jeffudall/Team14/images/20171206_204739.jpg

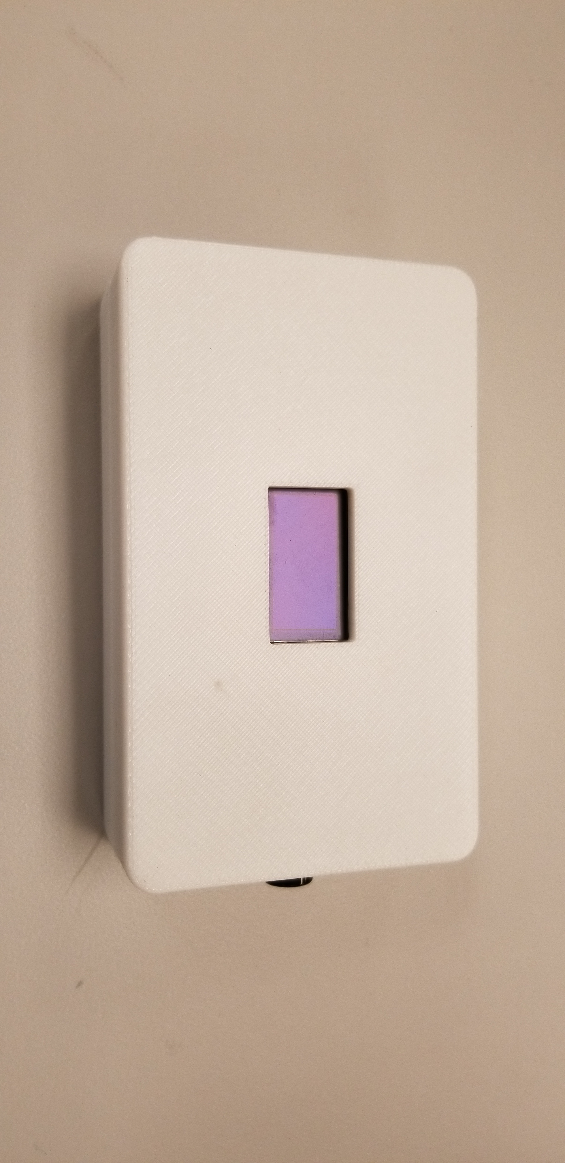
images/20171206_204739.jpg
