jeffudall/Team14/images/20171015_143413.jpg

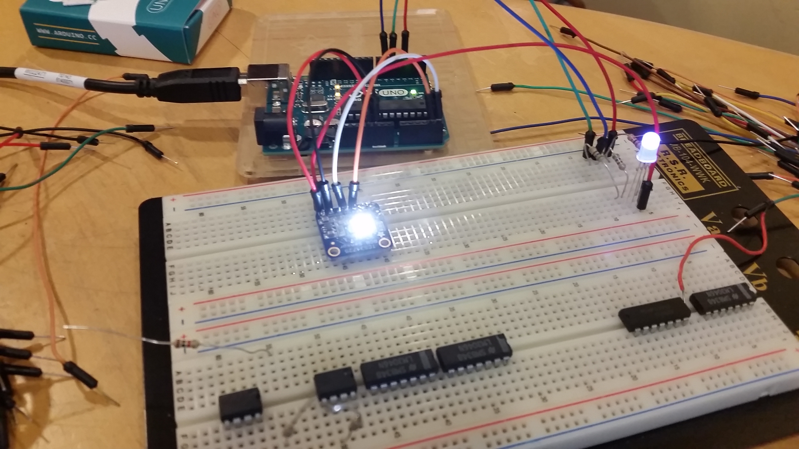
images/20171015_143413.jpg
