jeffudall/Team14/images/20171028_114426.jpg

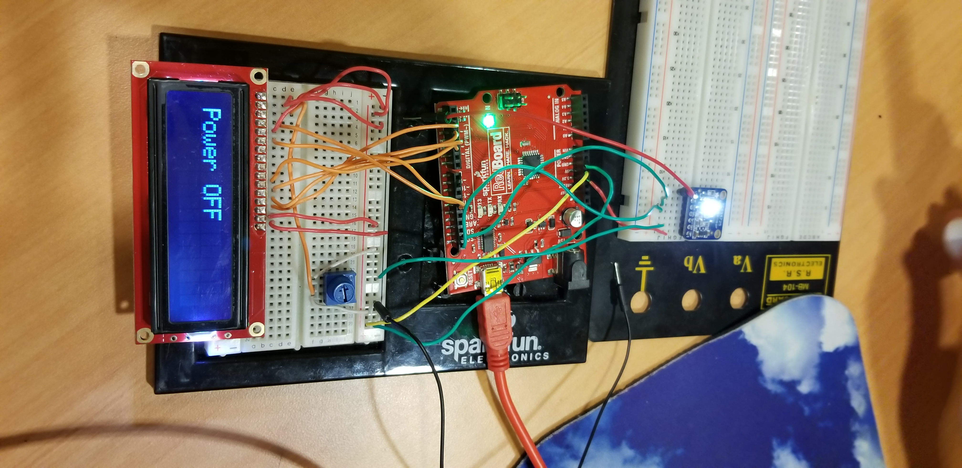
images/20171028_114426.jpg
