jeffudall/Team14/images/20171108_164534.jpg

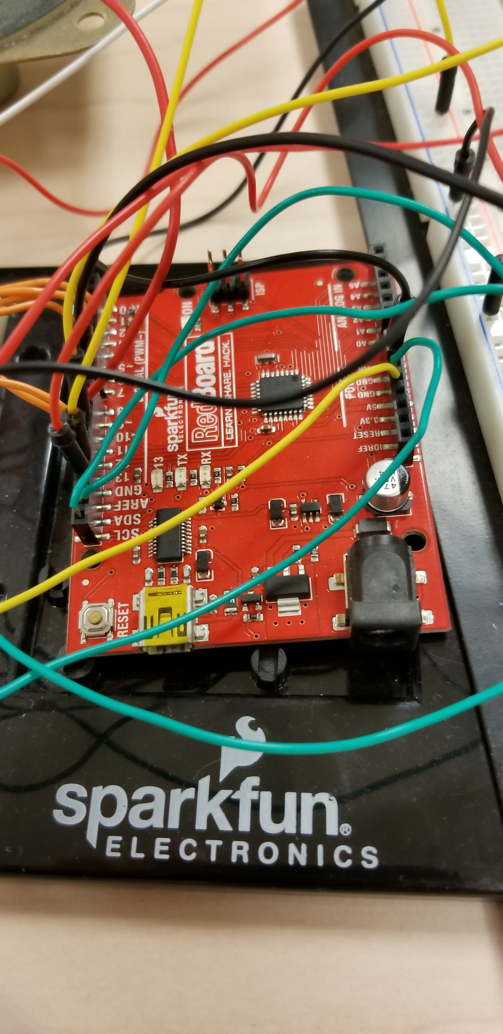
images/20171108_164534.jpg
