jeffudall/Team14/images/20171108_164538.jpg

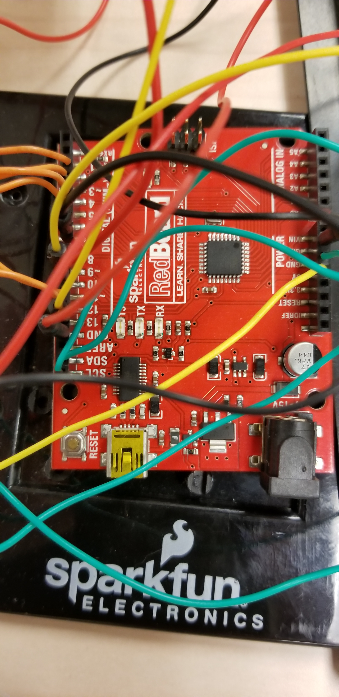
images/20171108_164538.jpg
