jeffudall/Team14/images/20171108_164544.jpg

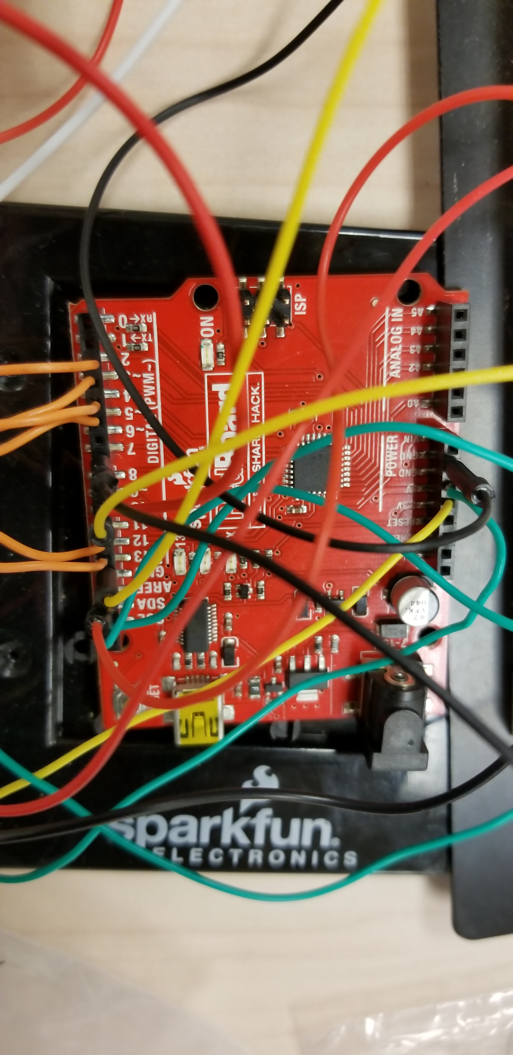
images/20171108_164544.jpg
