jeffudall/Team14/images/20171108_164554.jpg

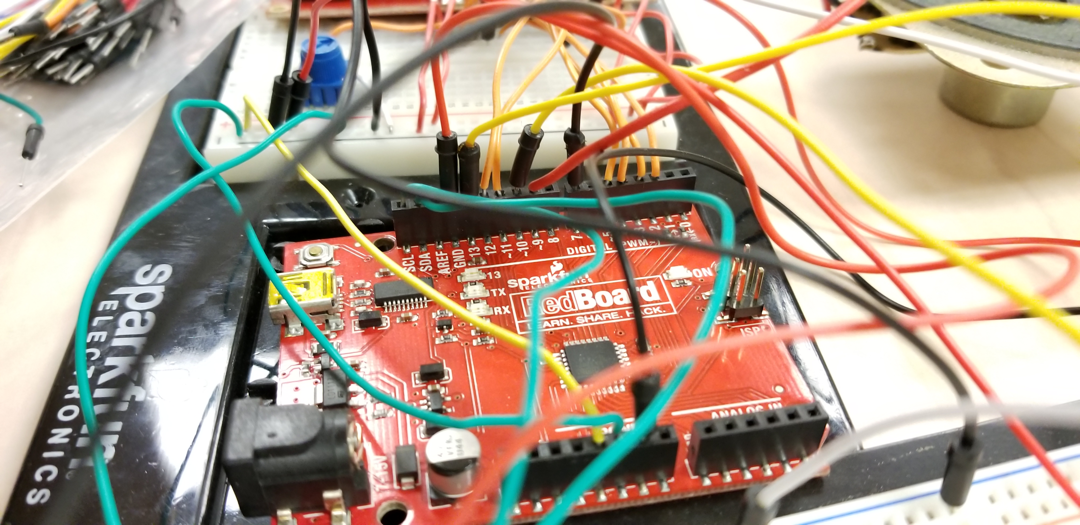
images/20171108_164554.jpg
