jeffudall/Team14/images/20171108_164605.jpg

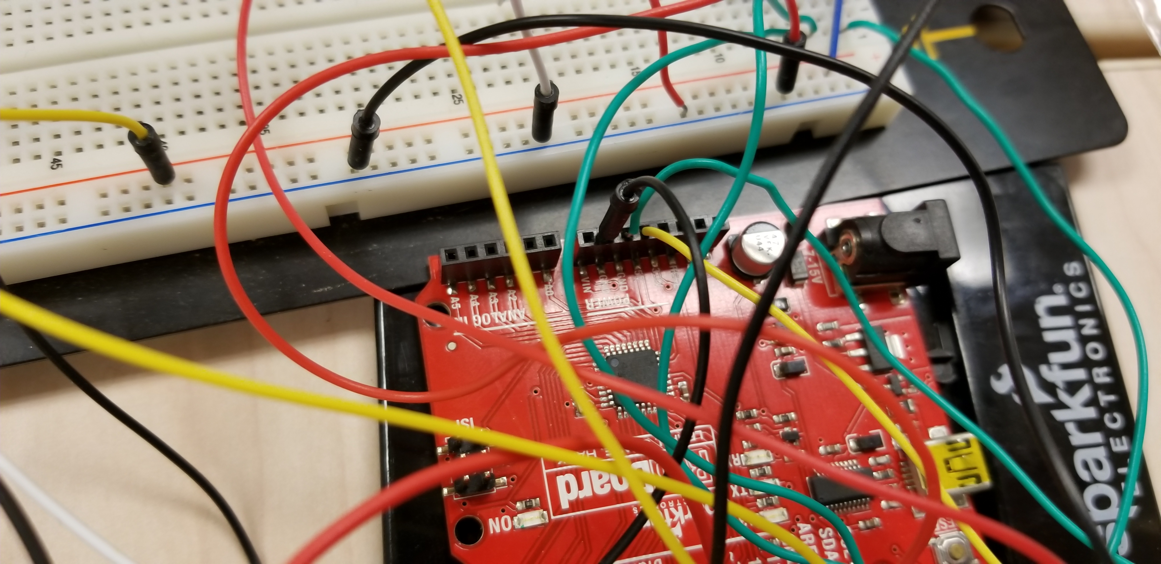
images/20171108_164605.jpg
