jeffudall/Team14/images/20171108_164611.jpg

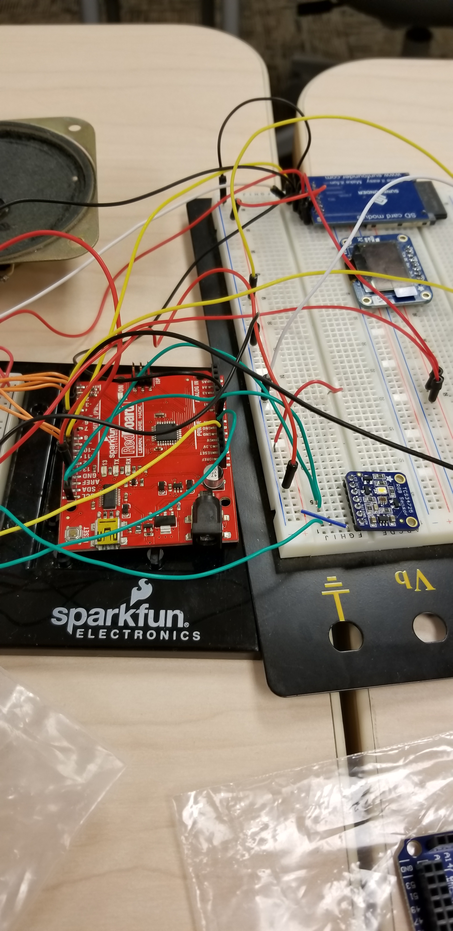
images/20171108_164611.jpg
