jeffudall/Team14/images/20171108_164623.jpg

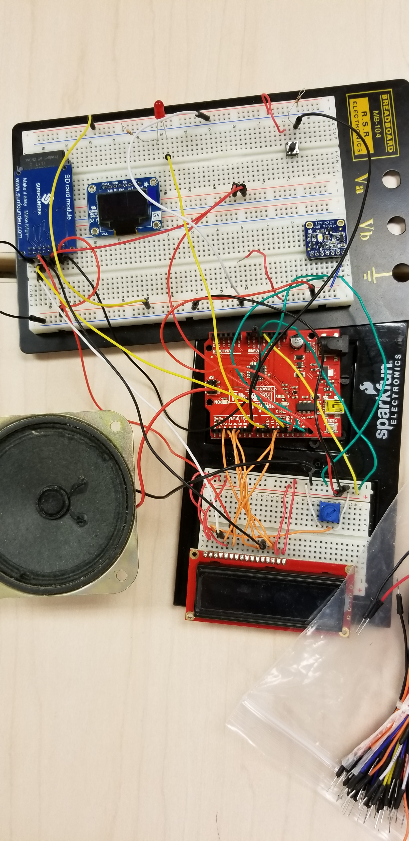
images/20171108_164623.jpg
