jeffudall/Team14/images/20171108_164629.jpg

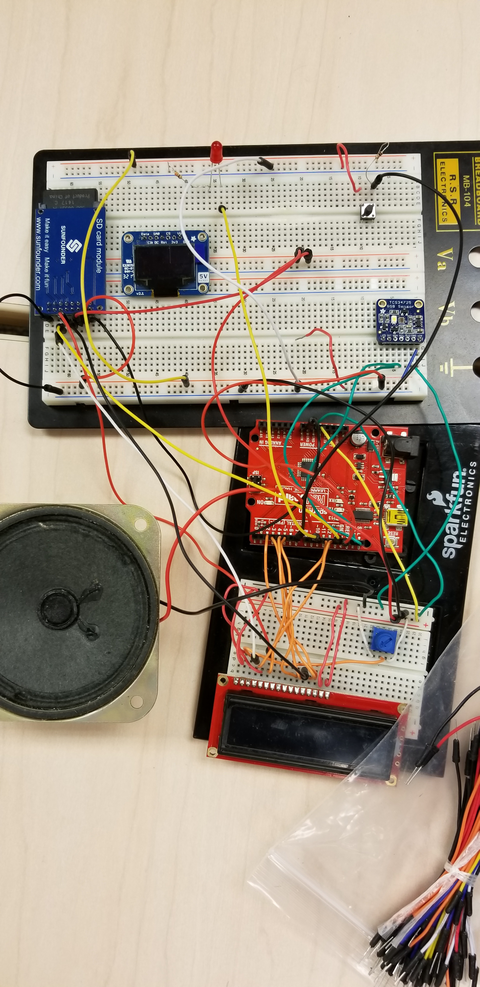
images/20171108_164629.jpg
