jeffudall/Team14/images/20171108_173020.jpg

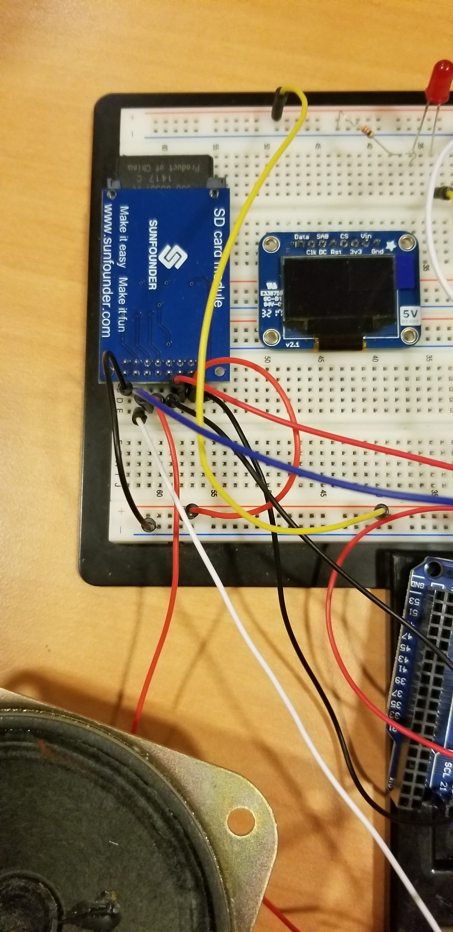
images/20171108_173020.jpg
