jeffudall/Team14/images/20171108_173022.jpg

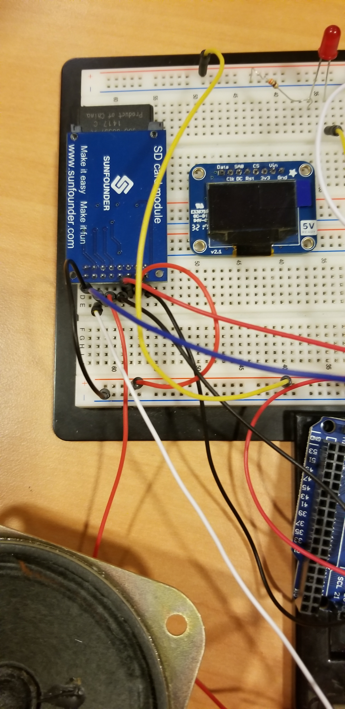
images/20171108_173022.jpg
