jeffudall/Team14/images/20171108_173024.jpg

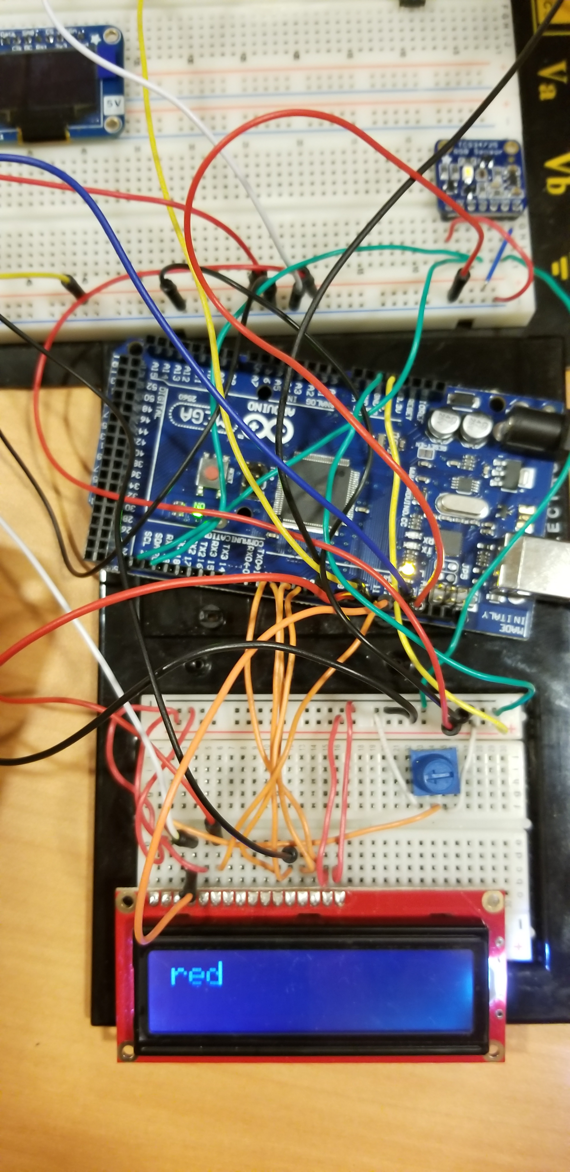
images/20171108_173024.jpg
