jeffudall/Team14/images/20171108_173028.jpg

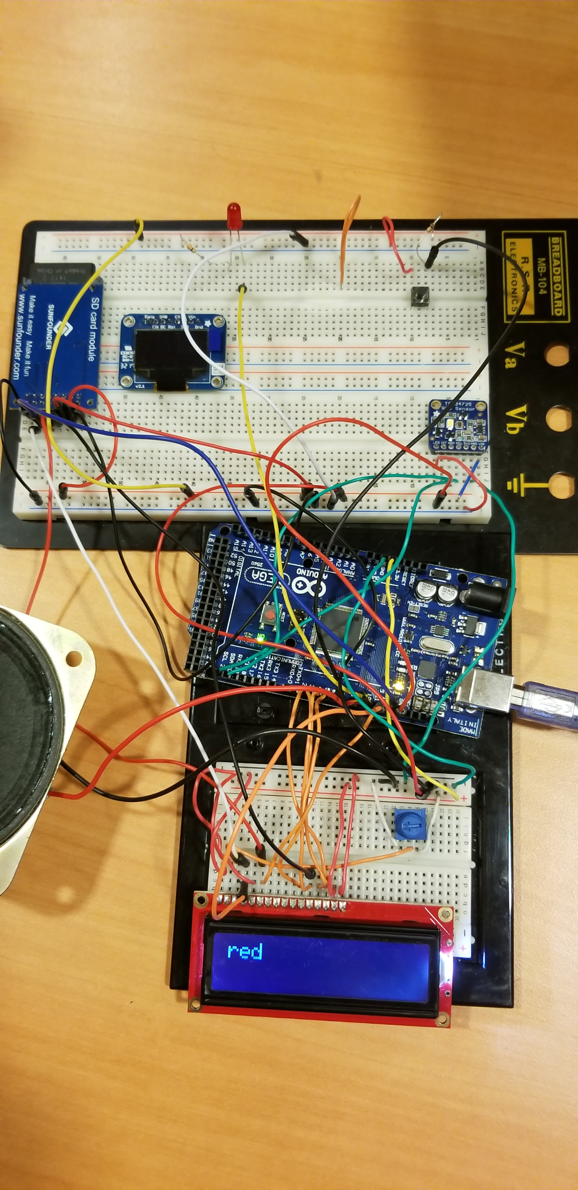
images/20171108_173028.jpg
