jeffudall/Team14/images/20171122_153738.jpg

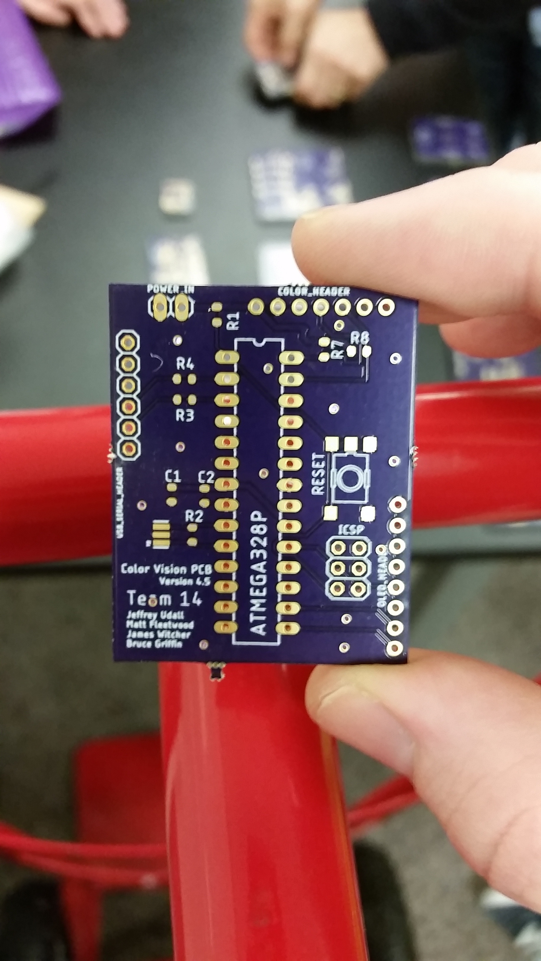
images/20171122_153738.jpg
