jeffudall/Team14/images/20171201_123741.jpg

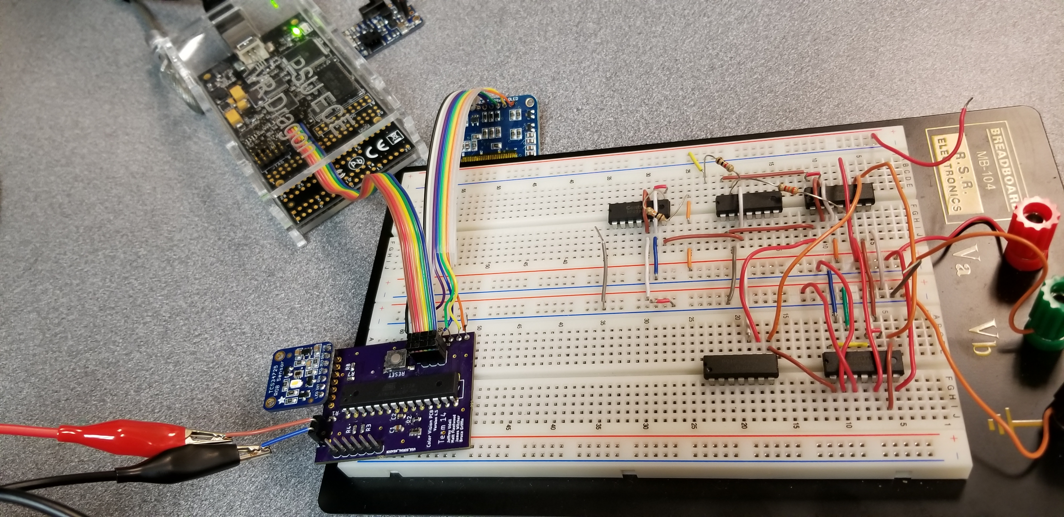
images/20171201_123741.jpg
