jeffudall/Team14/images/20171201_123743.jpg

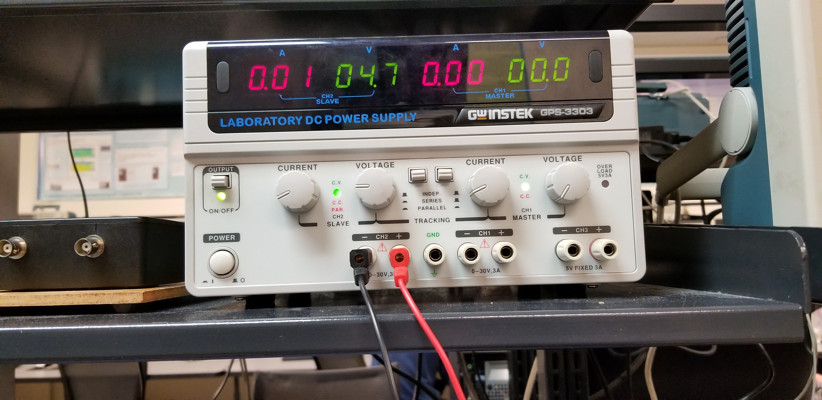
images/20171201_123743.jpg
