jeffudall/Team14/images/20171201_124440.jpg

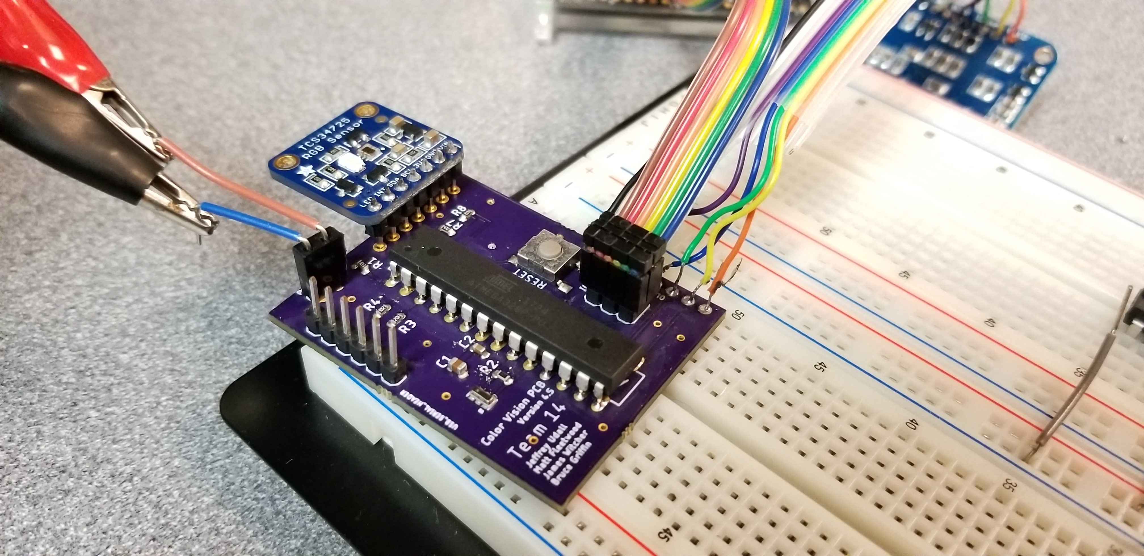
images/20171201_124440.jpg
