jeffudall/Team14/images/20171201_124449.jpg

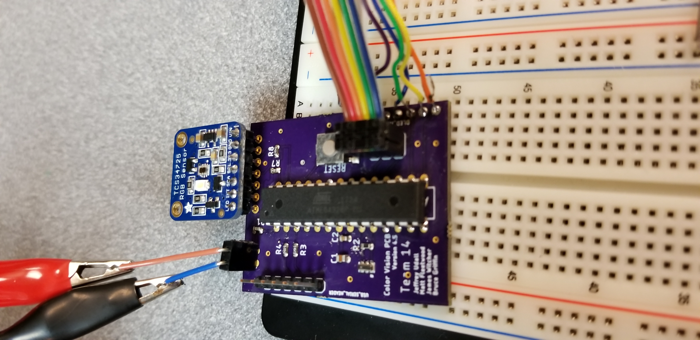
images/20171201_124449.jpg
