jeffudall/Team14/images/20171201_124454.jpg

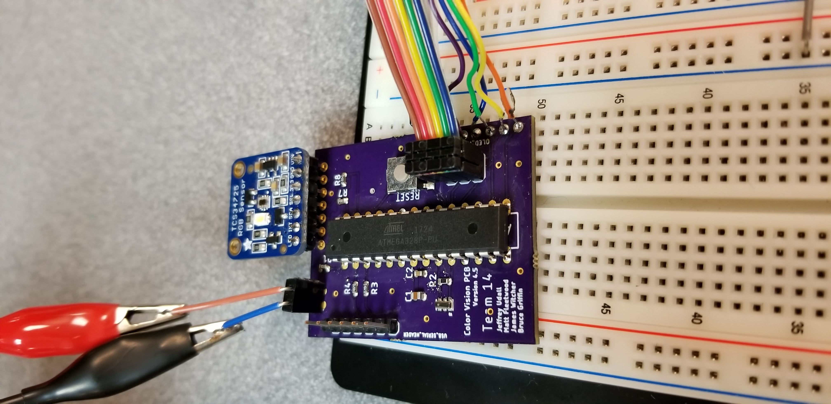
images/20171201_124454.jpg
