jeffudall/Team14/images/20171201_124501.jpg

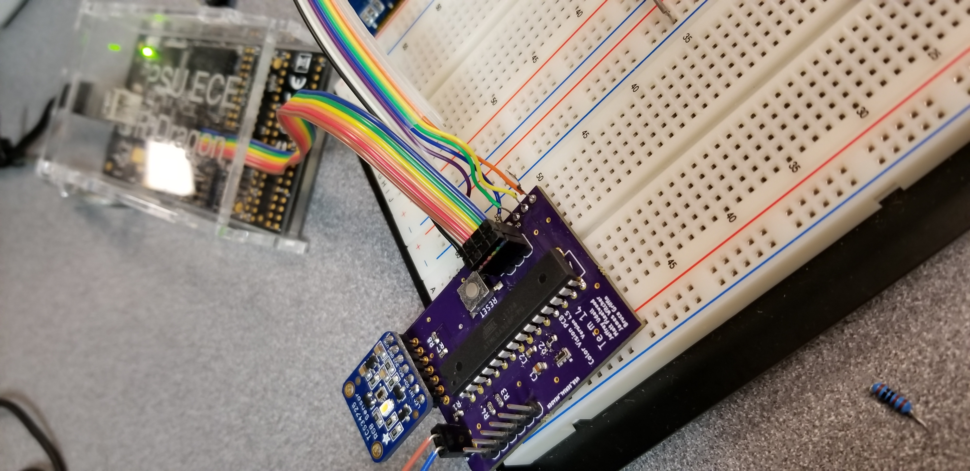
images/20171201_124501.jpg
