jeffudall/Team14/images/20171201_124509.jpg

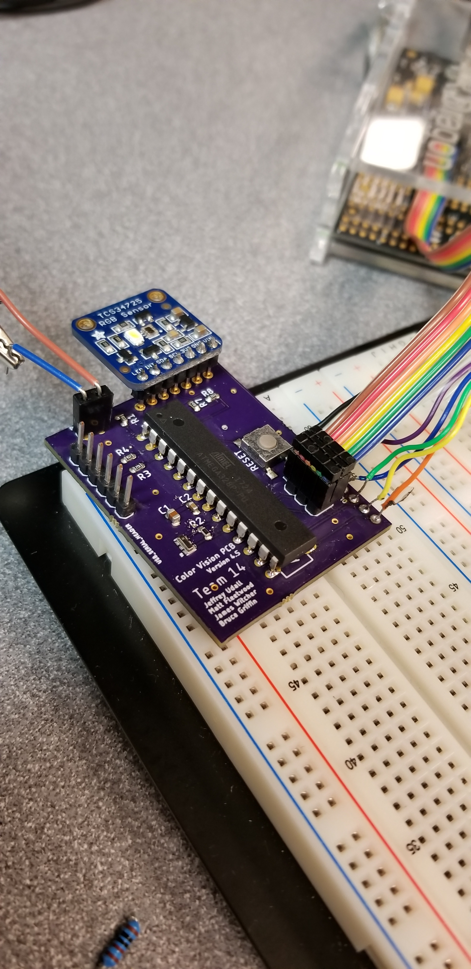
images/20171201_124509.jpg
