jeffudall/Team14/images/20171201_125054.jpg

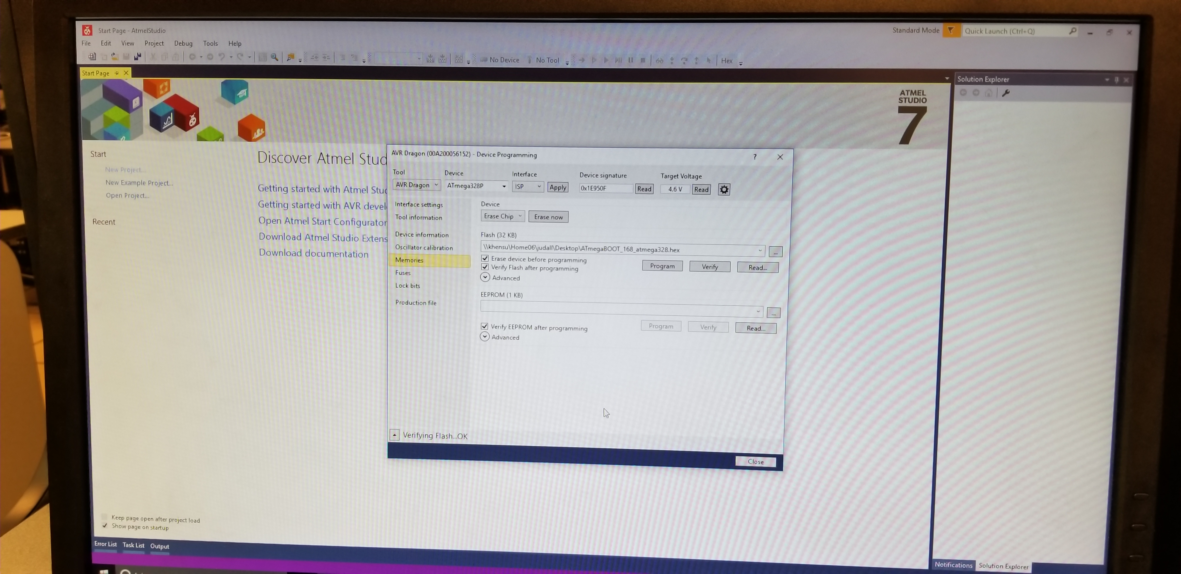
images/20171201_125054.jpg
