jeffudall/Team14/images/20171201_125115.jpg

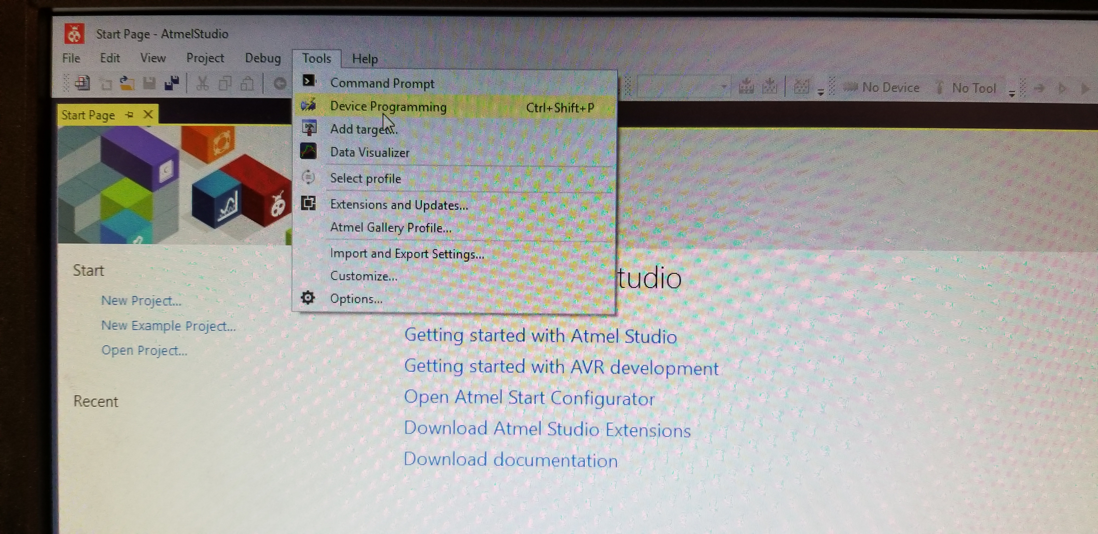
images/20171201_125115.jpg
