jeffudall/Team14/images/20171201_125118.jpg

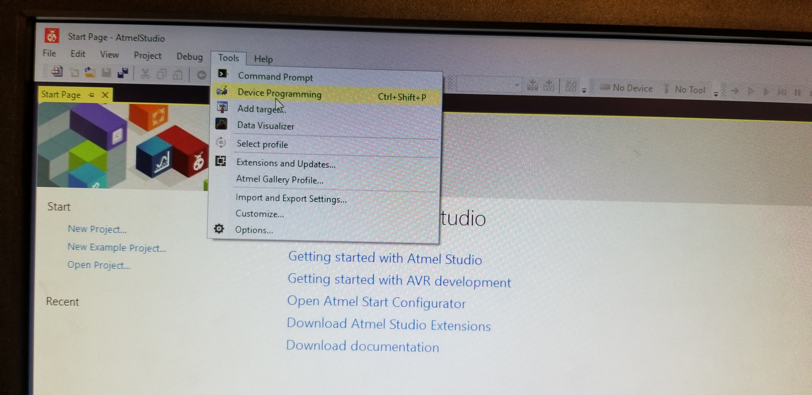
images/20171201_125118.jpg
