jeffudall/Team14/images/20171201_192157.jpg

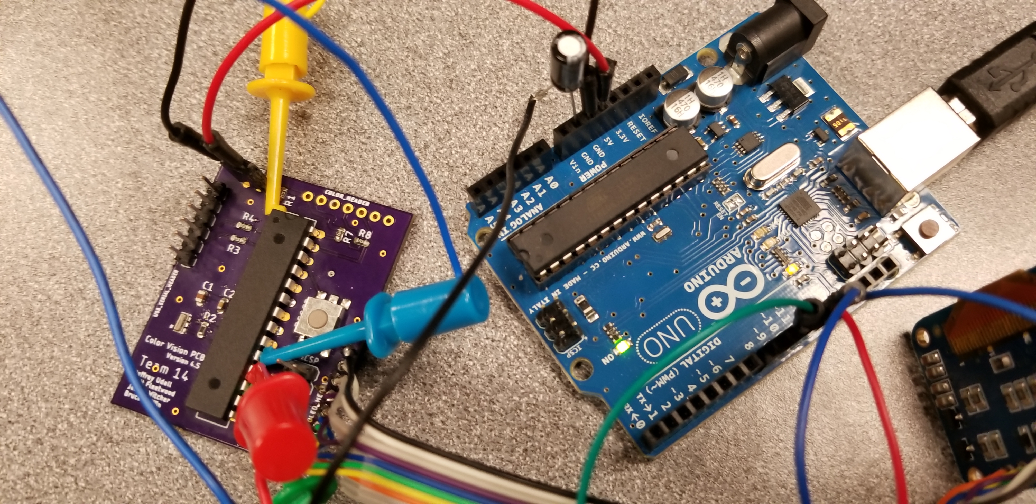
images/20171201_192157.jpg
