jeffudall/Team14/images/20171201_192206.jpg

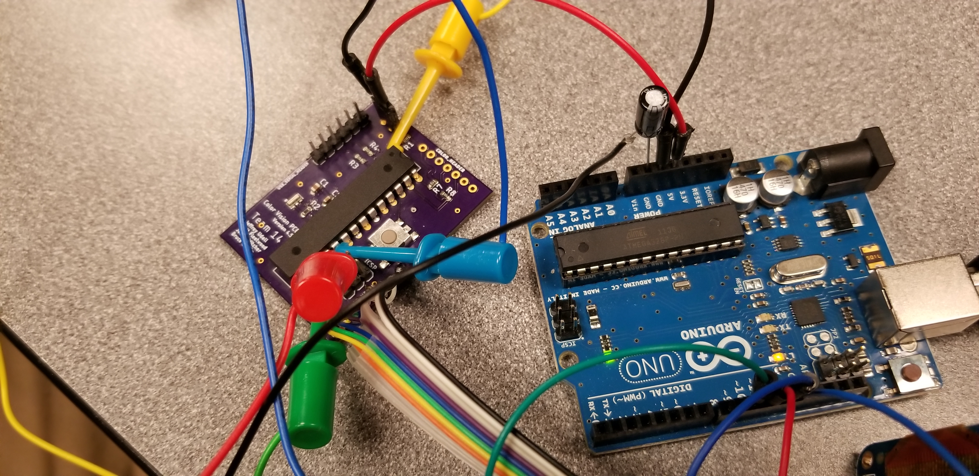
images/20171201_192206.jpg
