jeffudall/Team14/images/20171201_192208.jpg

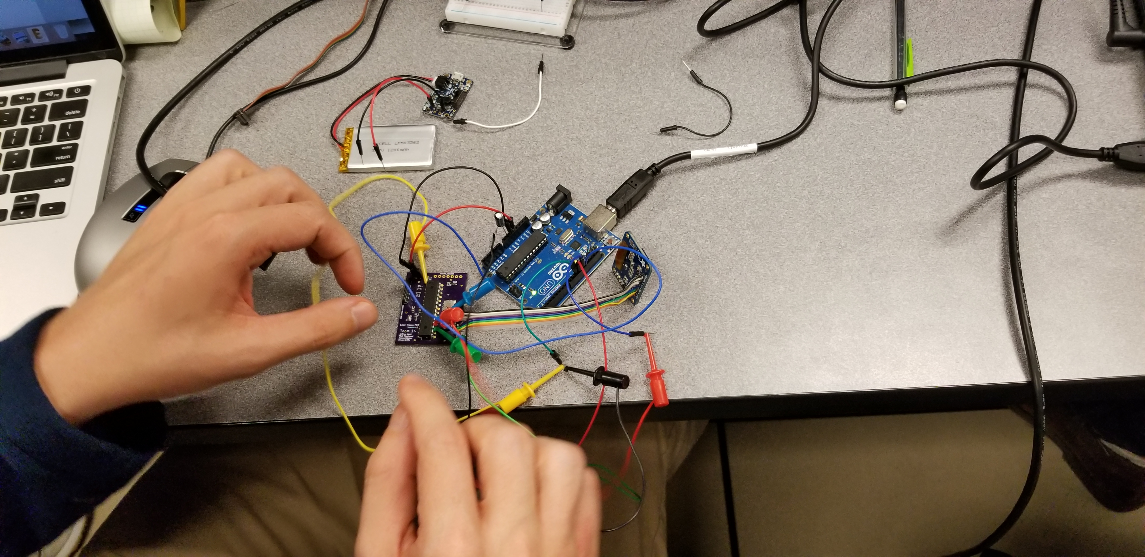
images/20171201_192208.jpg
