jeffudall/Team14/images/20171201_194534.jpg

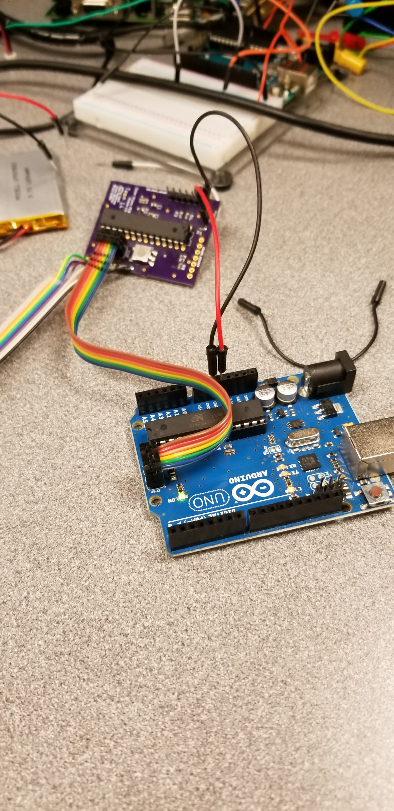
images/20171201_194534.jpg
