jeffudall/Team14/images/20171203_112600.jpg

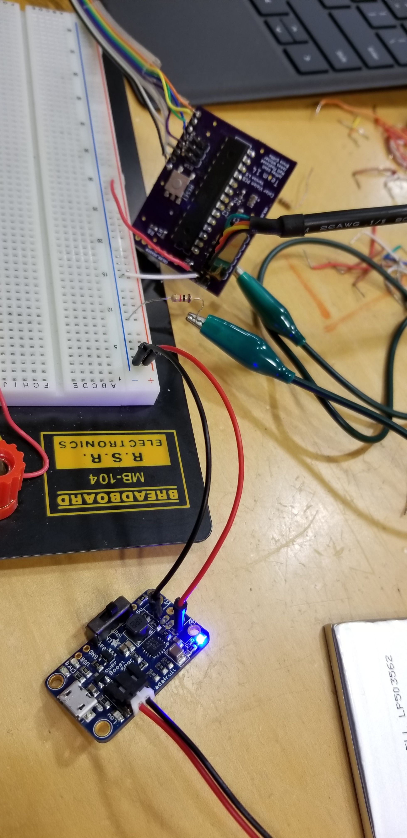
images/20171203_112600.jpg
