jeffudall/Team14/images/20171203_112827.jpg

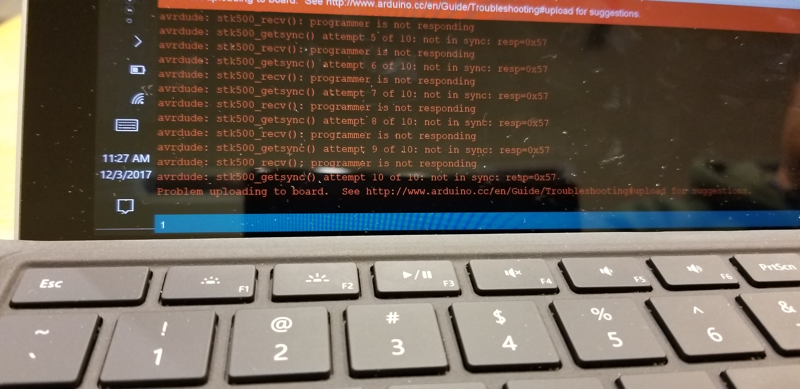
images/20171203_112827.jpg
