jeffudall/Team14/images/20171203_142456.jpg

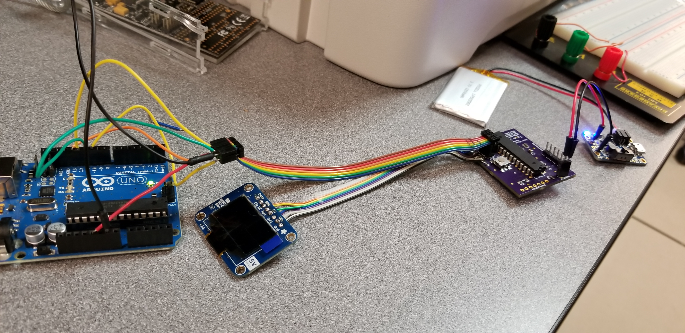
images/20171203_142456.jpg
