jeffudall/Team14/images/20171203_142506.jpg

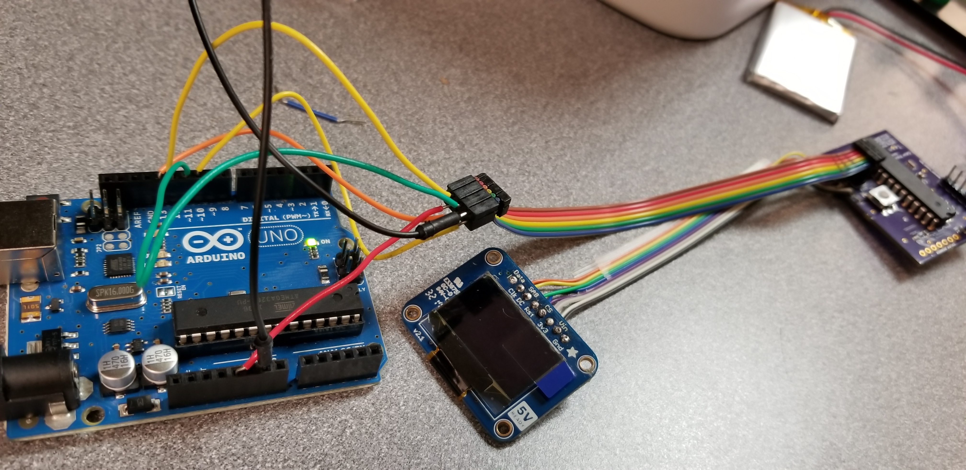
images/20171203_142506.jpg
