jeffudall/Team14/images/20171203_142516.jpg

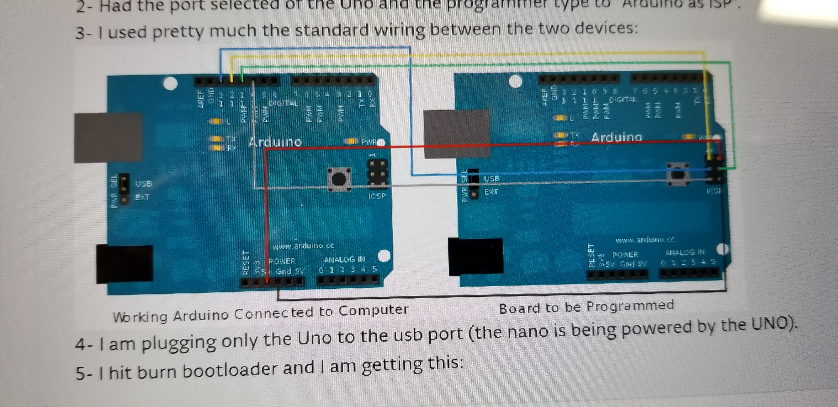
images/20171203_142516.jpg
