jeffudall/Team14/images/20171203_143118.jpg

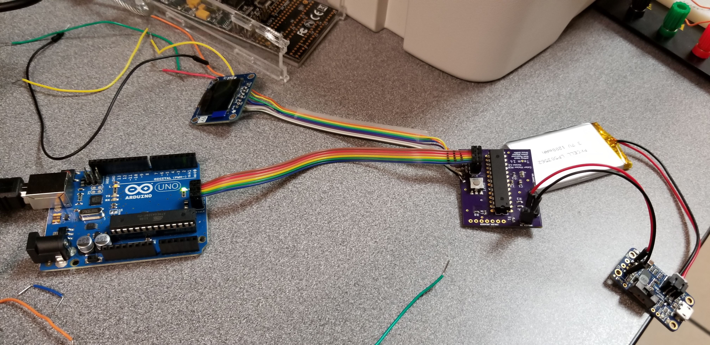
images/20171203_143118.jpg
