jeffudall/Team14/images/20171203_143120.jpg

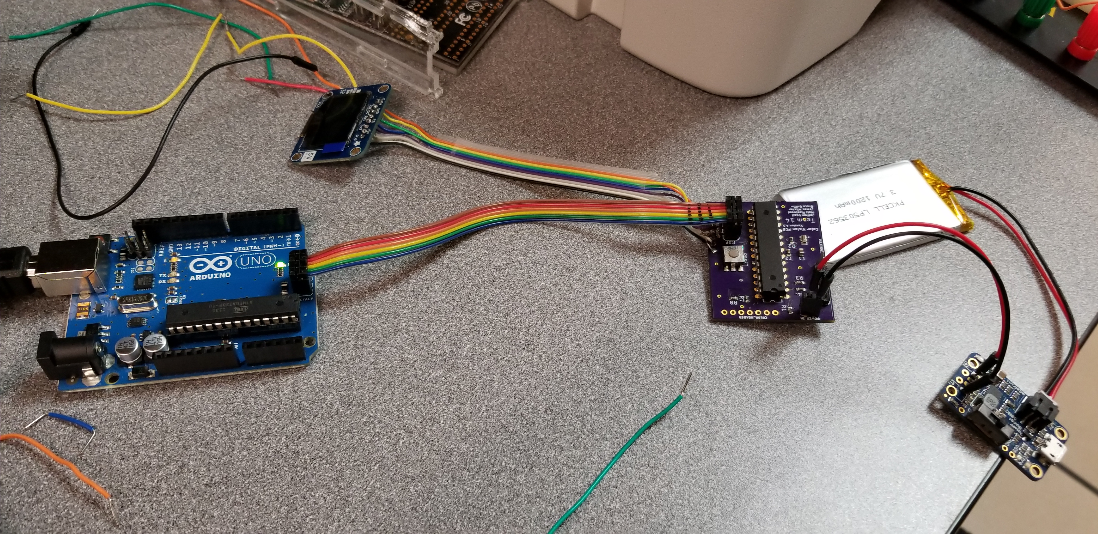
images/20171203_143120.jpg
