jeffudall/Team14/images/20171203_143124.jpg

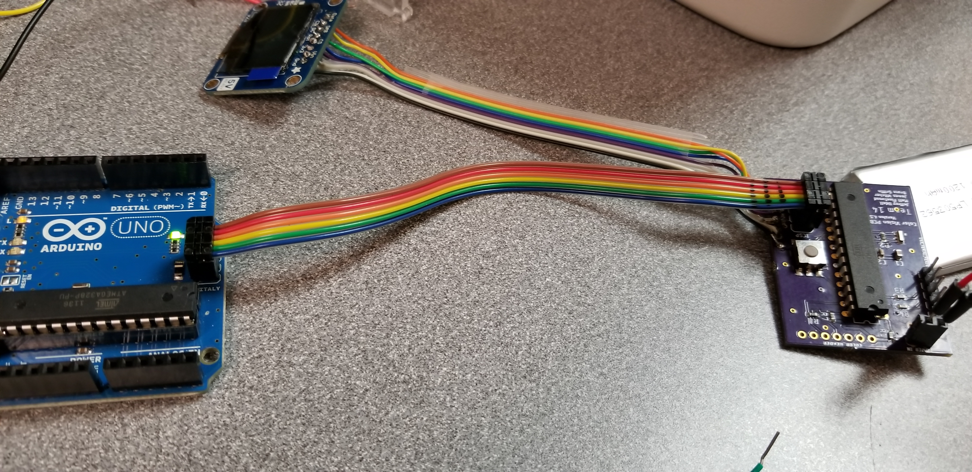
images/20171203_143124.jpg
