jeffudall/Team14/images/20171205_124026.jpg

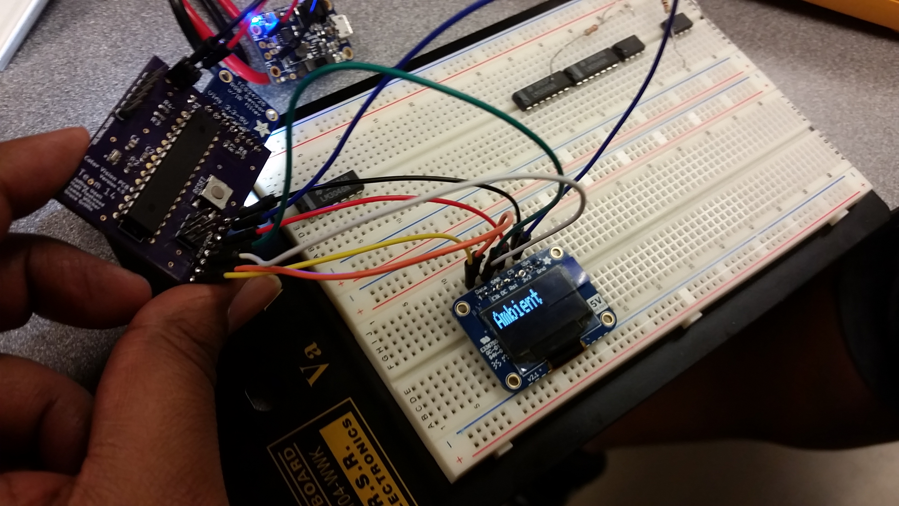
images/20171205_124026.jpg
