jeffudall/Team14/images/20171205_190306.jpg

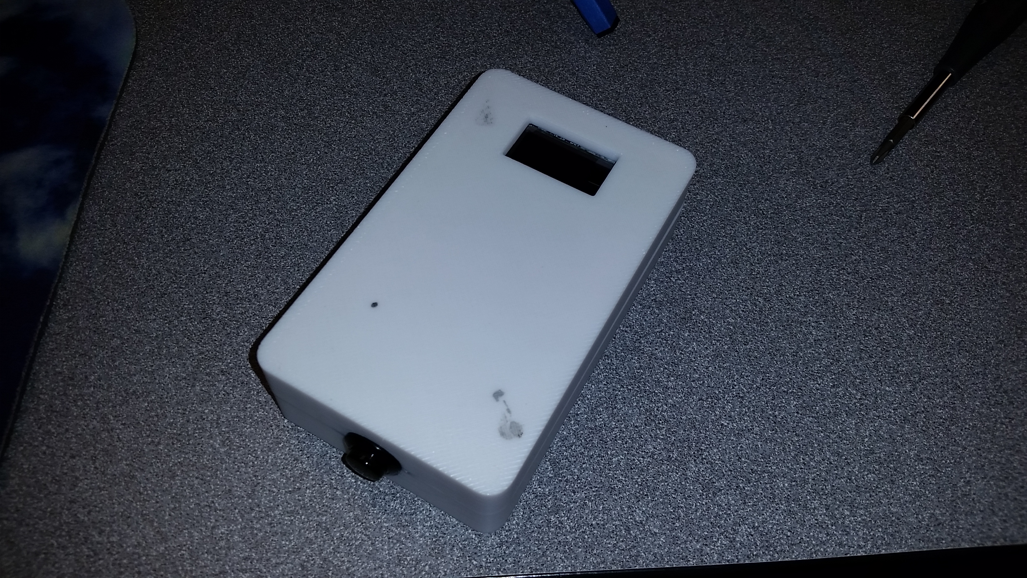
images/20171205_190306.jpg
