jeffudall/Team14/images/20171206_204804.jpg

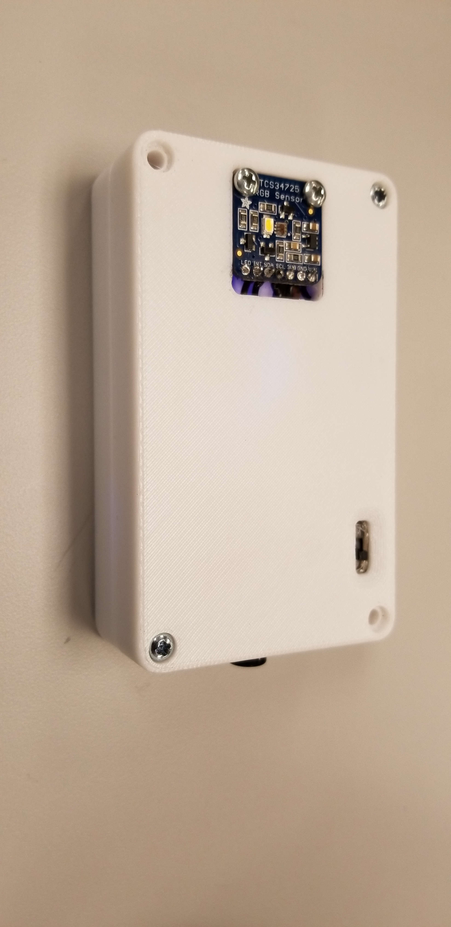
images/20171206_204804.jpg
