jeffudall/Team14/images/20171206_204812.jpg

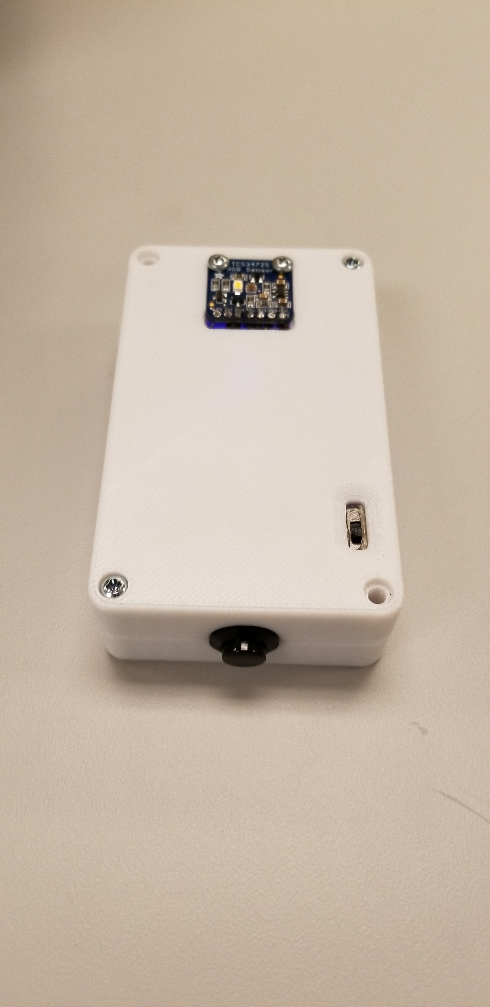
images/20171206_204812.jpg
