jeffudall/Team14/images/ATMEGA328chip.JPG

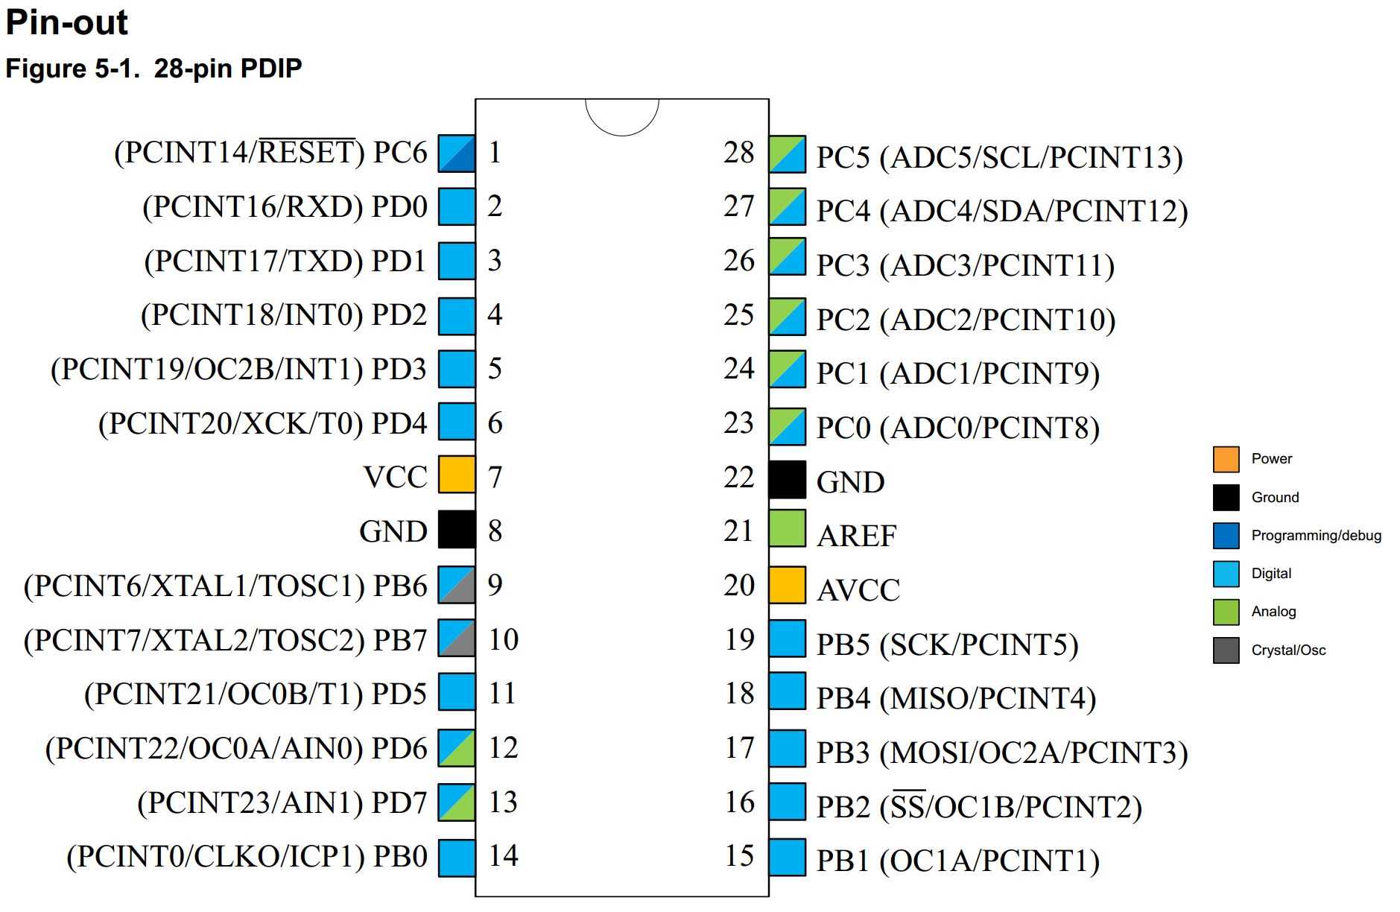
images/ATMEGA328chip.JPG
