jeffudall/Team14/images/blue.jpg

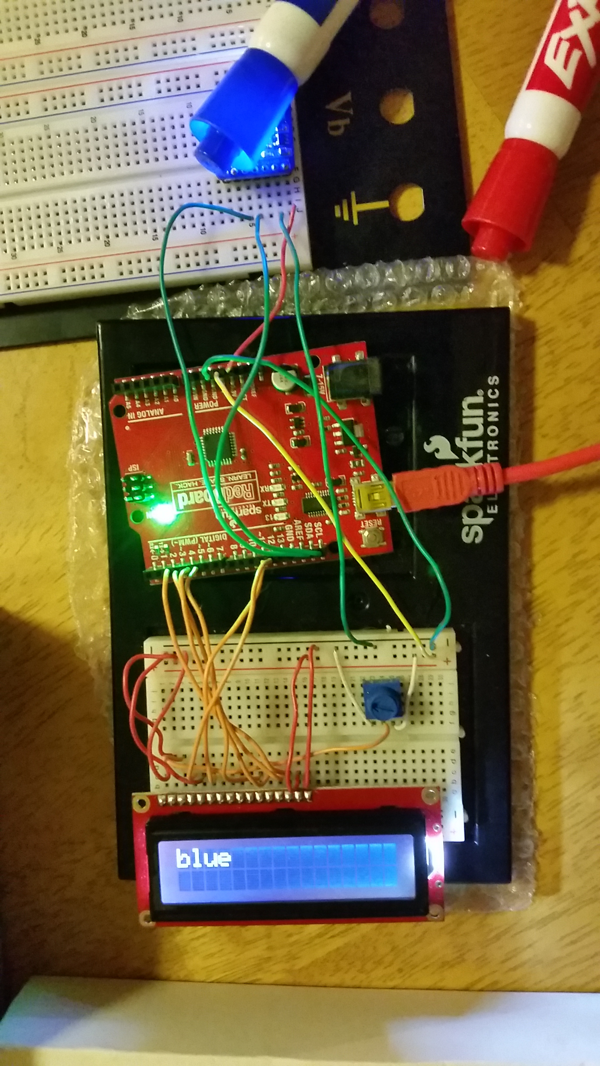
images/blue.jpg
