jeffudall/Team14/images/BoM_final.png

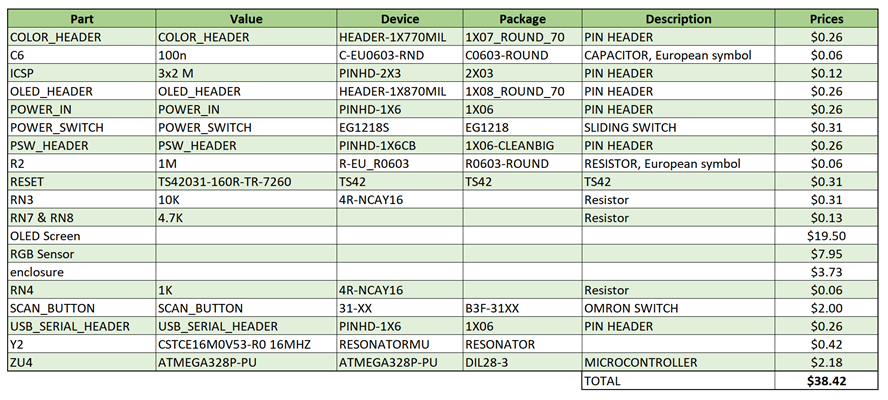
images/BoM_final.png
