jeffudall/Team14/images/cmd_line_audio.png

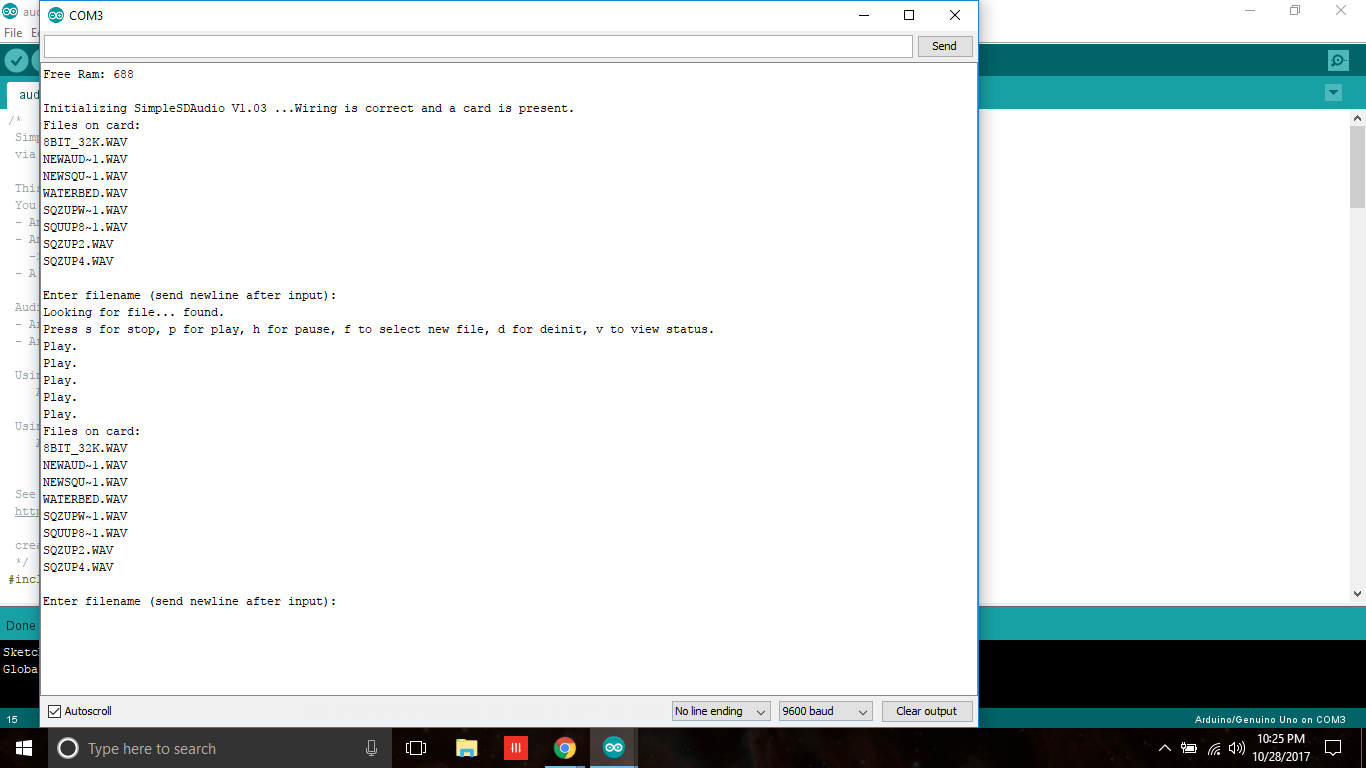
images/cmd_line_audio.png
