jeffudall/Team14/images/color_chooser_sketch.PNG

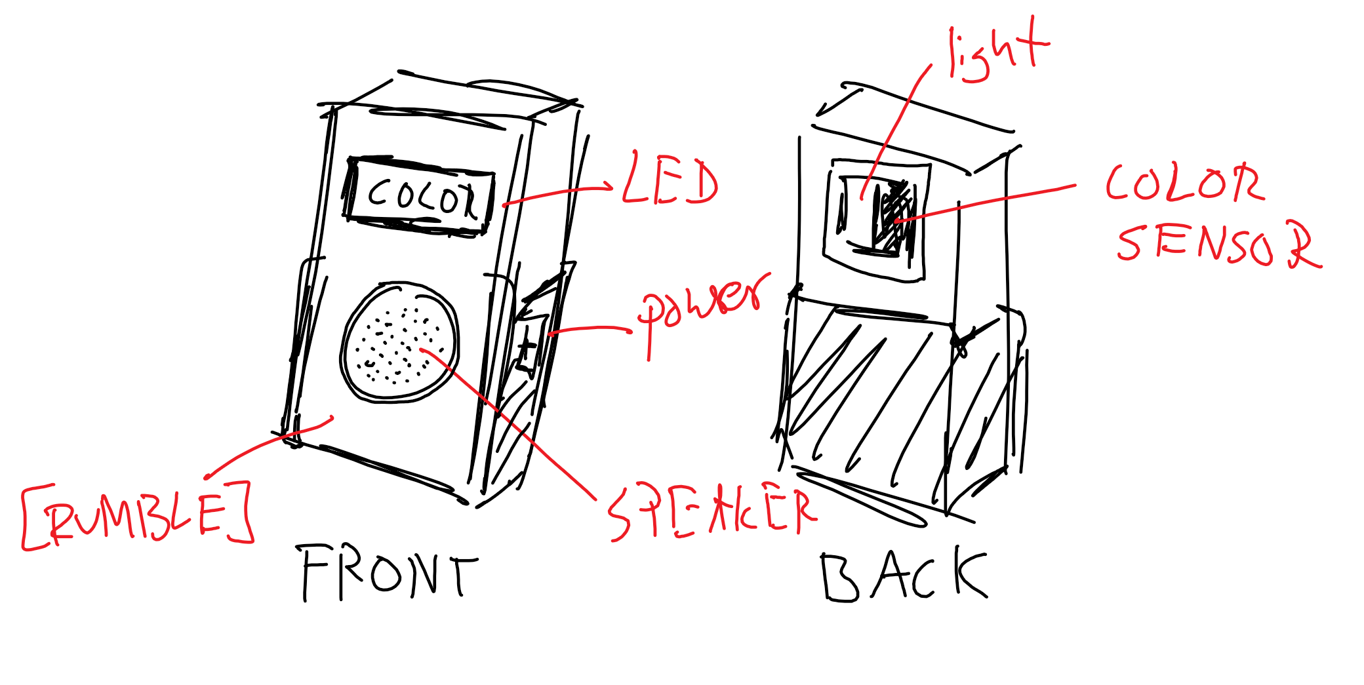
images/color_chooser_sketch.PNG
