jeffudall/Team14/images/color_sensor.JPG

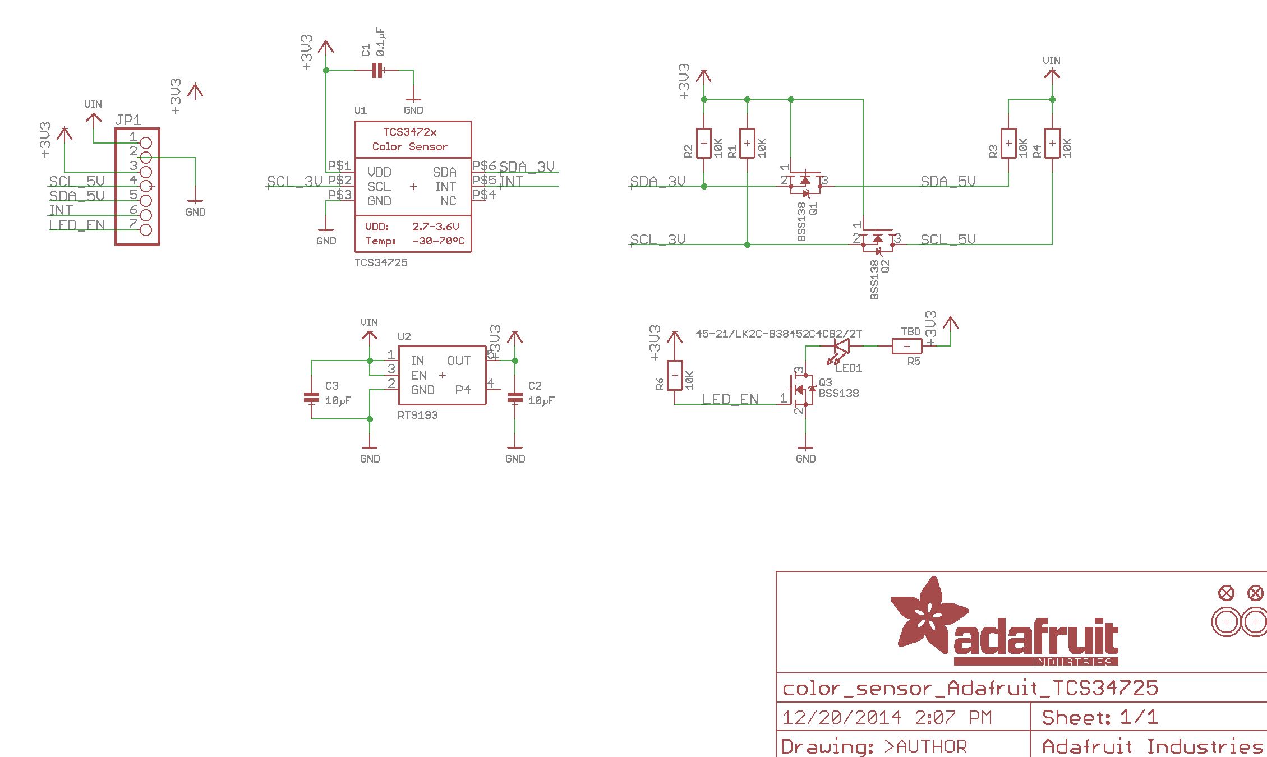
images/color_sensor.JPG
