jeffudall/Team14/images/Enclosure Sensor side V1.JPG

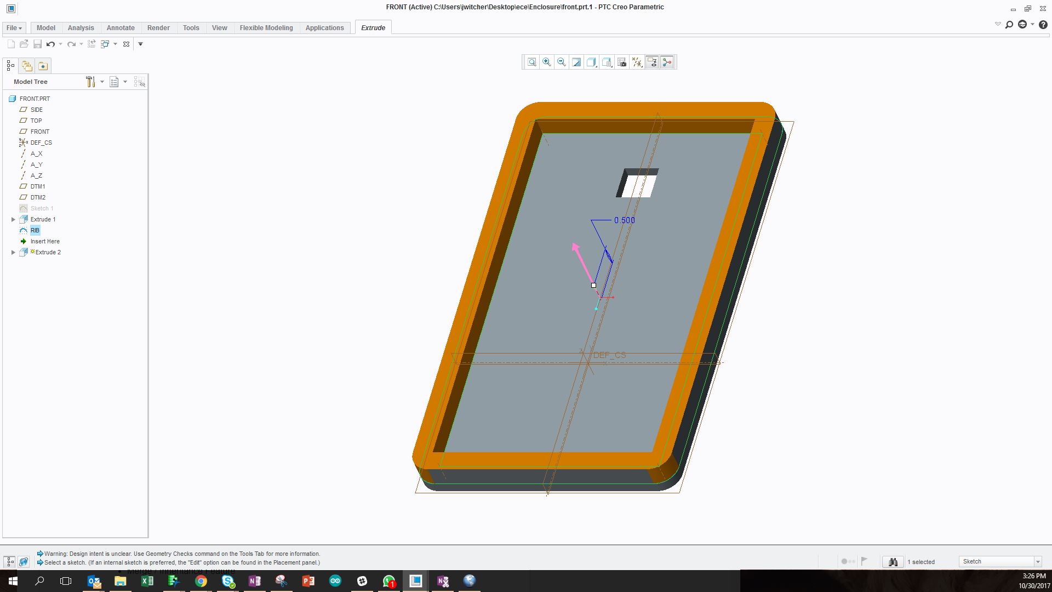
images/Enclosure Sensor side V1.JPG
