jeffudall/Team14/images/Enclosure Speaker_LCD V1.JPG

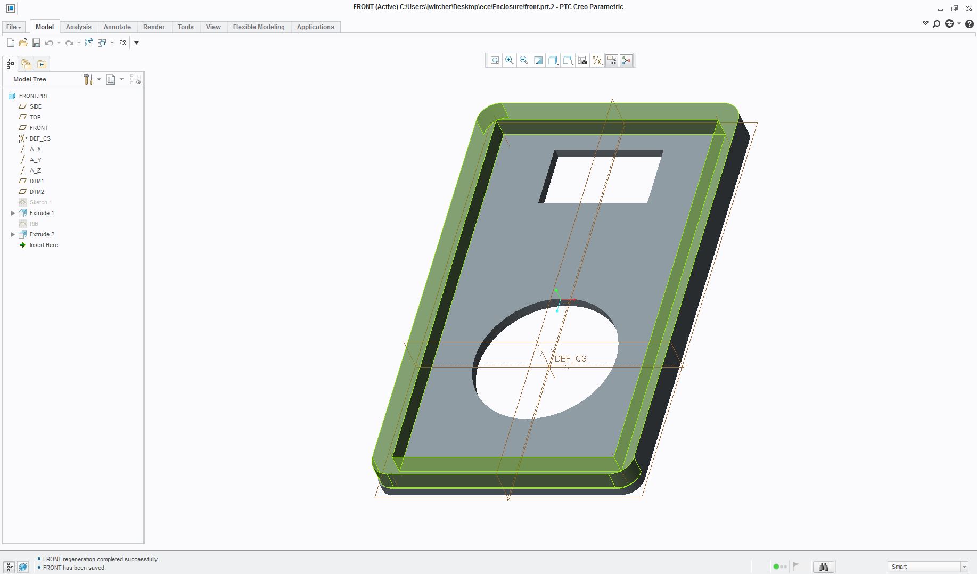
images/Enclosure Speaker_LCD V1.JPG
