jeffudall/Team14/images/enclosure_back_V2.JPG

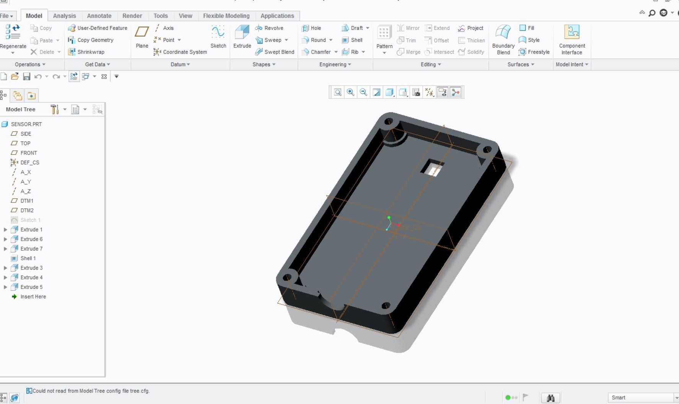
images/enclosure_back_V2.JPG
