jeffudall/Team14/images/enclosure_front_V2.JPG

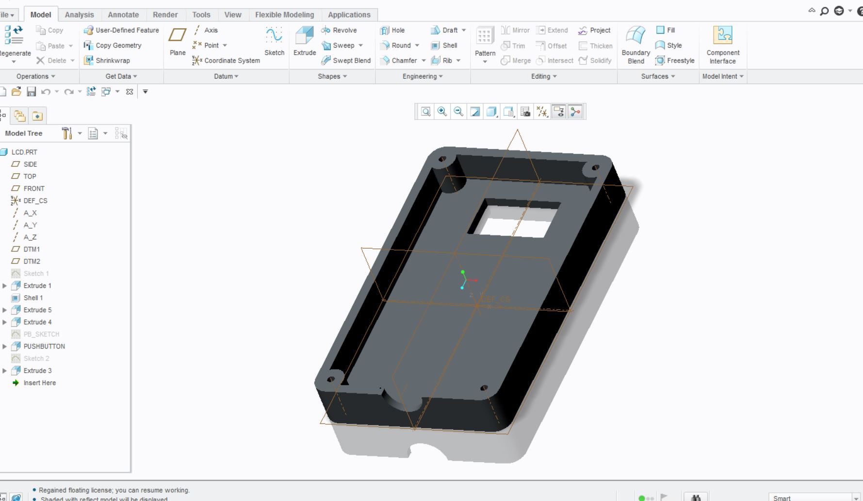
images/enclosure_front_V2.JPG
