jeffudall/Team14/images/final_device_01.JPG

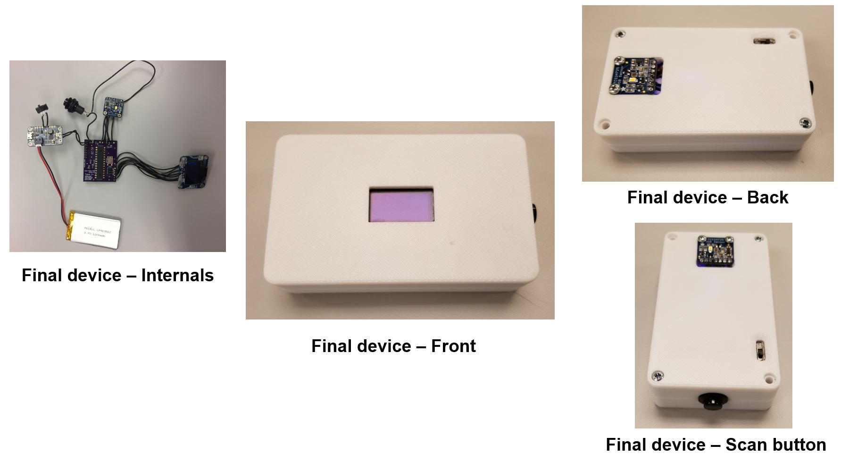
images/final_device_01.JPG
