jeffudall/Team14/images/green.jpg

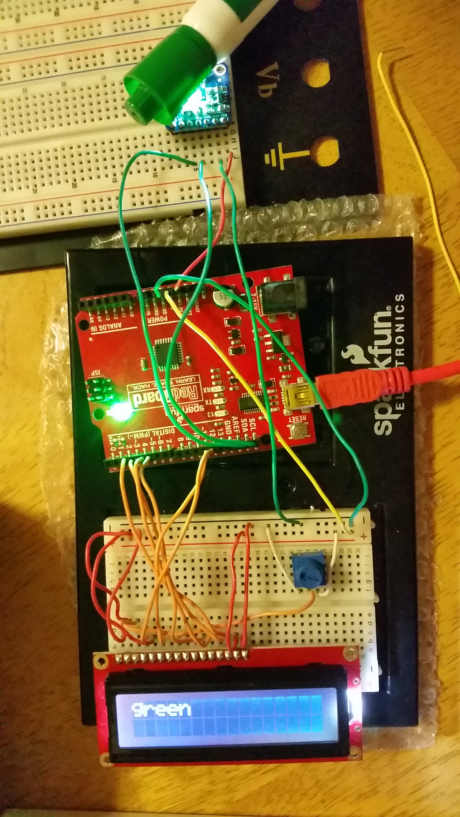
images/green.jpg
