jeffudall/Team14/images/HW5_group14_draft01-2.jpg

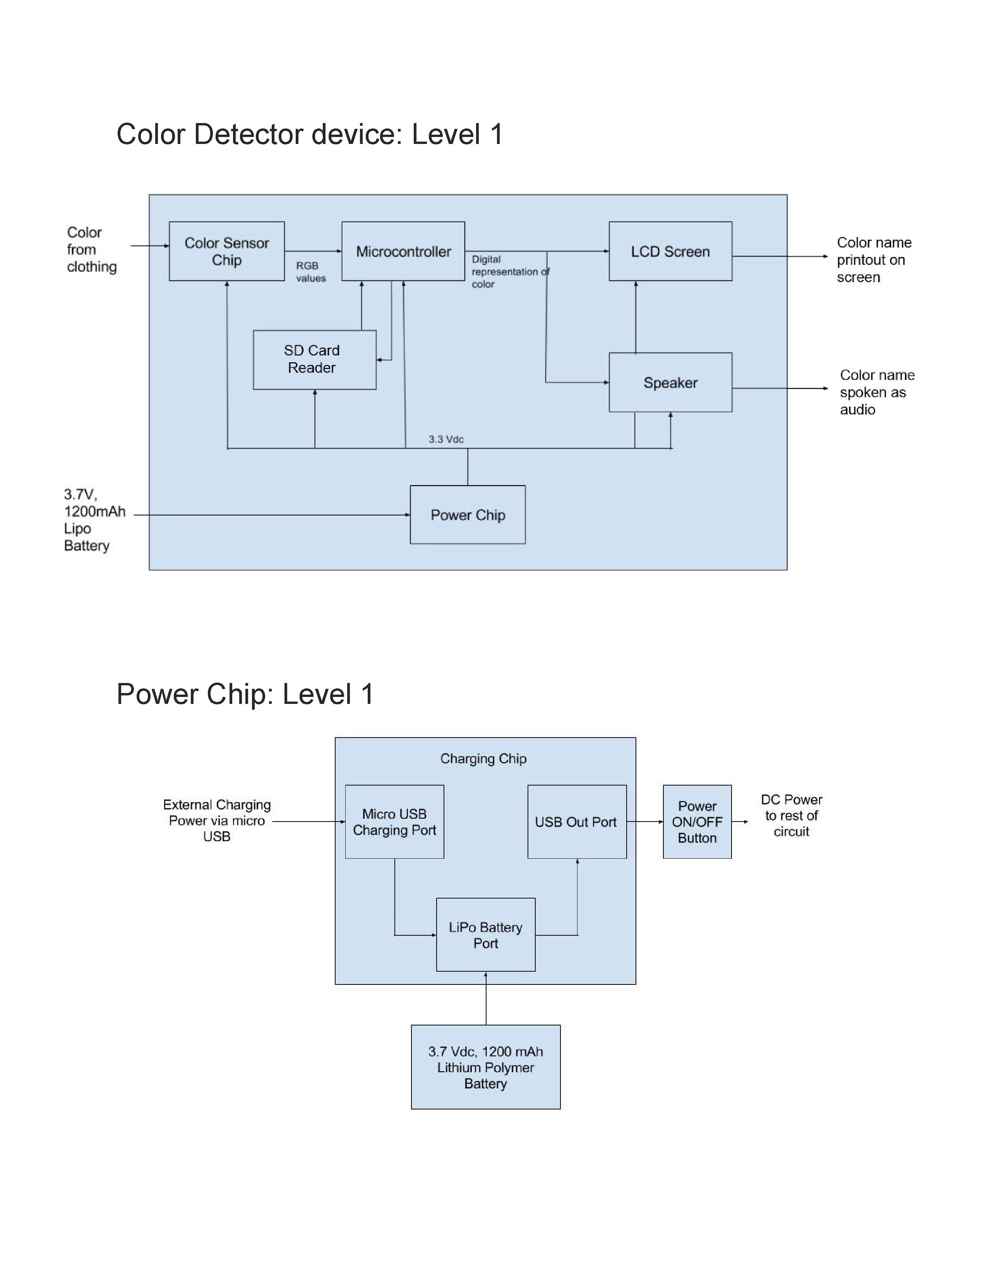
images/HW5_group14_draft01-2.jpg
