jeffudall/Team14/images/IMG_0013.JPG

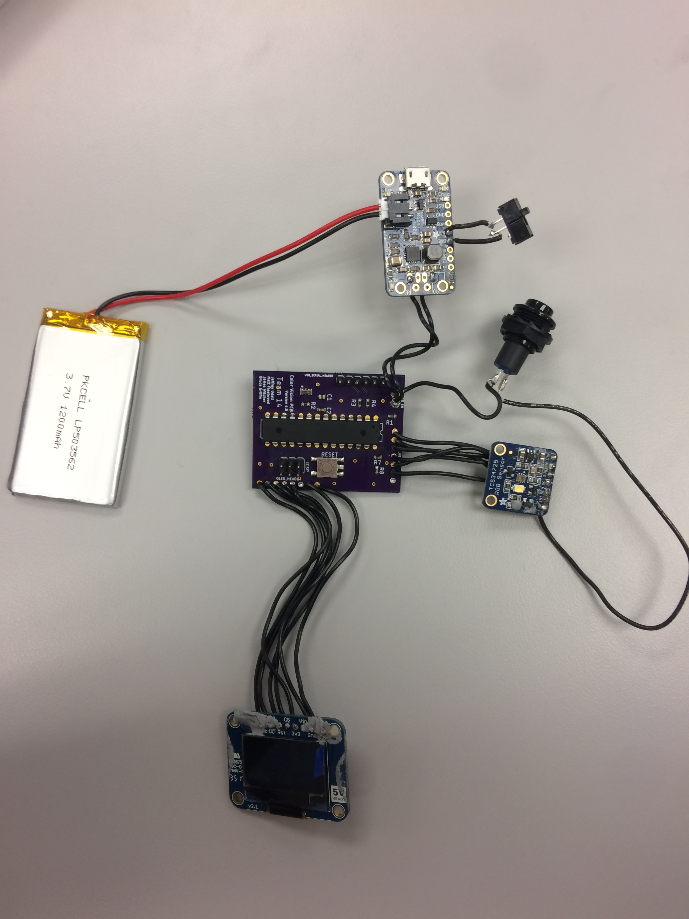
images/IMG_0013.JPG
