jeffudall/Team14/images/IMG_20171129_113057.jpg

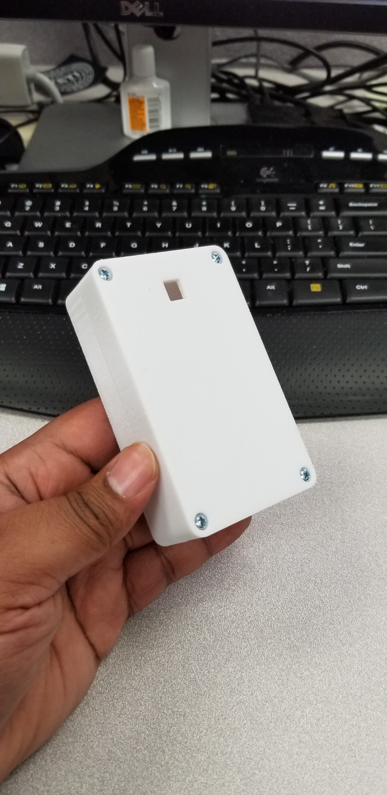
images/IMG_20171129_113057.jpg
