jeffudall/Team14/images/IMG_20171129_113114.jpg

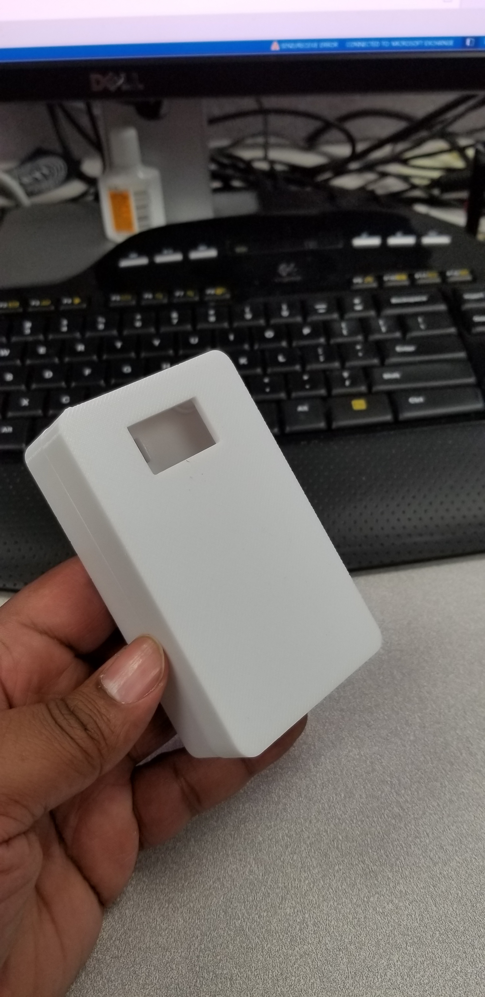
images/IMG_20171129_113114.jpg
