jeffudall/Team14/images/IMG_20171129_113309.jpg

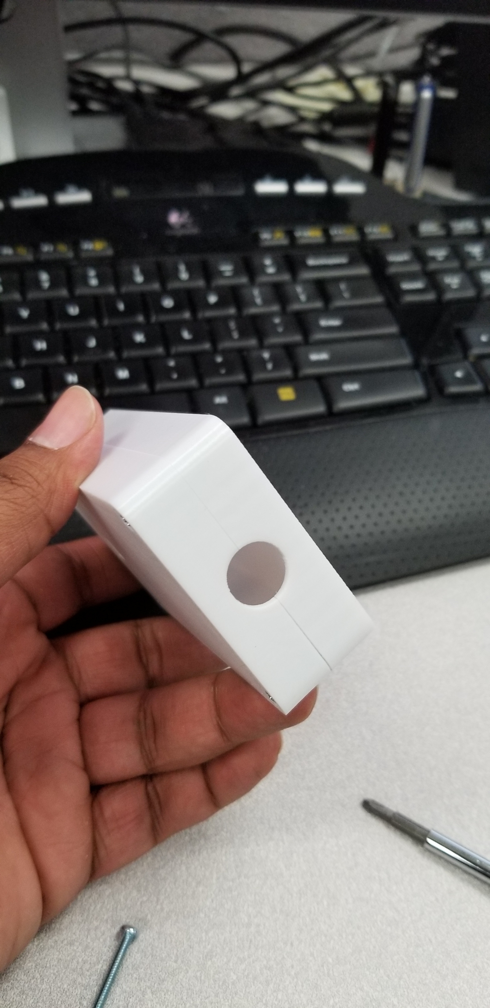
images/IMG_20171129_113309.jpg
