jeffudall/Team14/images/IMG_20171129_114544.jpg

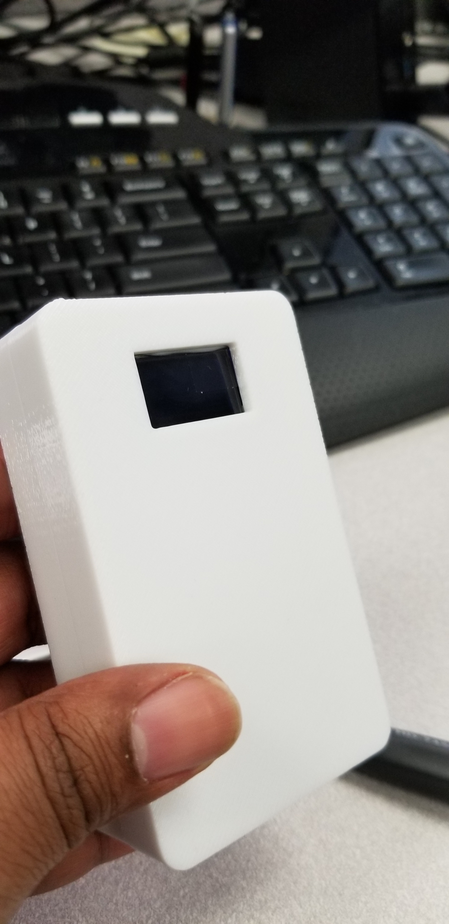
images/IMG_20171129_114544.jpg
