jeffudall/Team14/images/IMG_20171129_114557.jpg

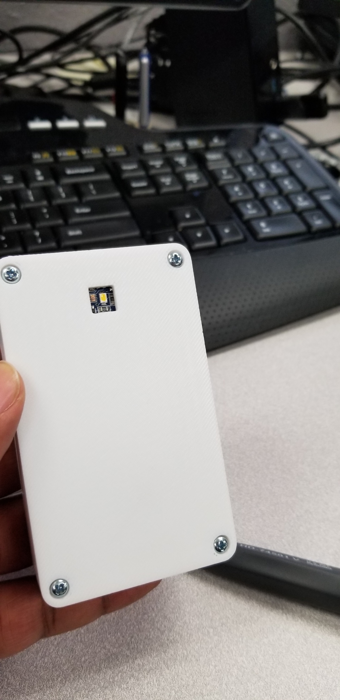
images/IMG_20171129_114557.jpg
