jeffudall/Team14/images/IMG_20171130_200244.jpg

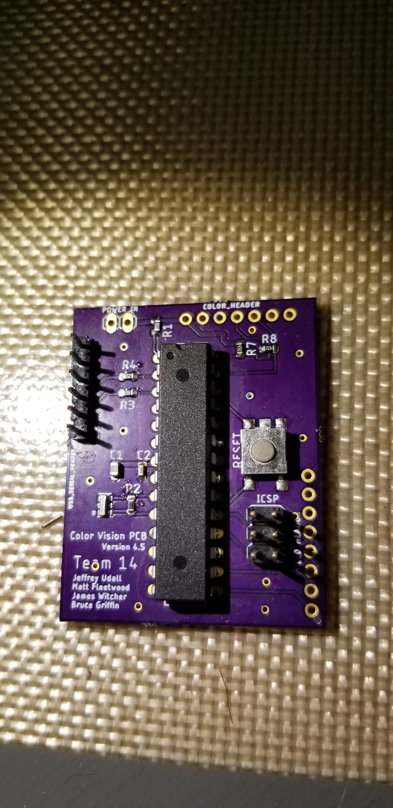
images/IMG_20171130_200244.jpg
