jeffudall/Team14/images/IMG_20171130_223505.jpg

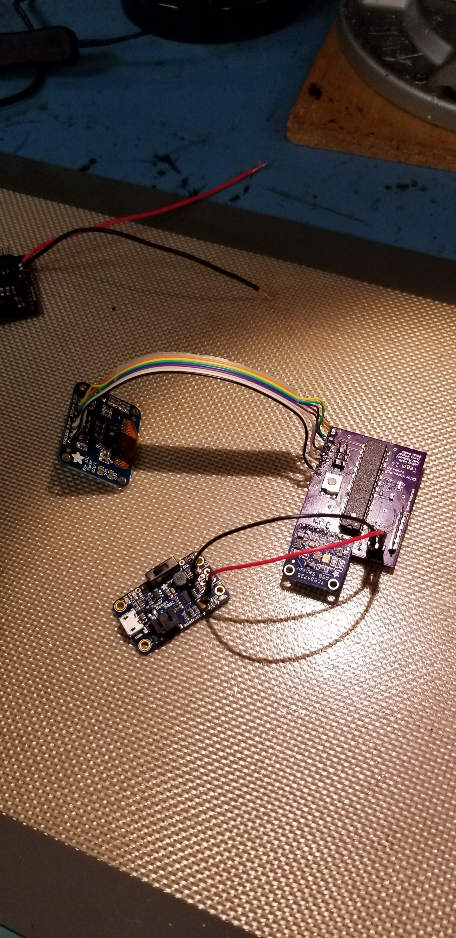
images/IMG_20171130_223505.jpg
