jeffudall/Team14/images/IMG_20171206_115303.jpg

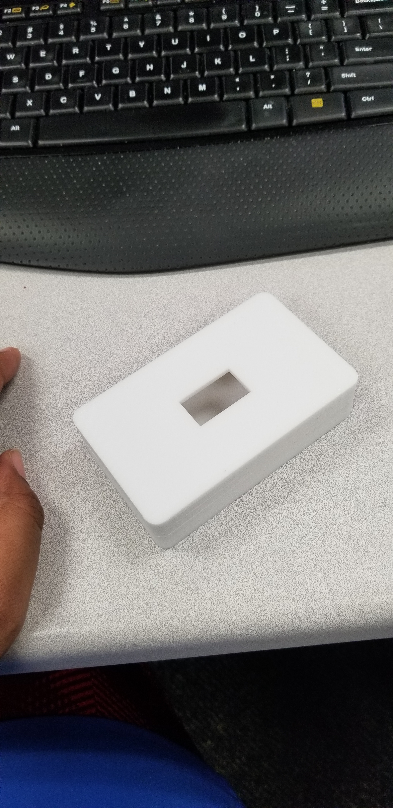
images/IMG_20171206_115303.jpg
