jeffudall/Team14/images/IMG_20171206_115335.jpg

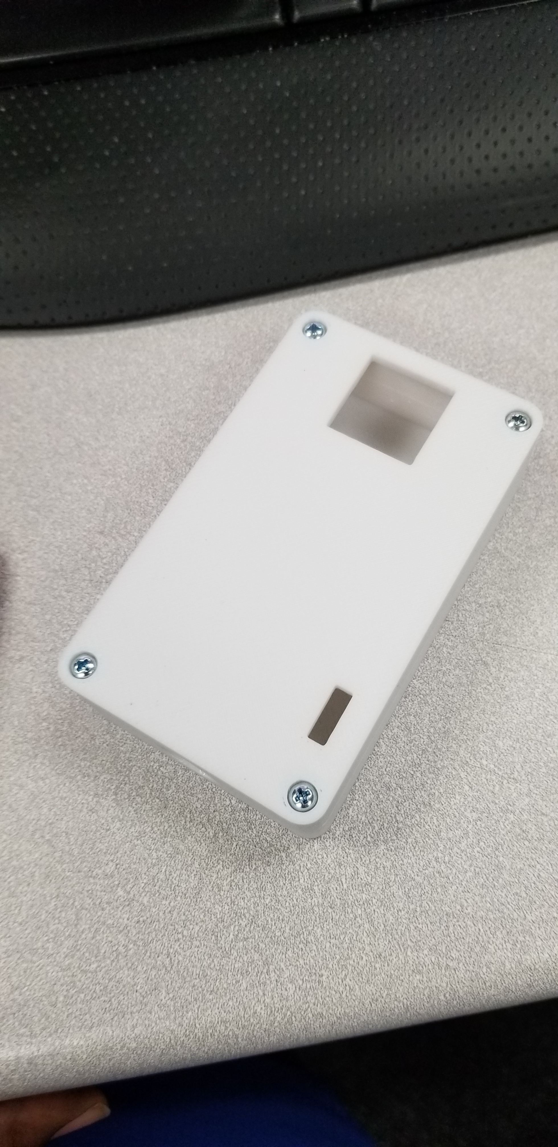
images/IMG_20171206_115335.jpg
