jeffudall/Team14/images/LCD_working.png

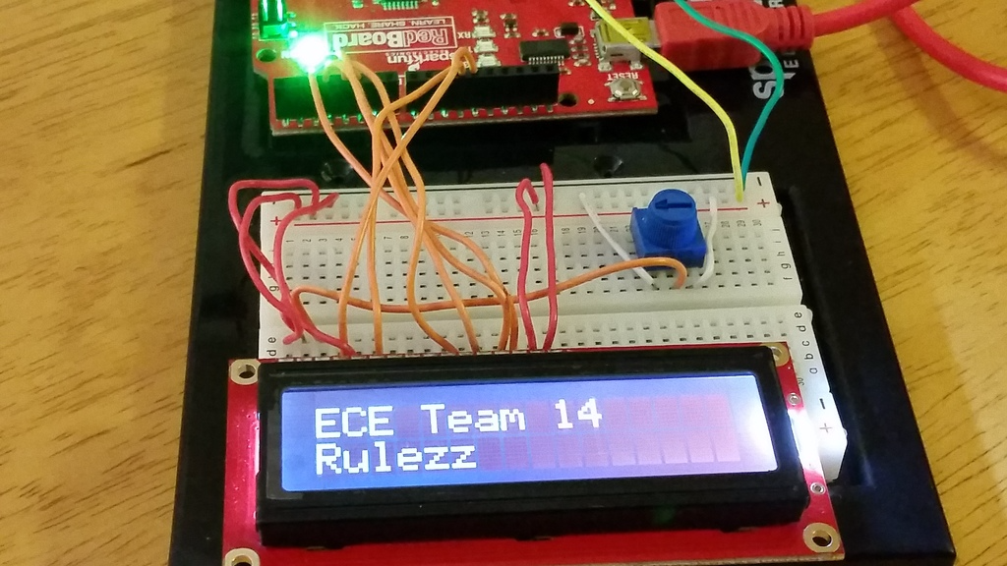
images/LCD_working.png
