jeffudall/Team14/images/modular_firmware.PNG

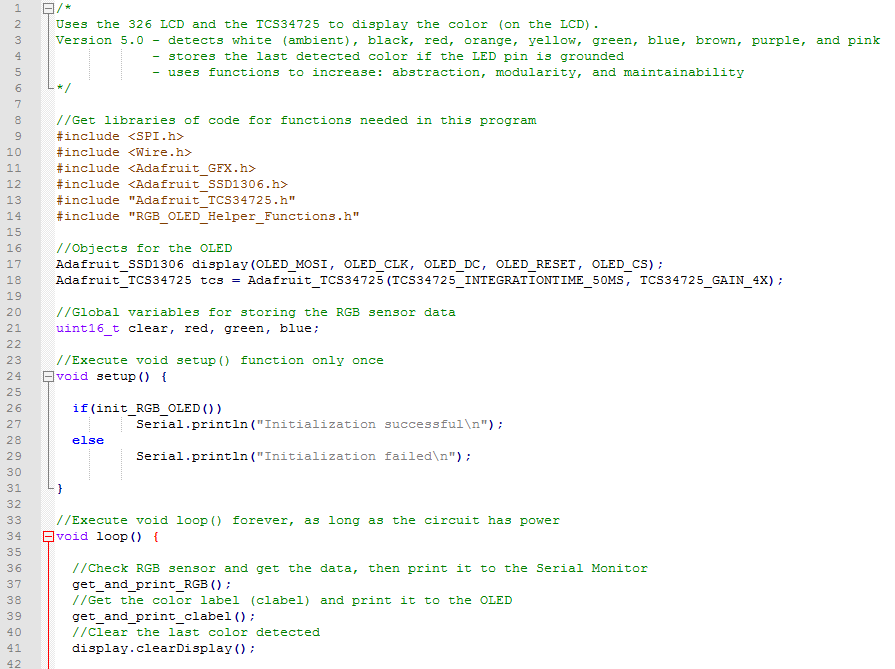
images/modular_firmware.PNG
