jeffudall/Team14/images/OLED_screen.JPG

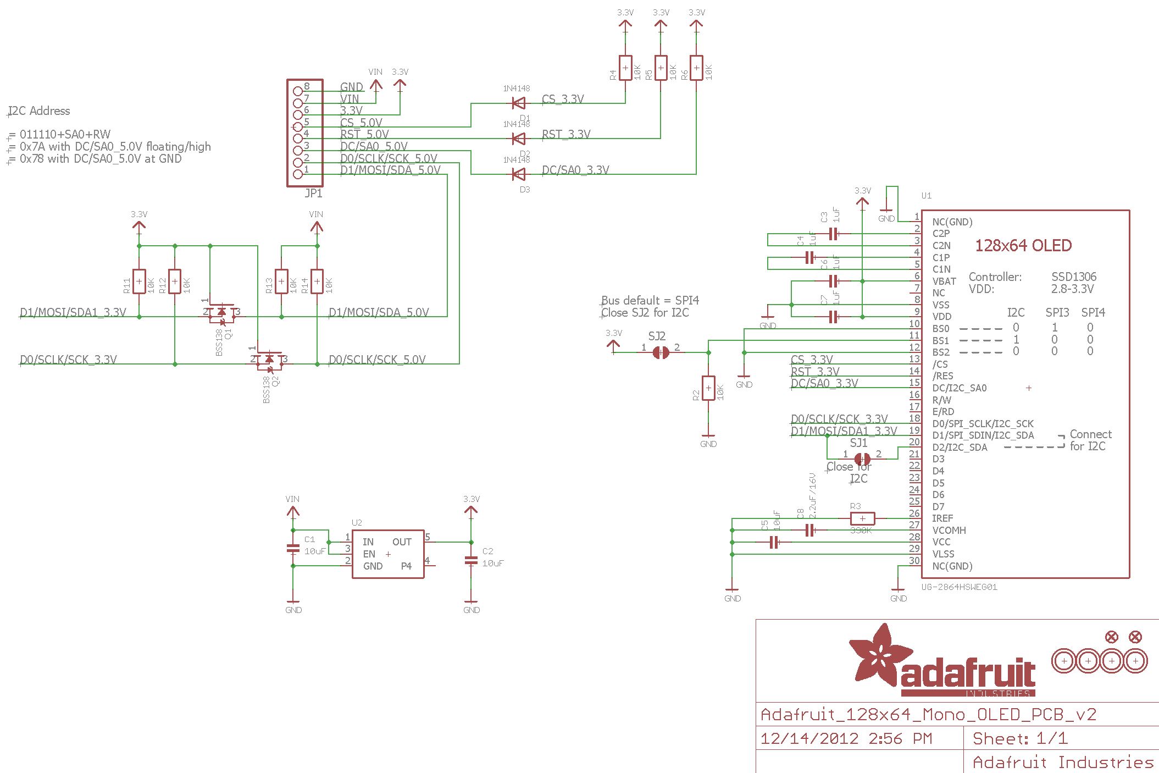
images/OLED_screen.JPG
