jeffudall/Team14/images/Pasted image at 2017_10_15 02_47 PM.png

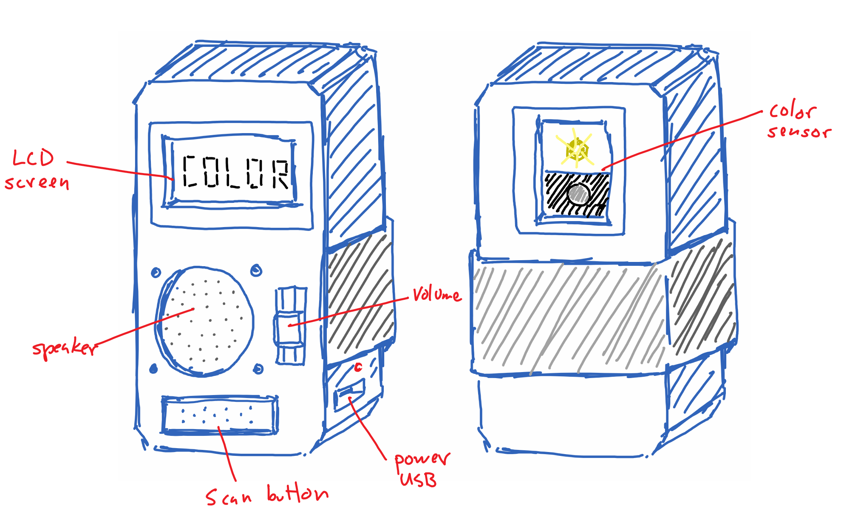
images/Pasted image at 2017_10_15 02_47 PM.png
