jeffudall/Team14/images/Pasted image at 2017_10_15 04_36 PM.png

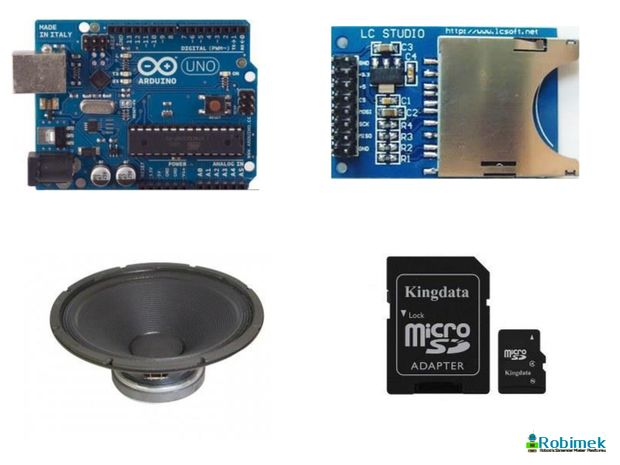
images/Pasted image at 2017_10_15 04_36 PM.png
