jeffudall/Team14/images/Pasted image at 2017_11_22 03_06 PM.png

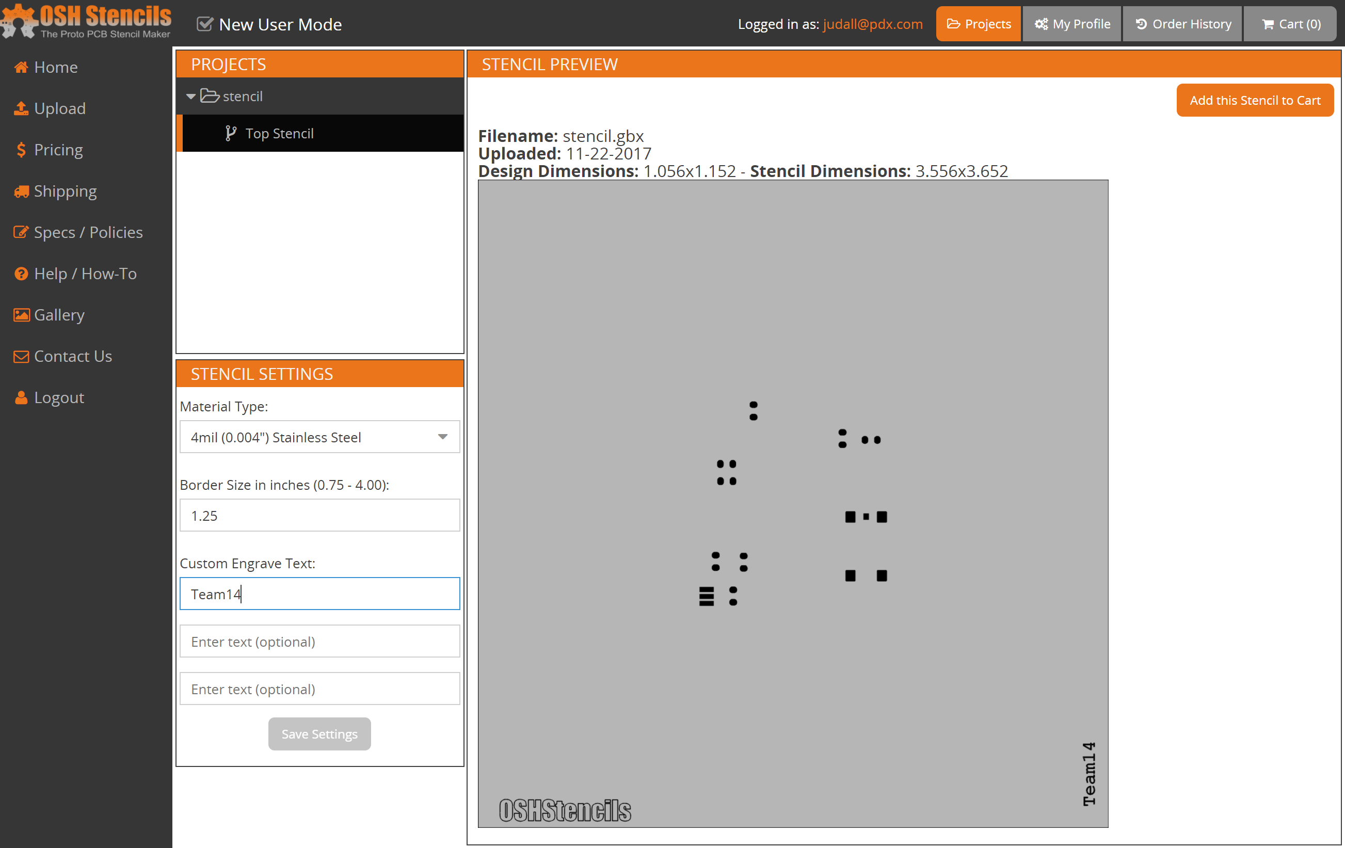
images/Pasted image at 2017_11_22 03_06 PM.png
