jeffudall/Team14/images/power_adaptor.JPG

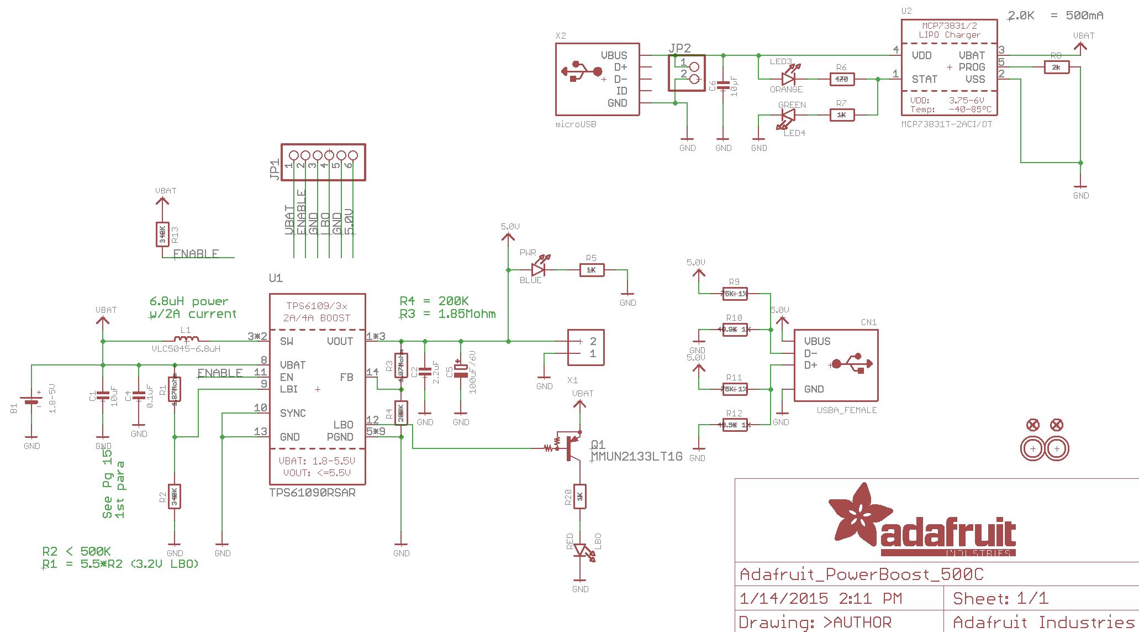
images/power_adaptor.JPG
