jeffudall/Team14/images/Prelim_PCB_01.JPG

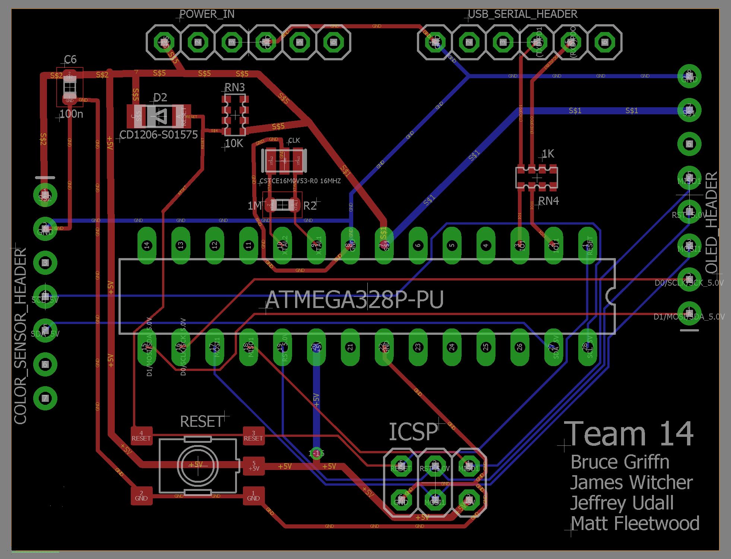
images/Prelim_PCB_01.JPG
