jeffudall/Team14/images/Prelim_PCB_04.5.JPG

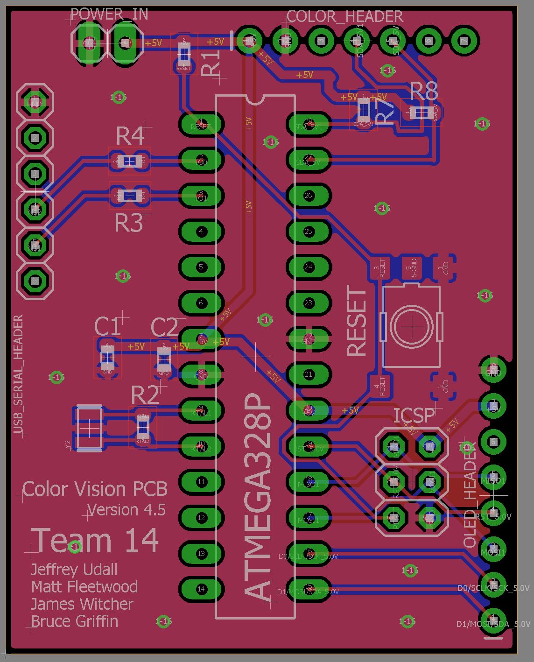
images/Prelim_PCB_04.5.JPG
