jeffudall/Team14/images/Prelim_PCB_04.JPG

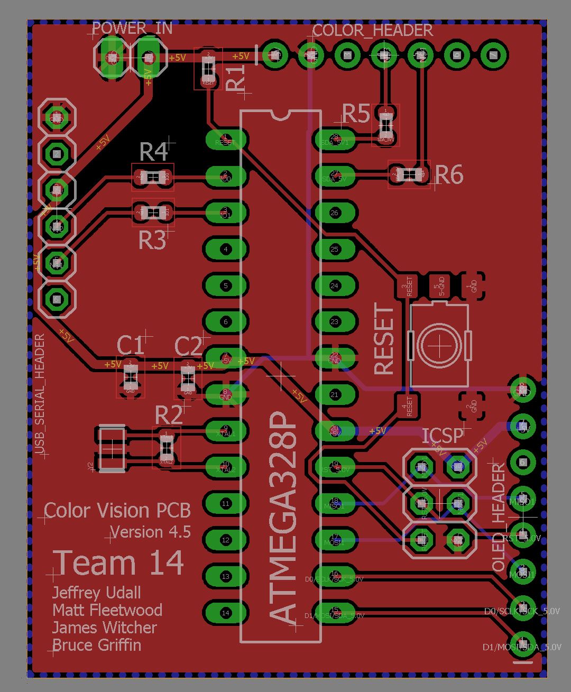
images/Prelim_PCB_04.JPG
