jeffudall/Team14/images/Prelim_Sch.JPG

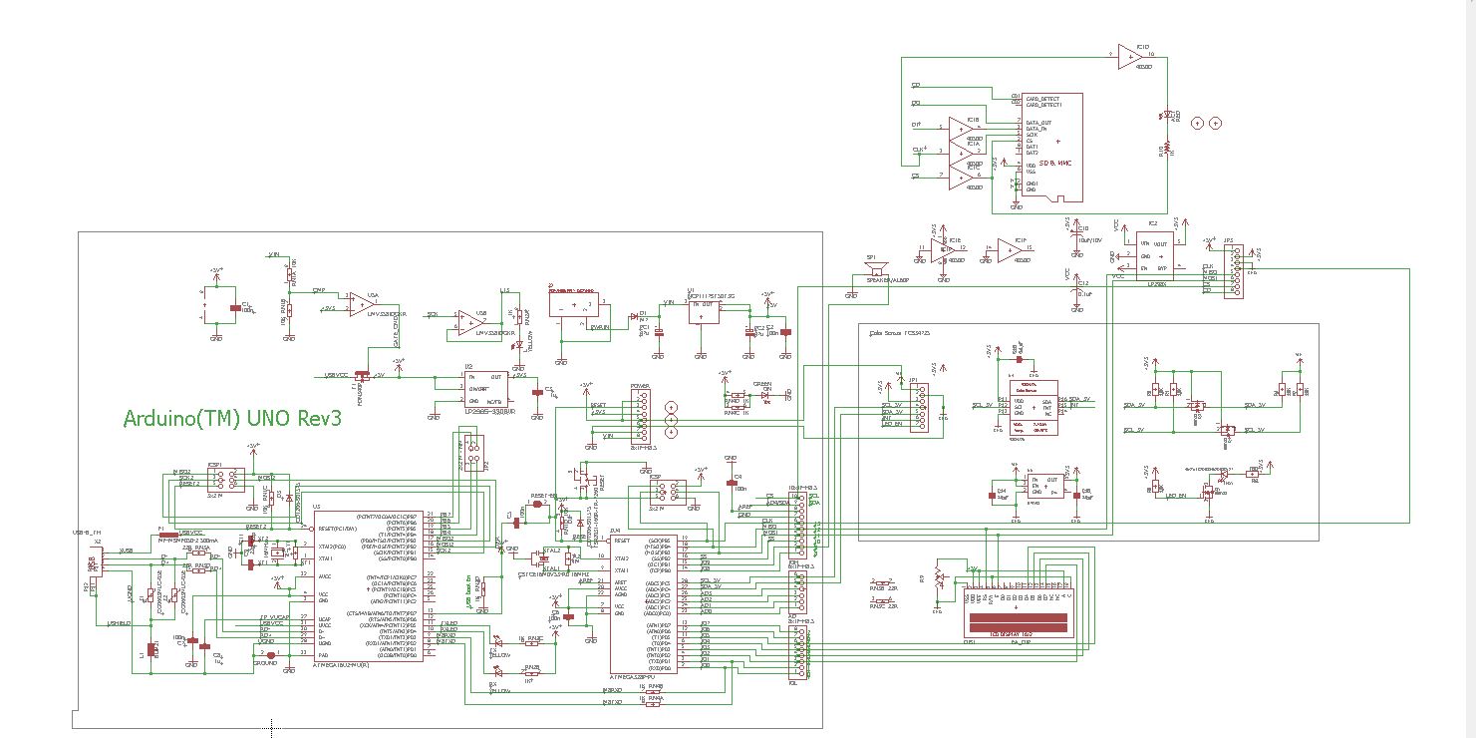
images/Prelim_Sch.JPG
