jeffudall/Team14/images/Prelim_Sch_02.JPG

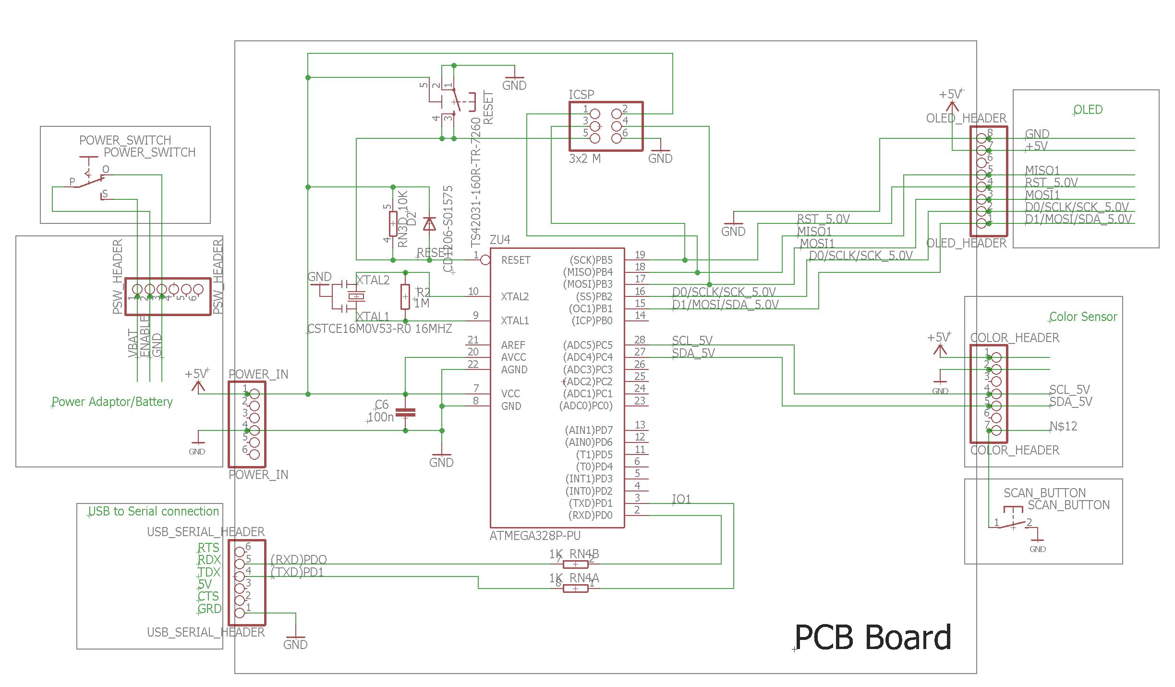
images/Prelim_Sch_02.JPG
