jeffudall/Team14/images/Prelim_Sch_04.5.JPG

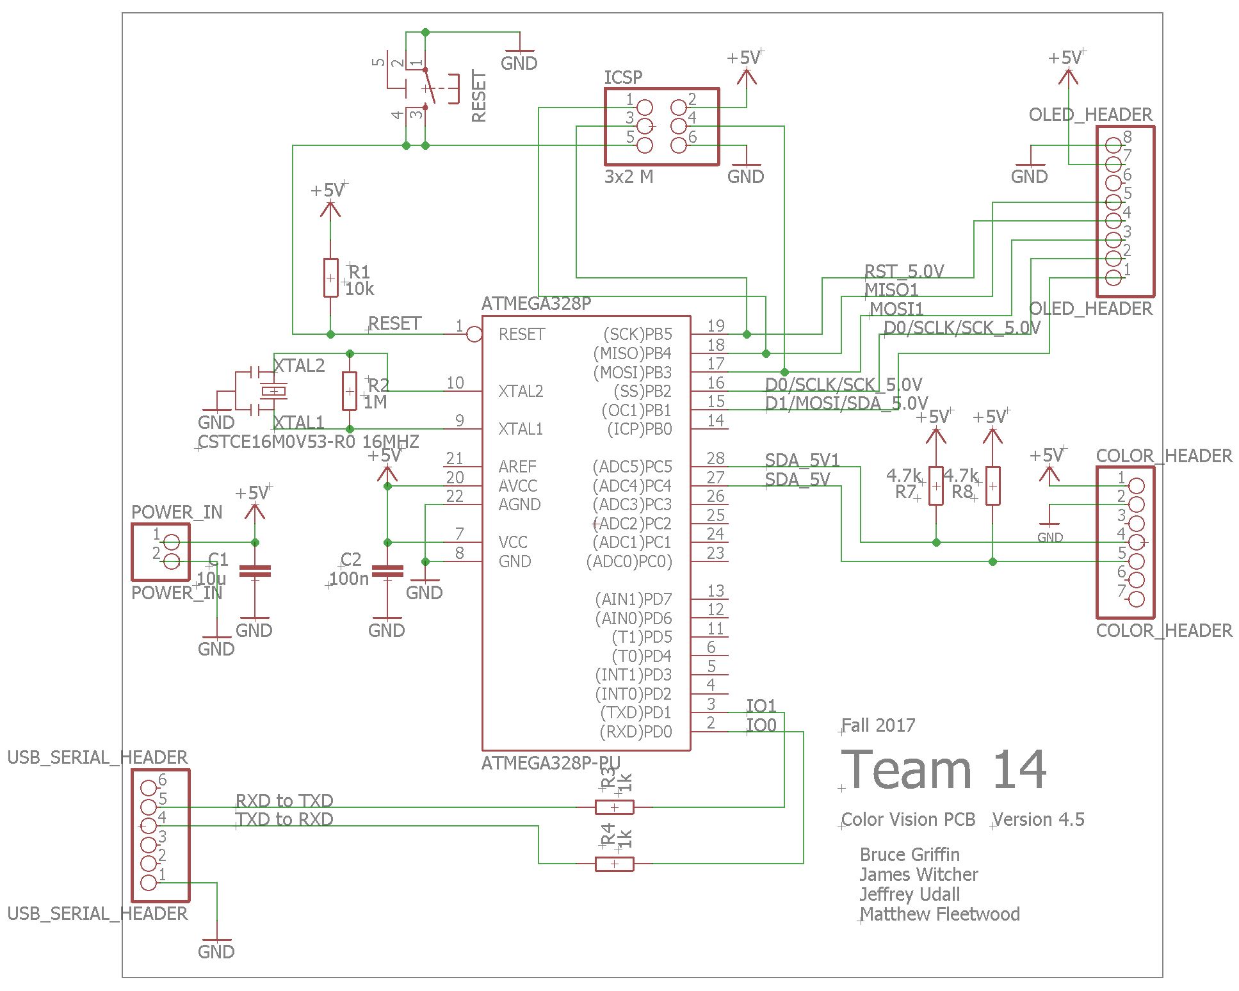
images/Prelim_Sch_04.5.JPG
