jeffudall/Team14/images/prelim_schedule.PNG

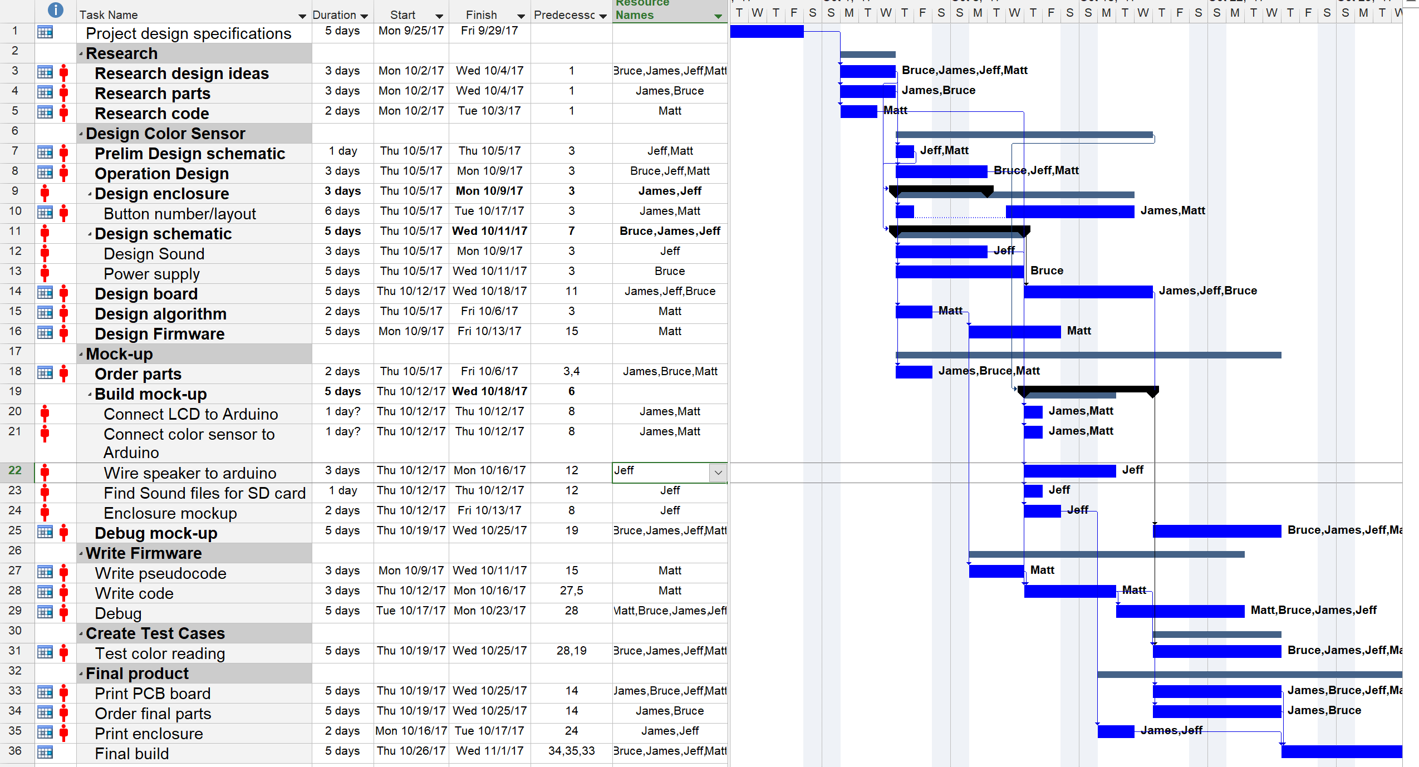
images/prelim_schedule.PNG
