jeffudall/Team14/images/Programing chip/proof.PNG

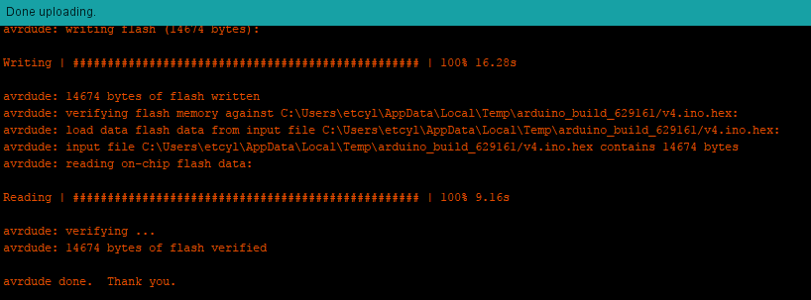
images/Programing chip/proof.PNG
