jeffudall/Team14/images/project_sketch_2.PNG

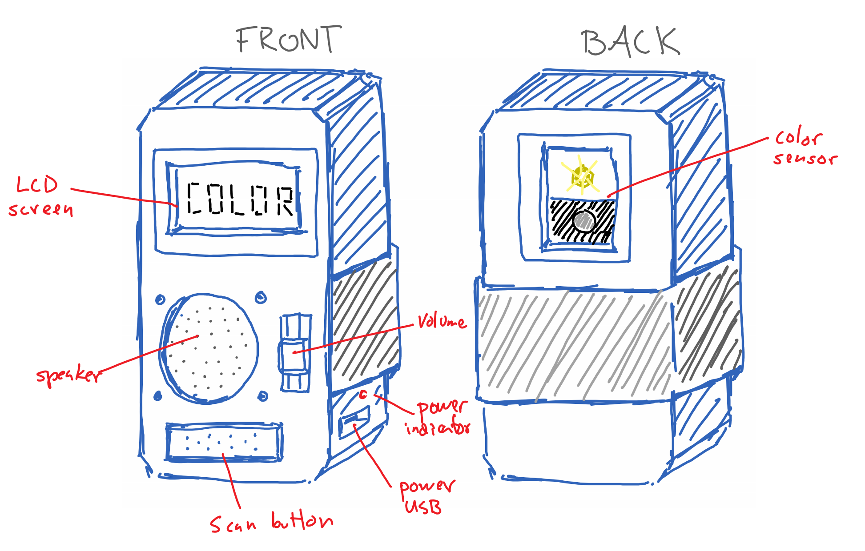
images/project_sketch_2.PNG
