jeffudall/Team14/images/red.jpg

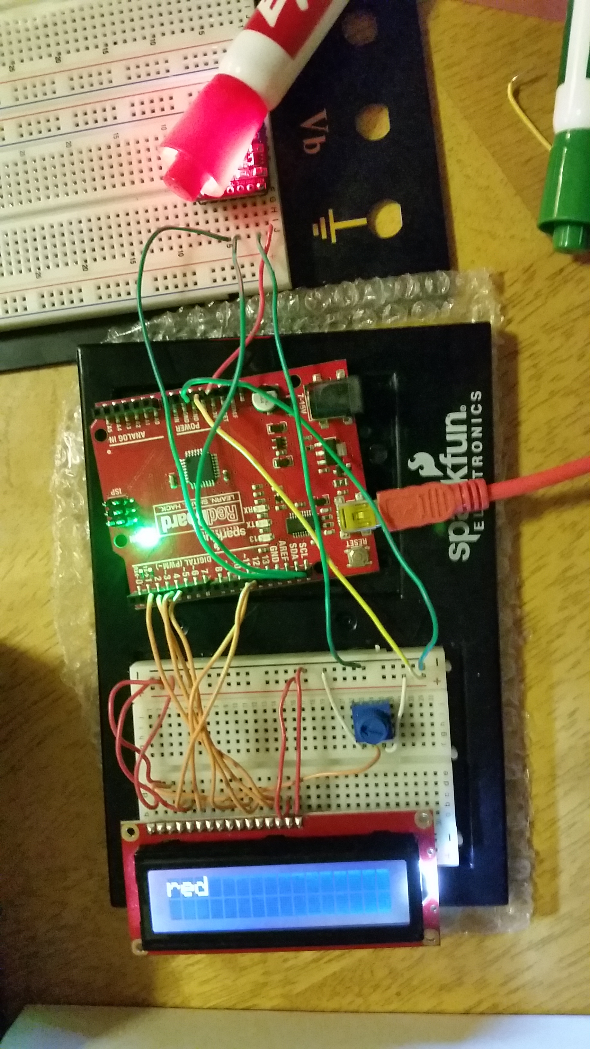
images/red.jpg
