jeffudall/Team14/images/Screen Shot 2017-12-05 at 2.20.10 PM.png

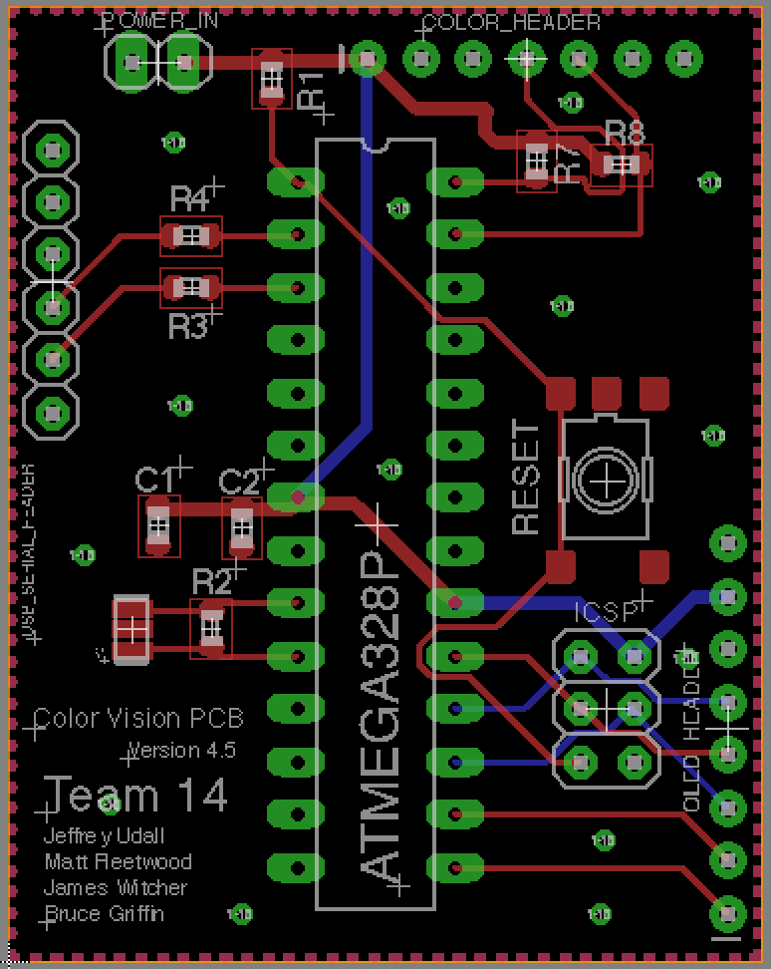
images/Screen Shot 2017-12-05 at 2.20.10 PM.png
