jeffudall/Team14/images/Screenshot_2017-11-22-16-35-46.png

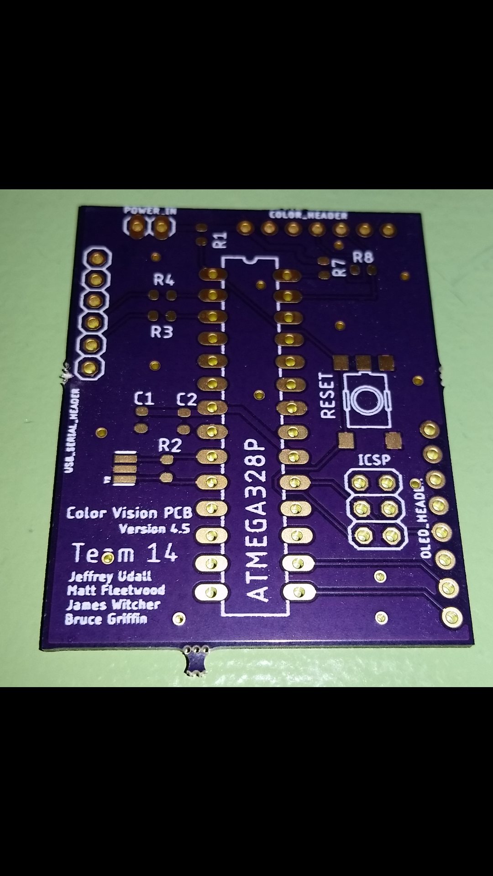
images/Screenshot_2017-11-22-16-35-46.png
