jeffudall/Team14/images/team_resources_01.PNG

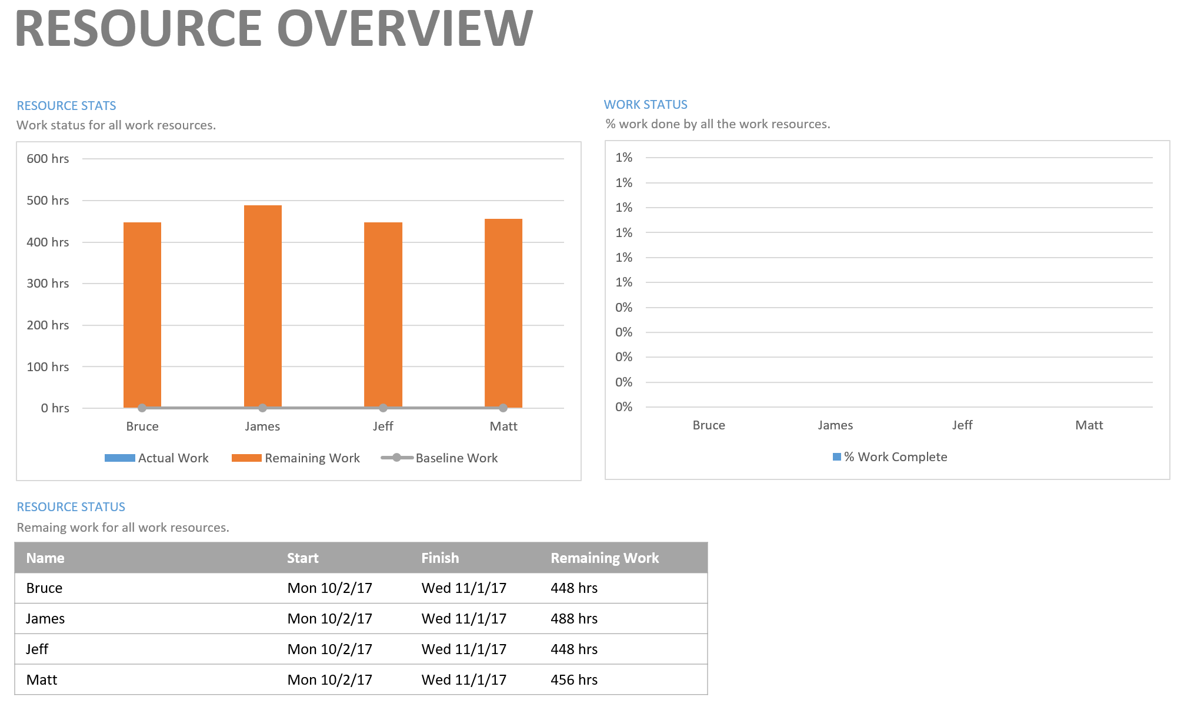
images/team_resources_01.PNG
