jeffudall/Team14/Misc/Presentation_Files/Presentation_Files-2.jpg

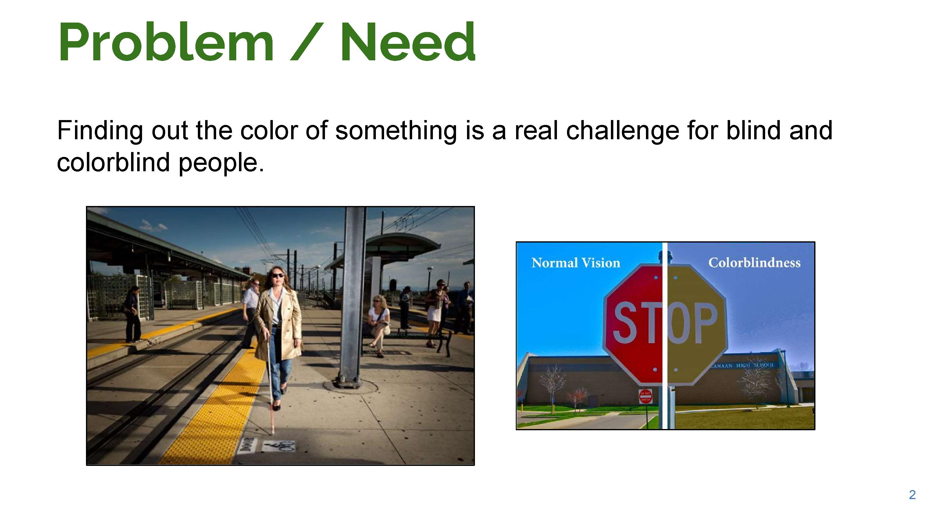
Misc/Presentation_Files/Presentation_Files-2.jpg
