jeffudall/Team14/Misc/Presentation_Files/Presentation_Files-3.jpg

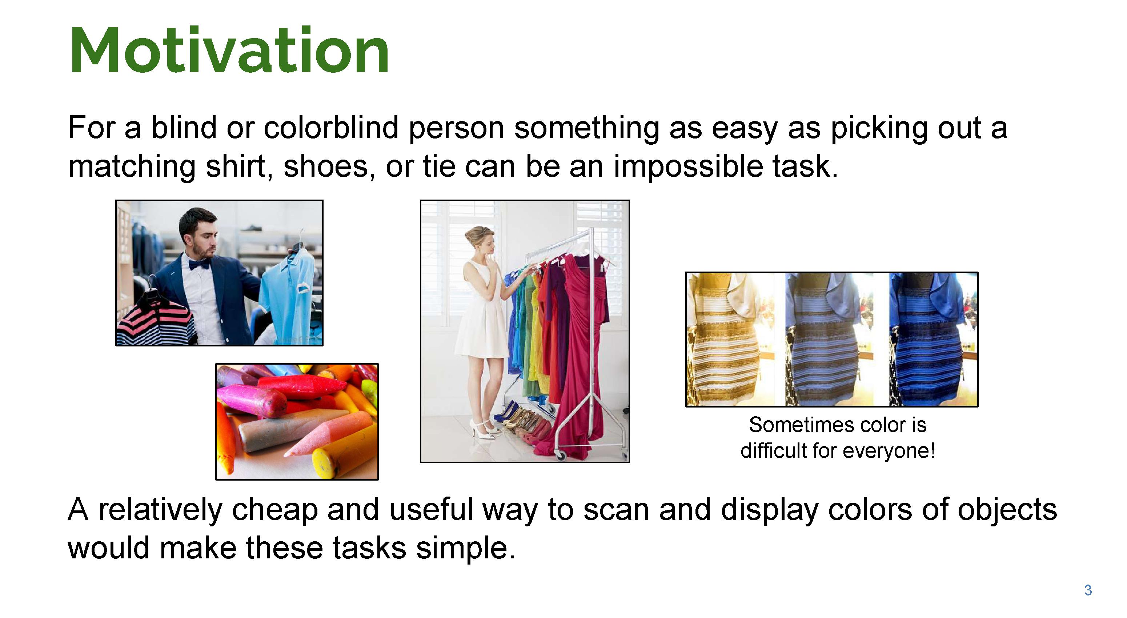
Misc/Presentation_Files/Presentation_Files-3.jpg
