jeffudall/Team14/Misc/Presentation_Files/Presentation_Files-4.jpg

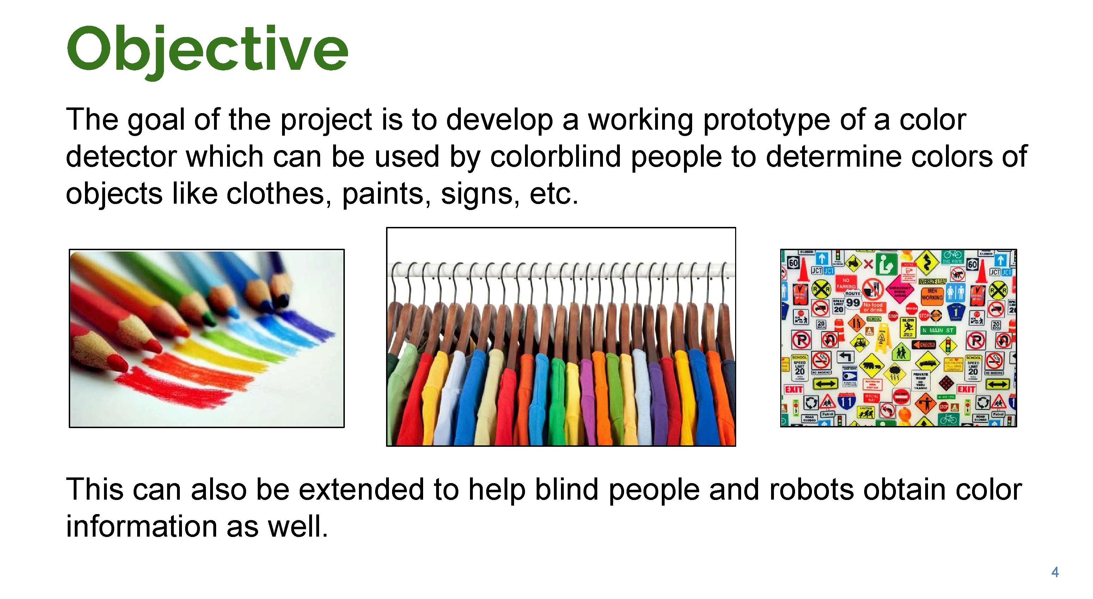
Misc/Presentation_Files/Presentation_Files-4.jpg
