jeffudall/Team14/Misc/Presentation_Files/Presentation_Files-5.jpg

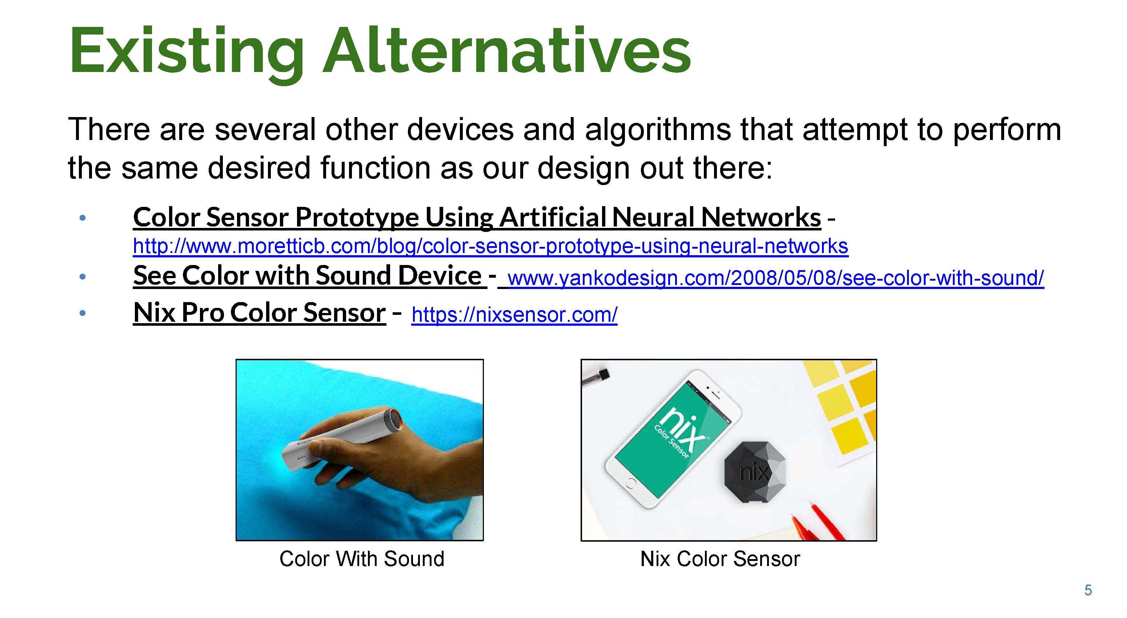
Misc/Presentation_Files/Presentation_Files-5.jpg
