jeffudall/Team14/Misc/Presentation_Files/Presentation_Files-6.jpg

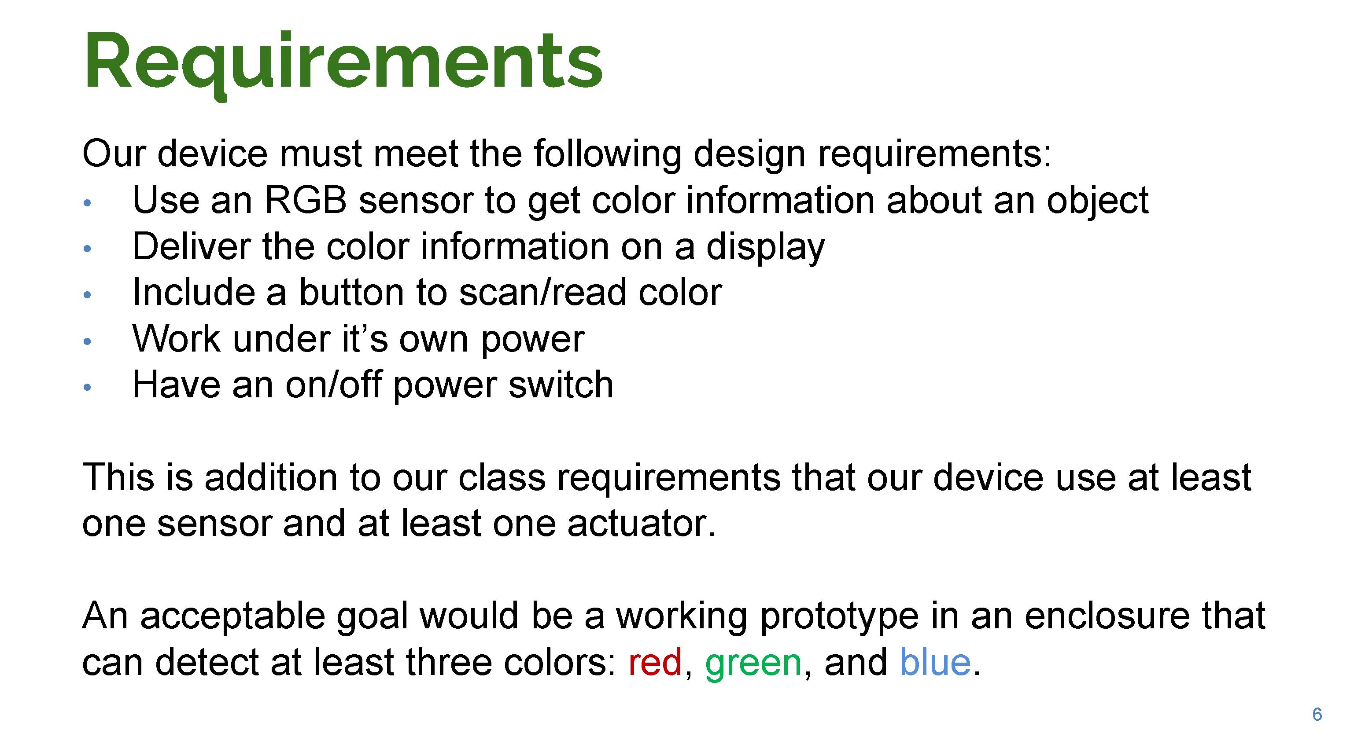
Misc/Presentation_Files/Presentation_Files-6.jpg
