jeffudall/Team14/Misc/Presentation_Files/Presentation_Files-7.jpg

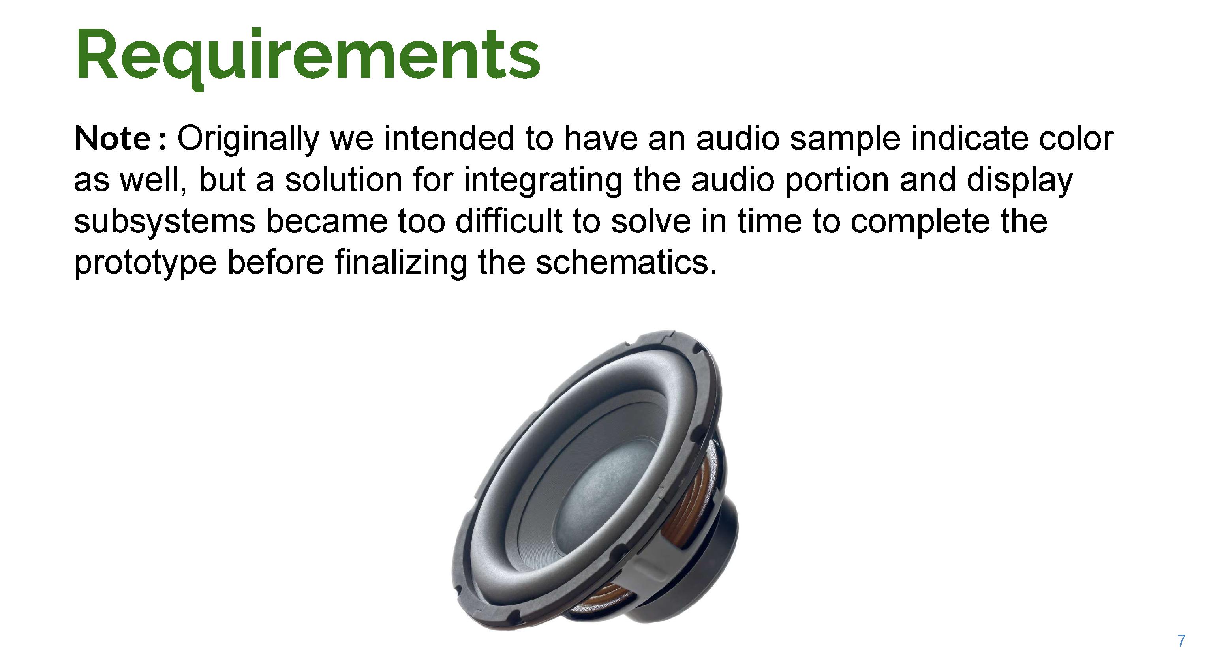
Misc/Presentation_Files/Presentation_Files-7.jpg
