jeffudall/Team14/Misc/Presentation_Files/Presentation_Files-8.jpg

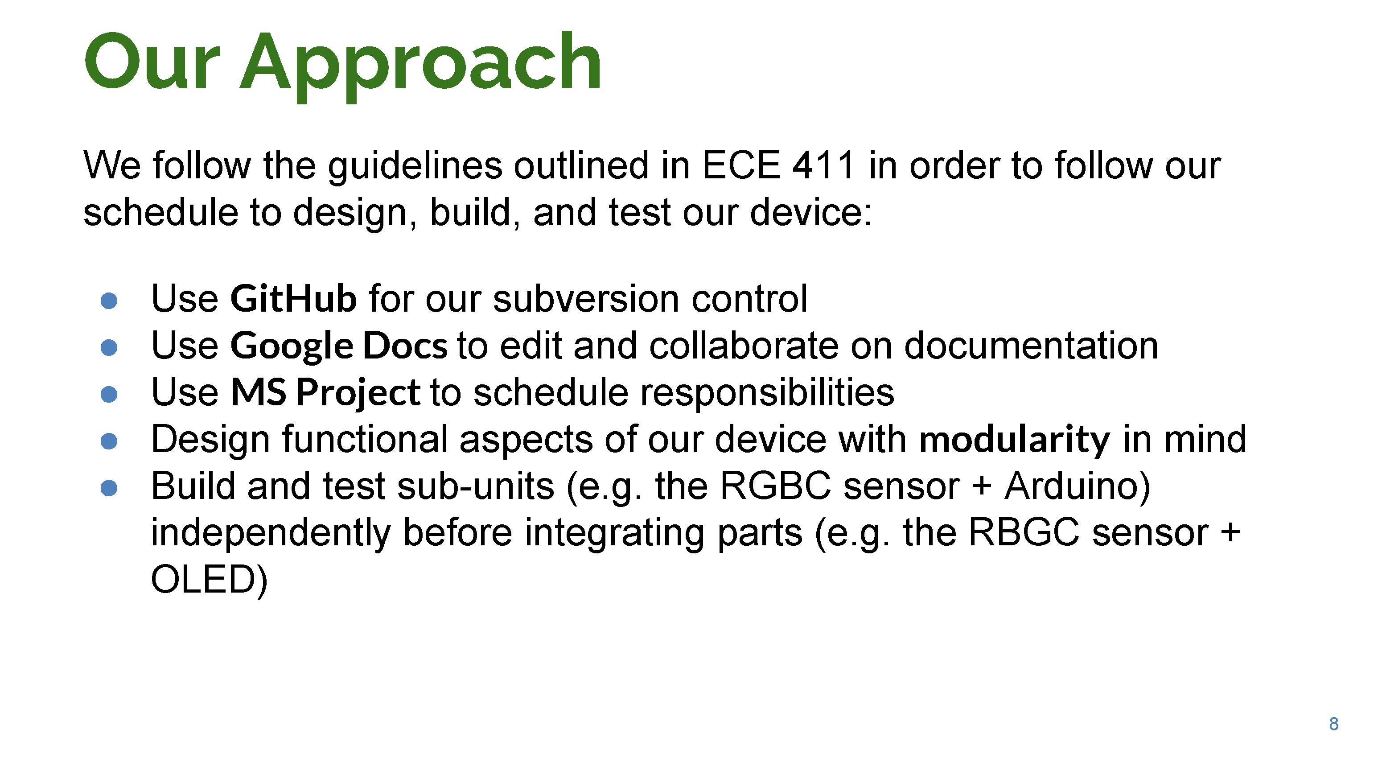
Misc/Presentation_Files/Presentation_Files-8.jpg
