jeffudall/Team14/Misc/Presentation_Files/Presentation_Files-9.jpg

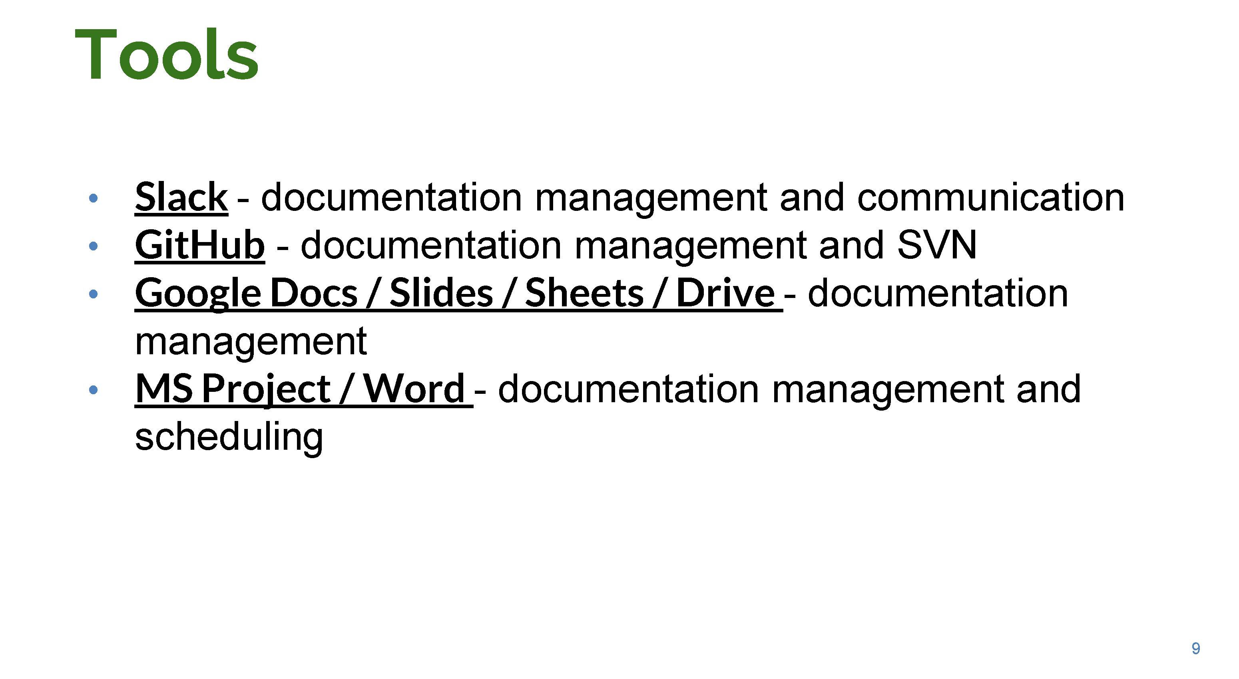
Misc/Presentation_Files/Presentation_Files-9.jpg
