jeffudall/Team14/Misc/Presentation_Files/Presentation_Files-10.jpg

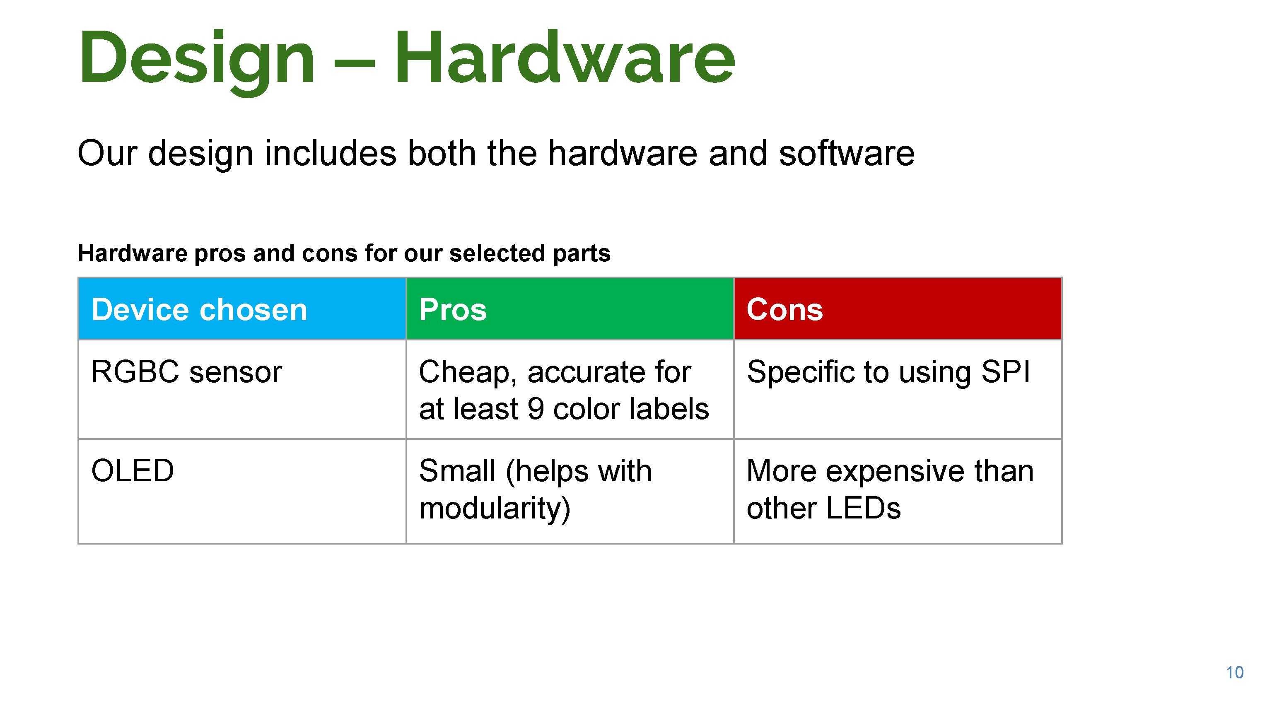
Misc/Presentation_Files/Presentation_Files-10.jpg
