jeffudall/Team14/Misc/Presentation_Files/Presentation_Files-11.jpg

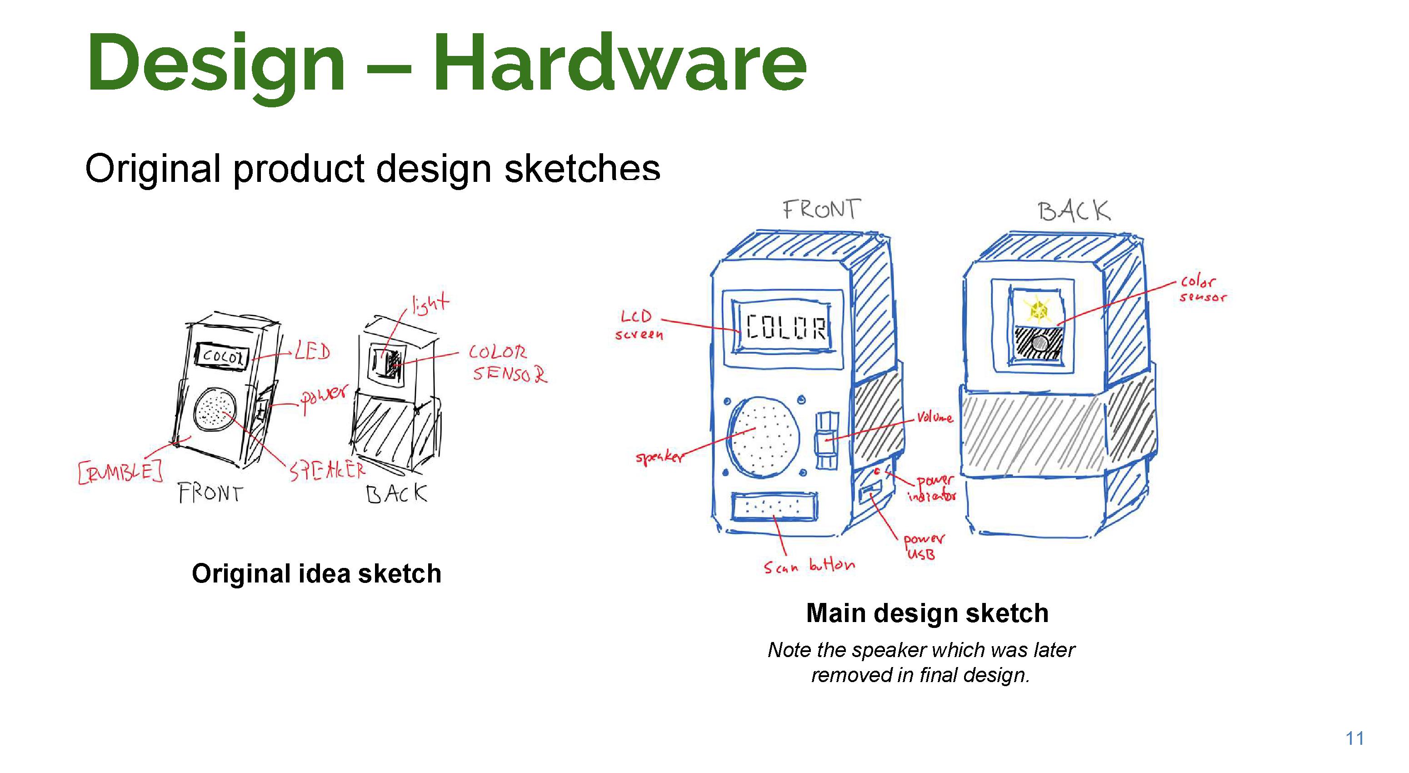
Misc/Presentation_Files/Presentation_Files-11.jpg
