jeffudall/Team14/Misc/Presentation_Files/Presentation_Files-12.jpg

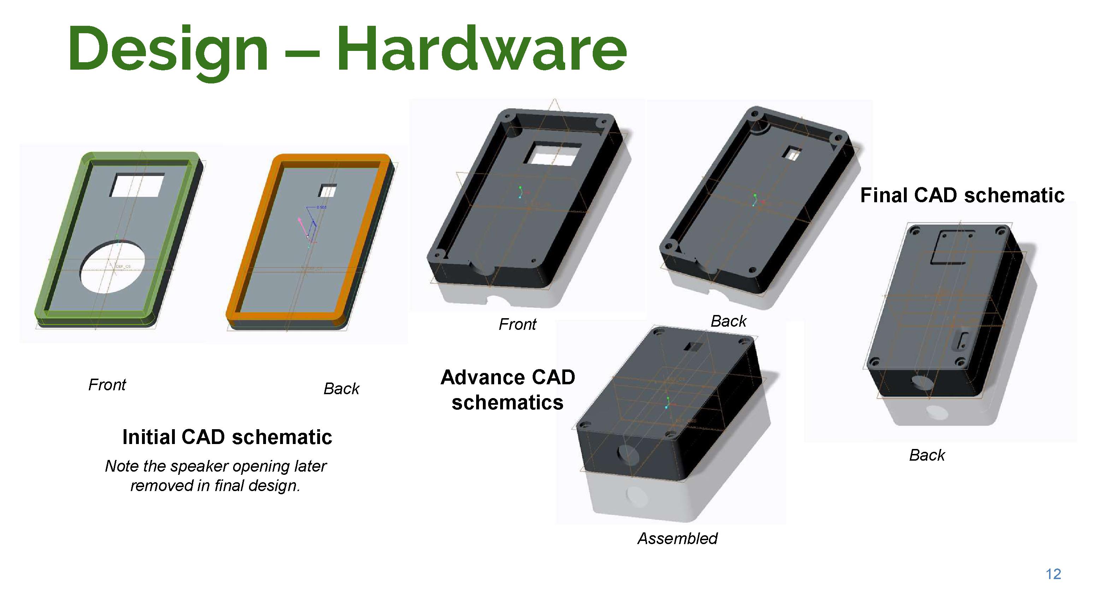
Misc/Presentation_Files/Presentation_Files-12.jpg
