jeffudall/Team14/Misc/Presentation_Files/Presentation_Files-13.jpg

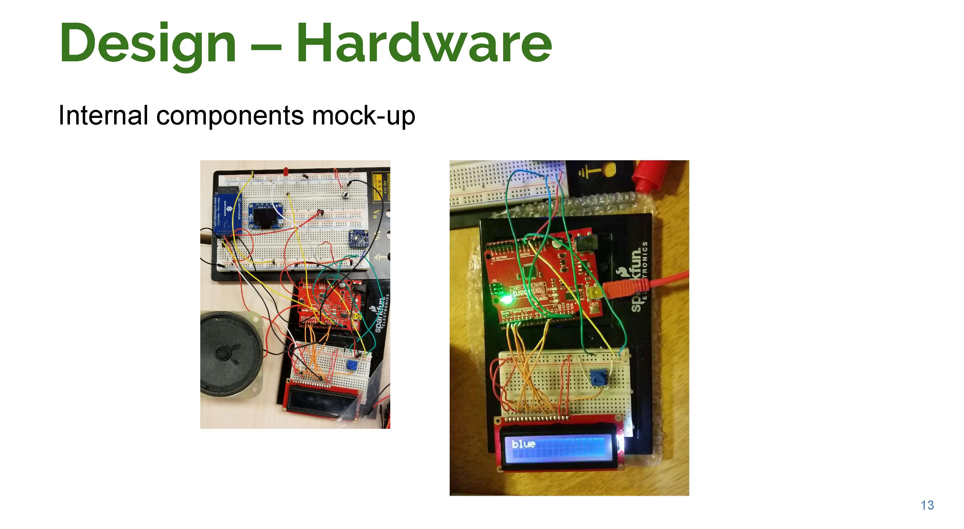
Misc/Presentation_Files/Presentation_Files-13.jpg
