jeffudall/Team14/Misc/Presentation_Files/Presentation_Files-14.jpg

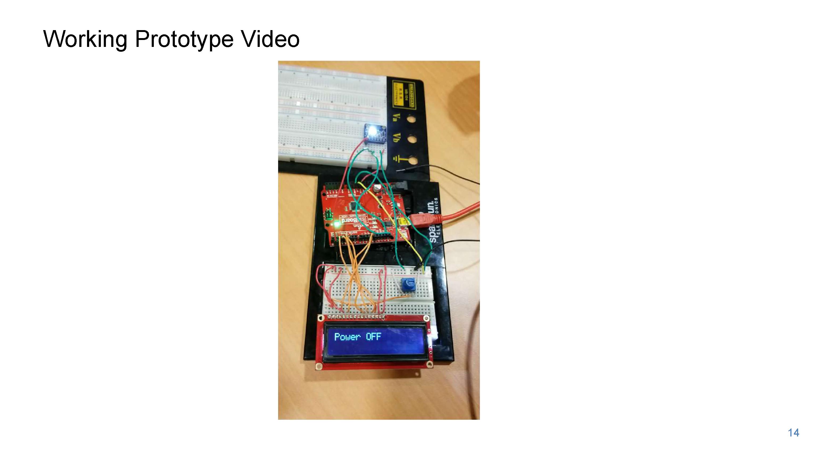
Misc/Presentation_Files/Presentation_Files-14.jpg
