jeffudall/Team14/Misc/Presentation_Files/Presentation_Files-15.jpg

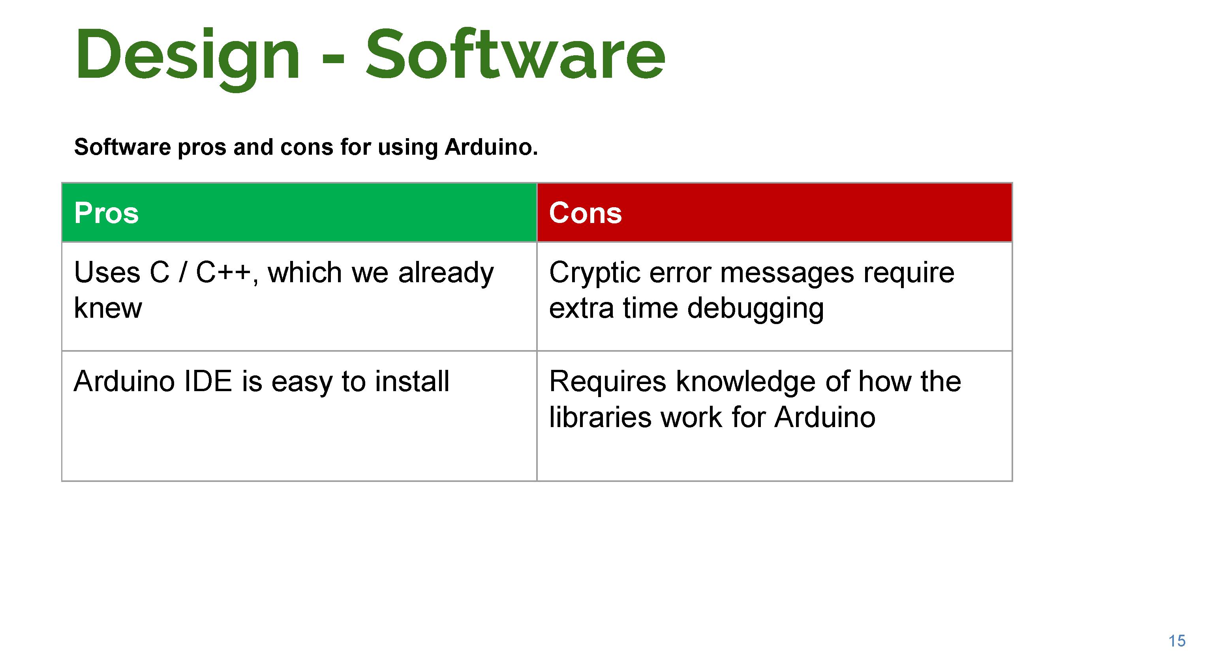
Misc/Presentation_Files/Presentation_Files-15.jpg
