jeffudall/Team14/Misc/Presentation_Files/Presentation_Files-16.jpg

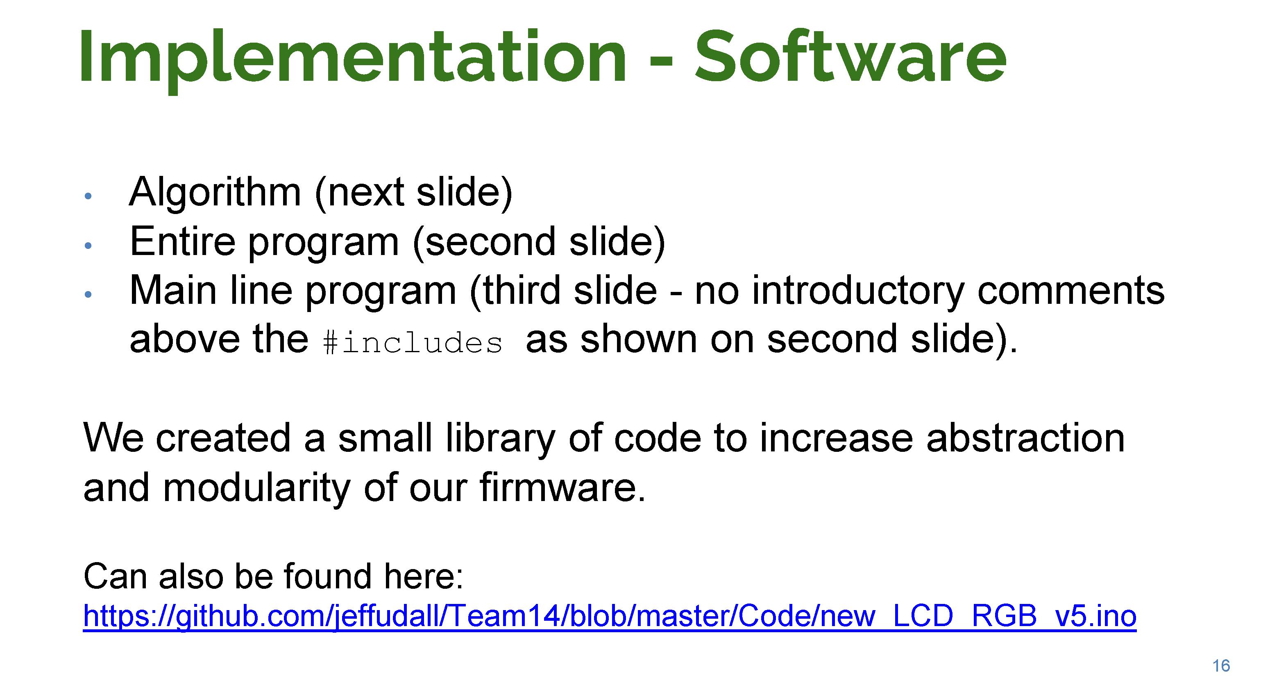
Misc/Presentation_Files/Presentation_Files-16.jpg
