jeffudall/Team14/Misc/Presentation_Files/Presentation_Files-17.jpg

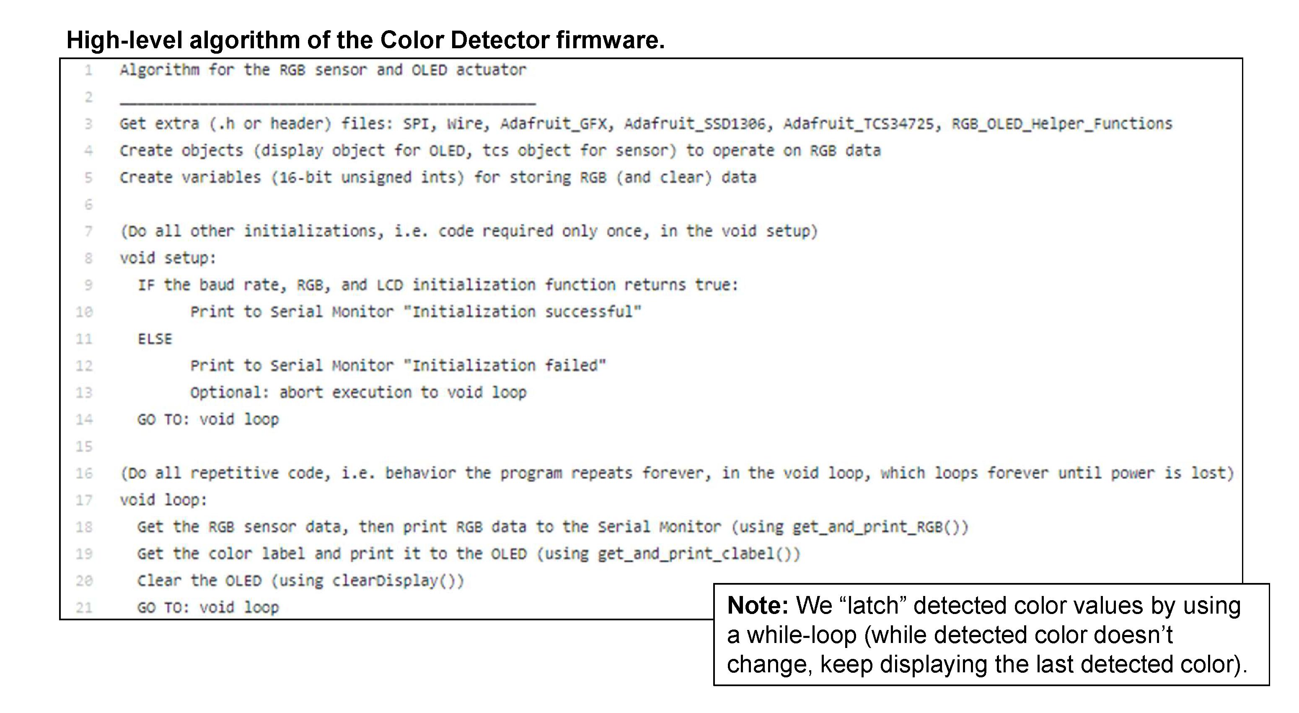
Misc/Presentation_Files/Presentation_Files-17.jpg
