jeffudall/Team14/Misc/Presentation_Files/Presentation_Files-18.jpg

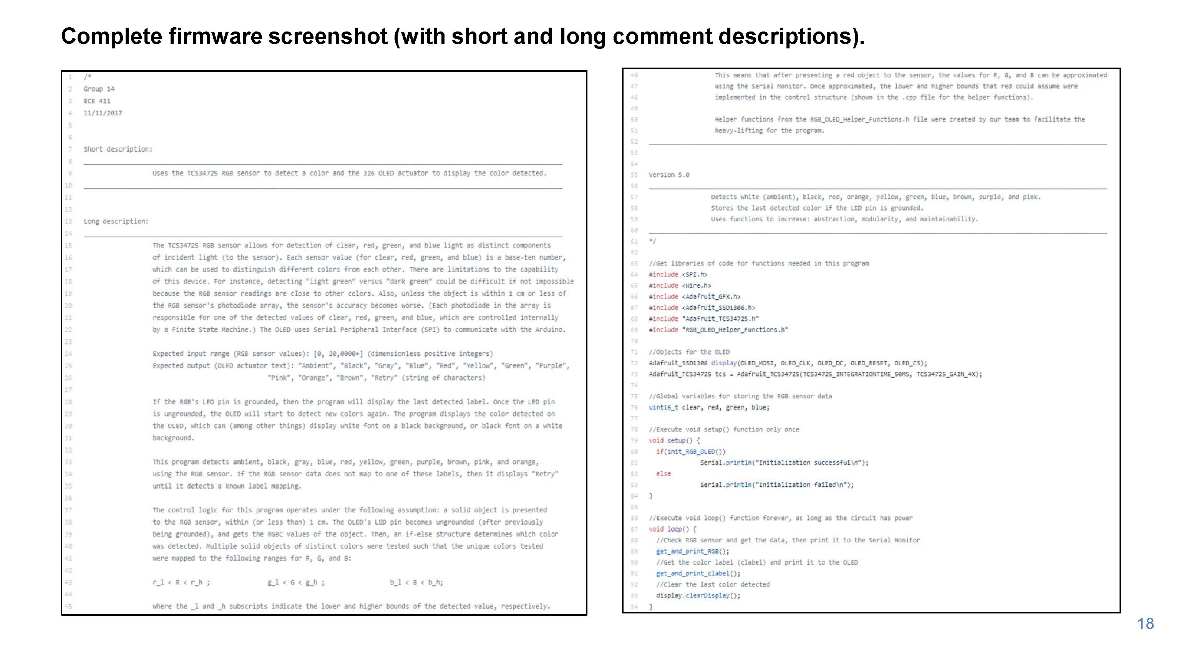
Misc/Presentation_Files/Presentation_Files-18.jpg
