jeffudall/Team14/Misc/Presentation_Files/Presentation_Files-19.jpg

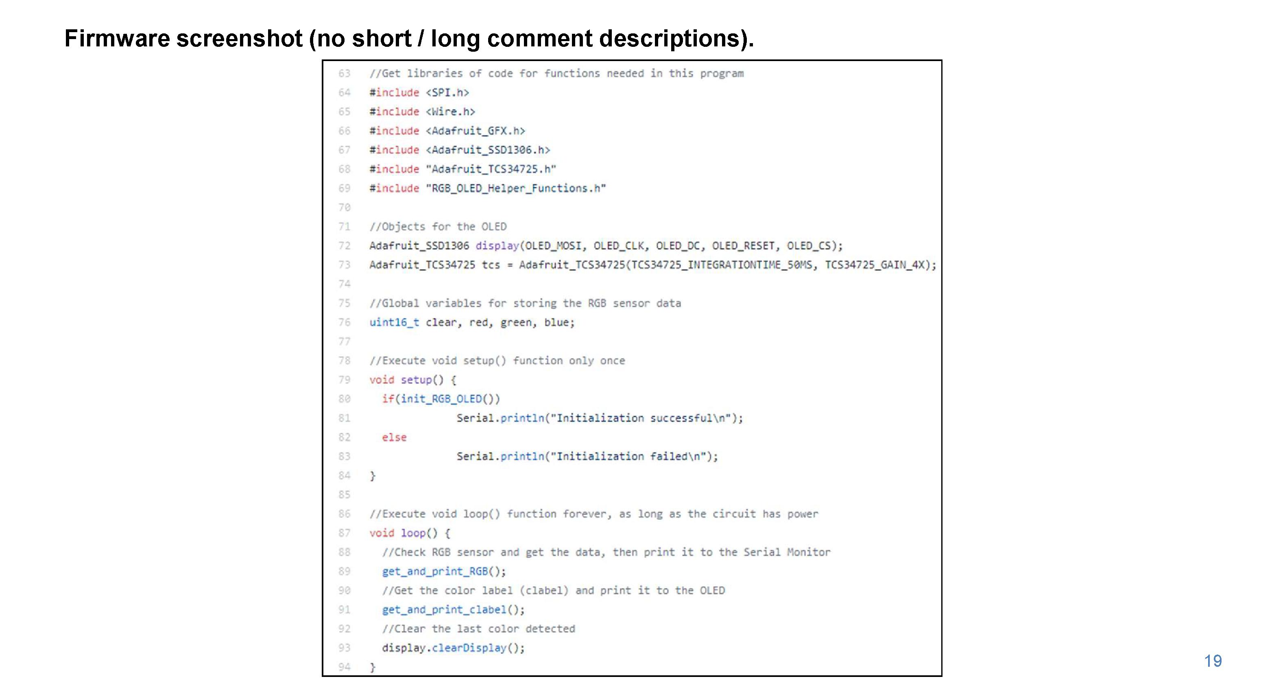
Misc/Presentation_Files/Presentation_Files-19.jpg
