jeffudall/Team14/Misc/Presentation_Files/Presentation_Files-20.jpg

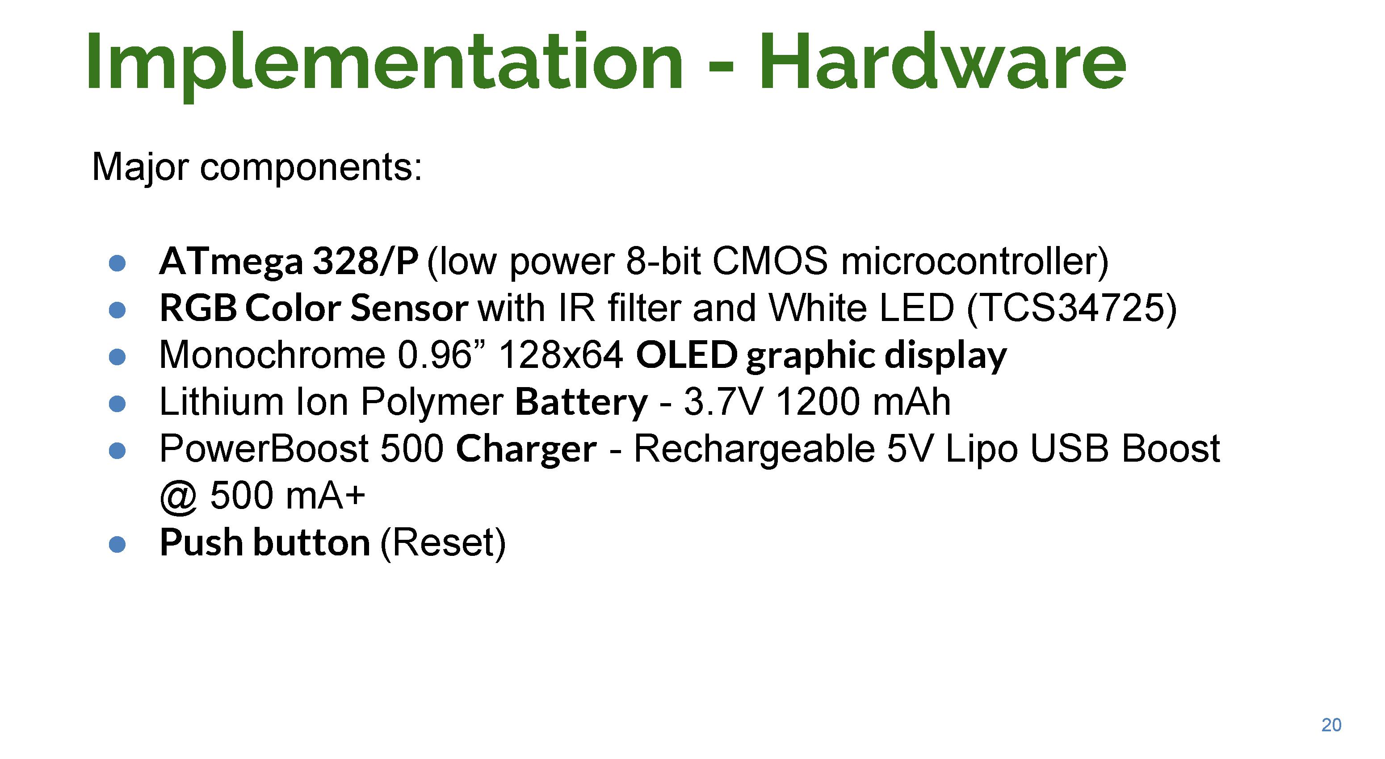
Misc/Presentation_Files/Presentation_Files-20.jpg
