jeffudall/Team14/Misc/Presentation_Files/Presentation_Files-21.jpg

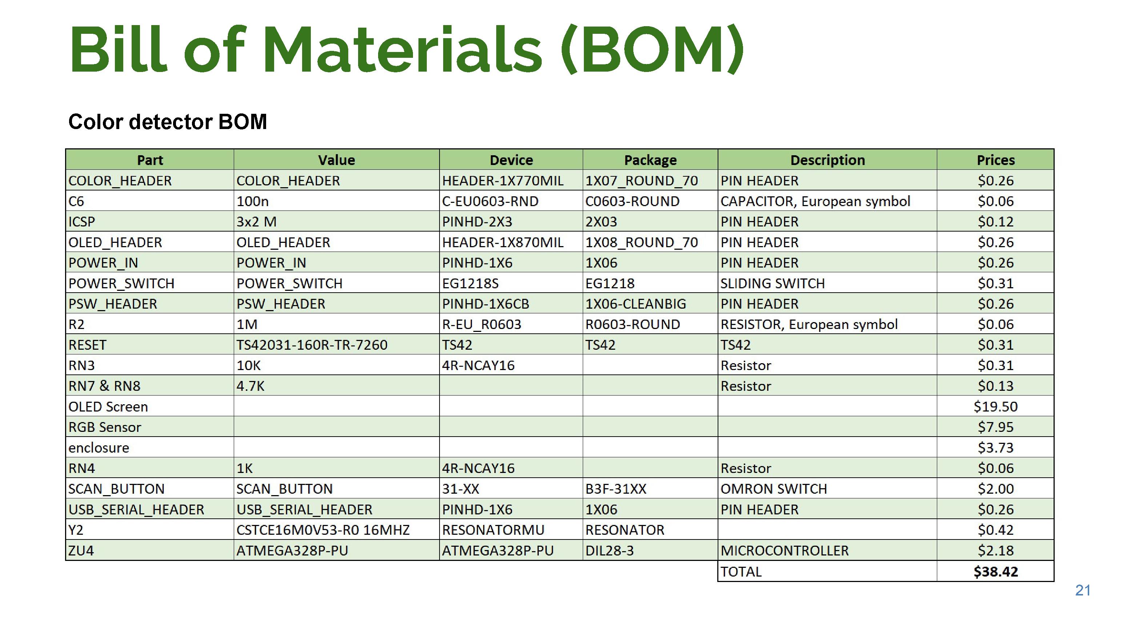
Misc/Presentation_Files/Presentation_Files-21.jpg
