jeffudall/Team14/Misc/Presentation_Files/Presentation_Files-22.jpg

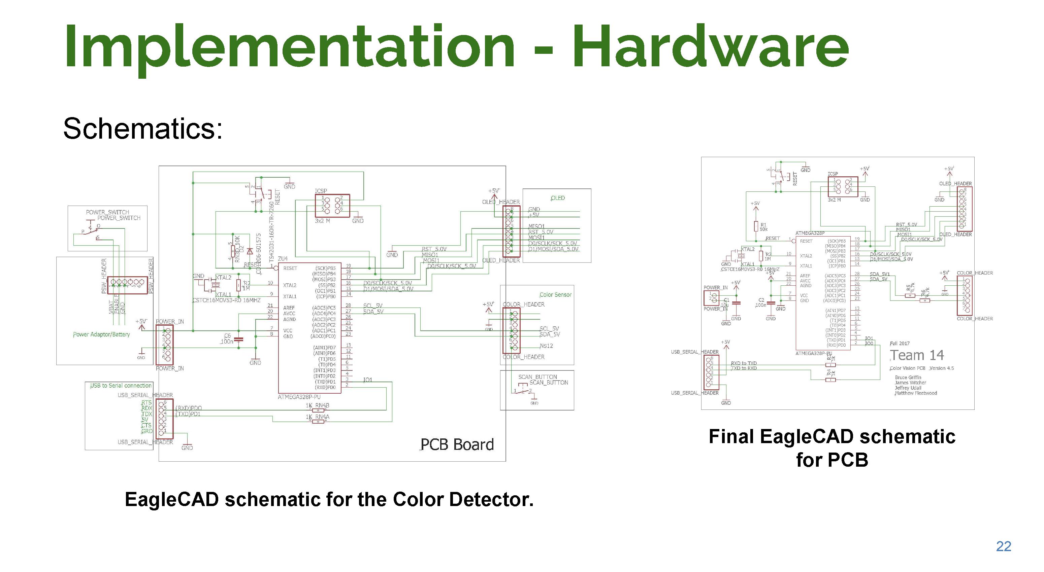
Misc/Presentation_Files/Presentation_Files-22.jpg
