jeffudall/Team14/Misc/Presentation_Files/Presentation_Files-23.jpg

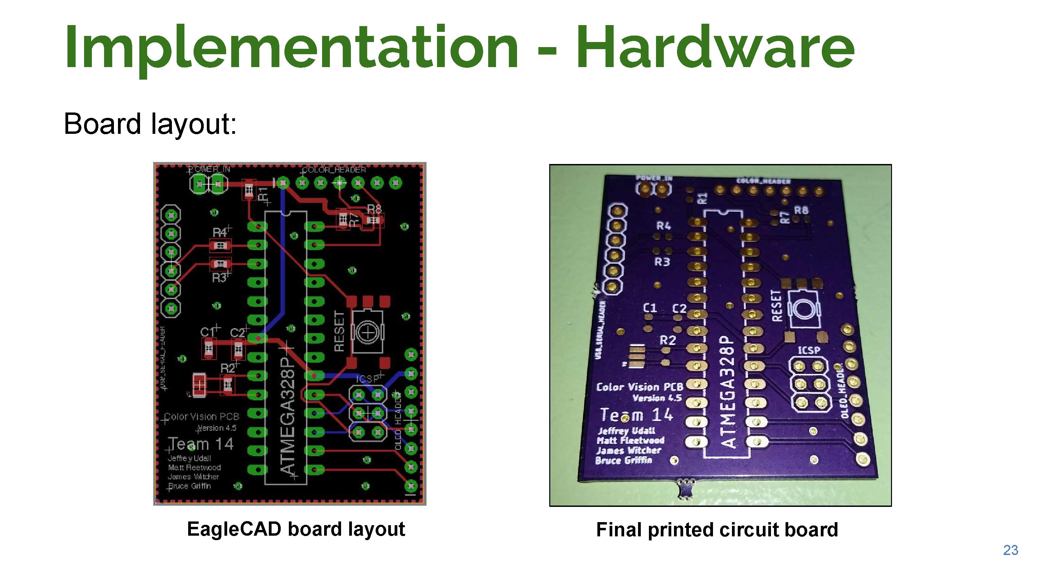
Misc/Presentation_Files/Presentation_Files-23.jpg
