jeffudall/Team14/Misc/Presentation_Files/Presentation_Files-24.jpg

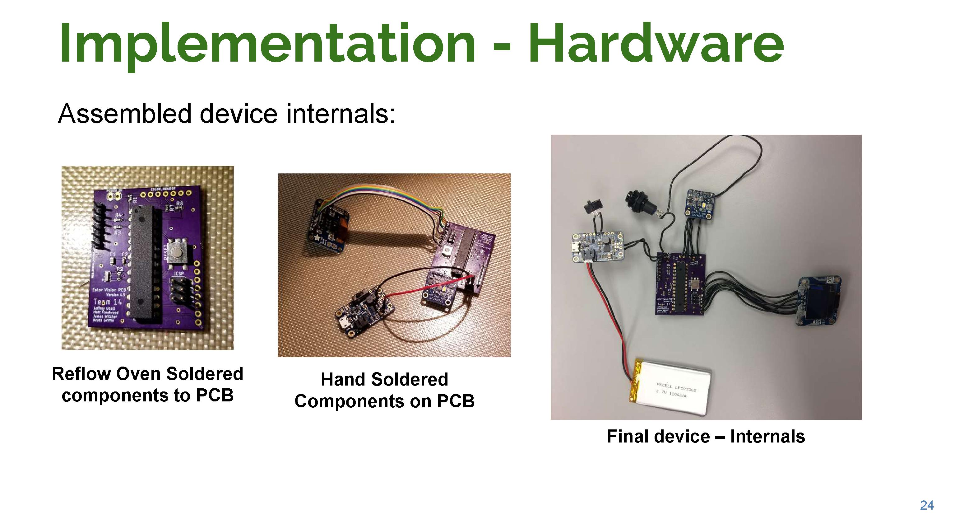
Misc/Presentation_Files/Presentation_Files-24.jpg
