jeffudall/Team14/Misc/Presentation_Files/Presentation_Files-25.jpg

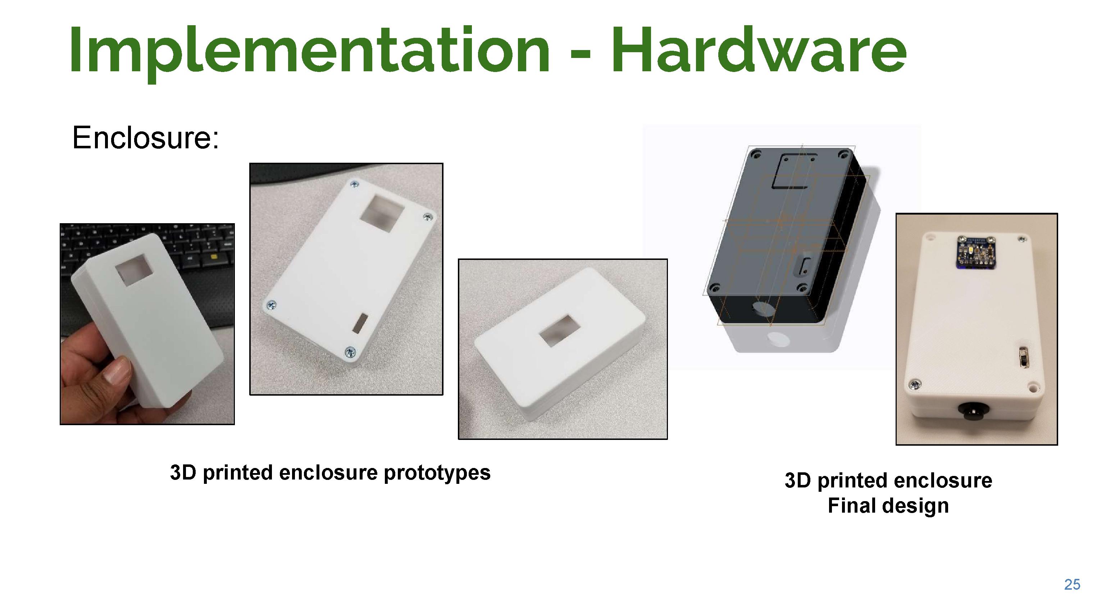
Misc/Presentation_Files/Presentation_Files-25.jpg
