jeffudall/Team14/Misc/Presentation_Files/Presentation_Files-26.jpg

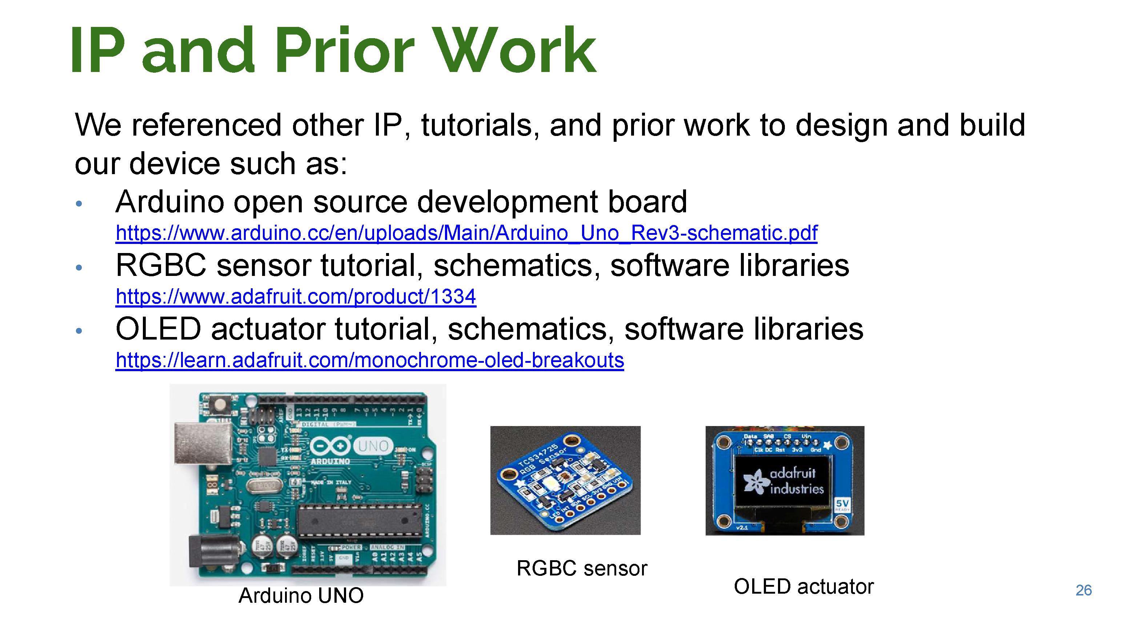
Misc/Presentation_Files/Presentation_Files-26.jpg
