jeffudall/Team14/Misc/Presentation_Files/Presentation_Files-27.jpg

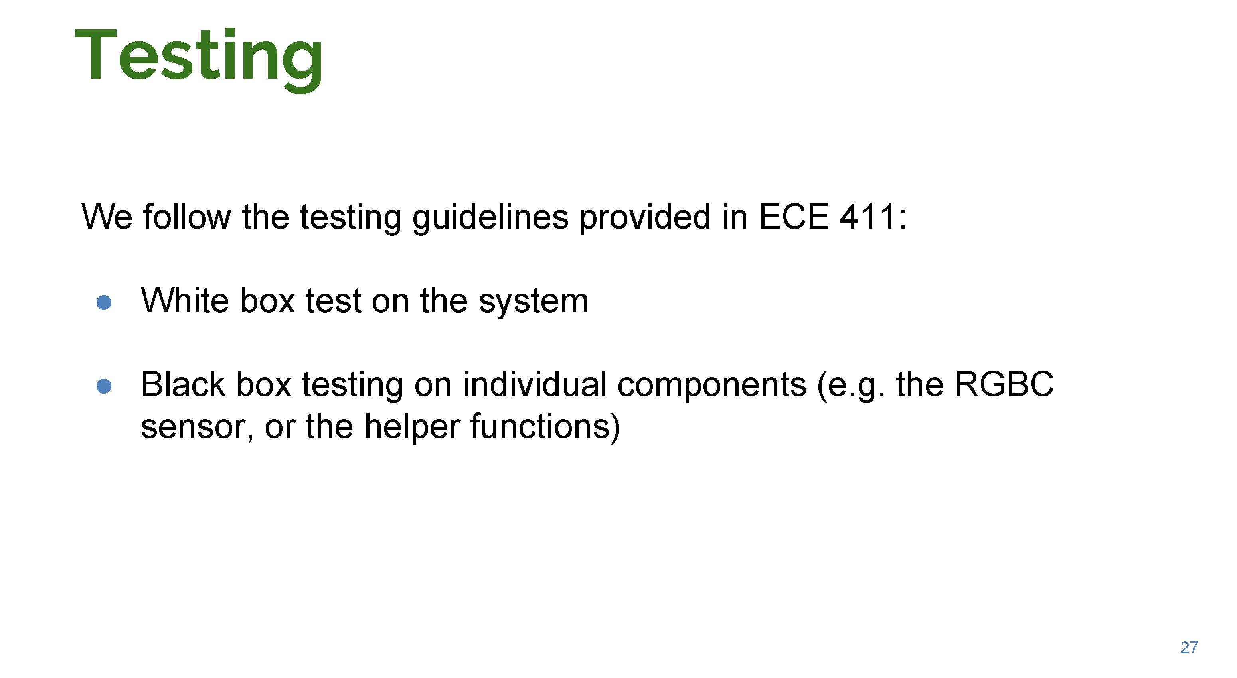
Misc/Presentation_Files/Presentation_Files-27.jpg
