jeffudall/Team14/Misc/Presentation_Files/Presentation_Files-28.jpg

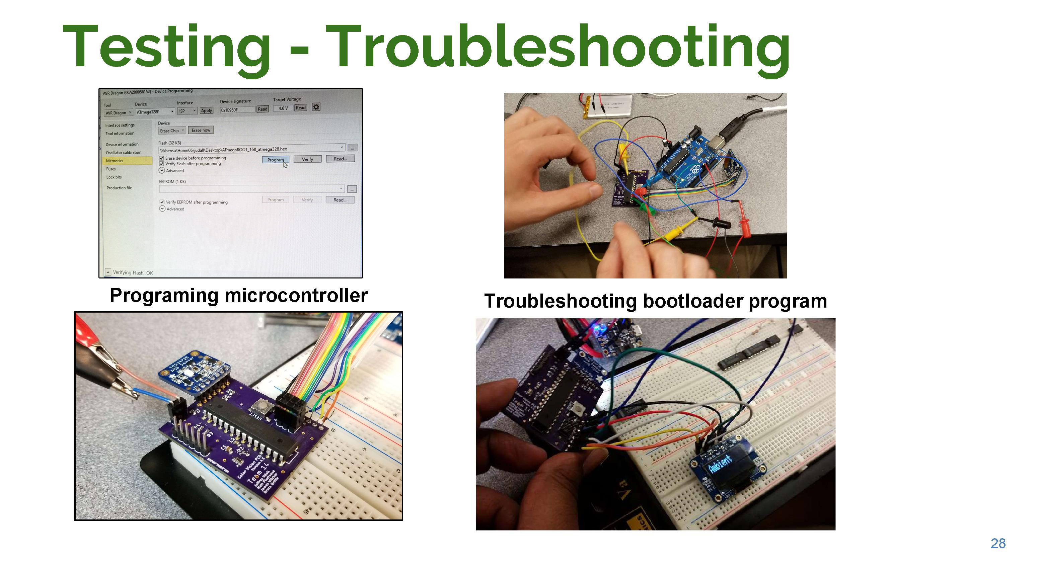
Misc/Presentation_Files/Presentation_Files-28.jpg
