jeffudall/Team14/Misc/Presentation_Files/Presentation_Files-29.jpg

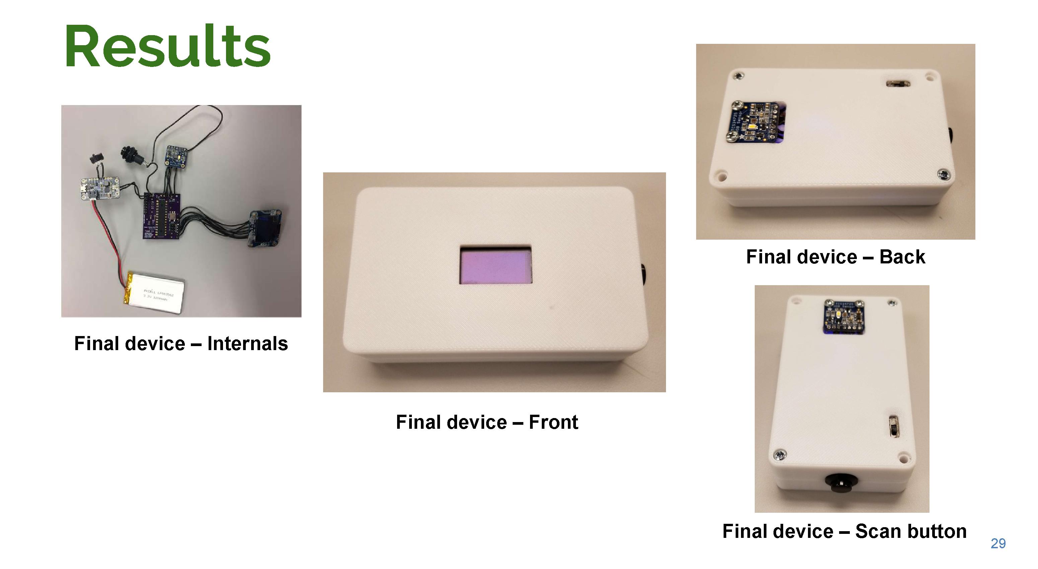
Misc/Presentation_Files/Presentation_Files-29.jpg
