jeffudall/Team14/Misc/Presentation_Files/Presentation_Files-30.jpg

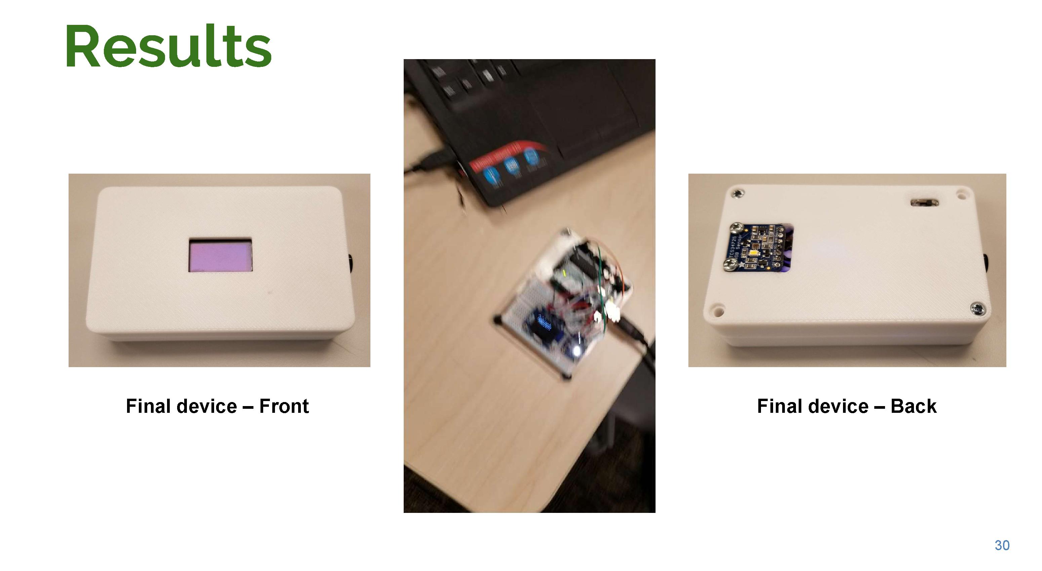
Misc/Presentation_Files/Presentation_Files-30.jpg
