jeffudall/Team14/Misc/Presentation_Files/Presentation_Files-31.jpg

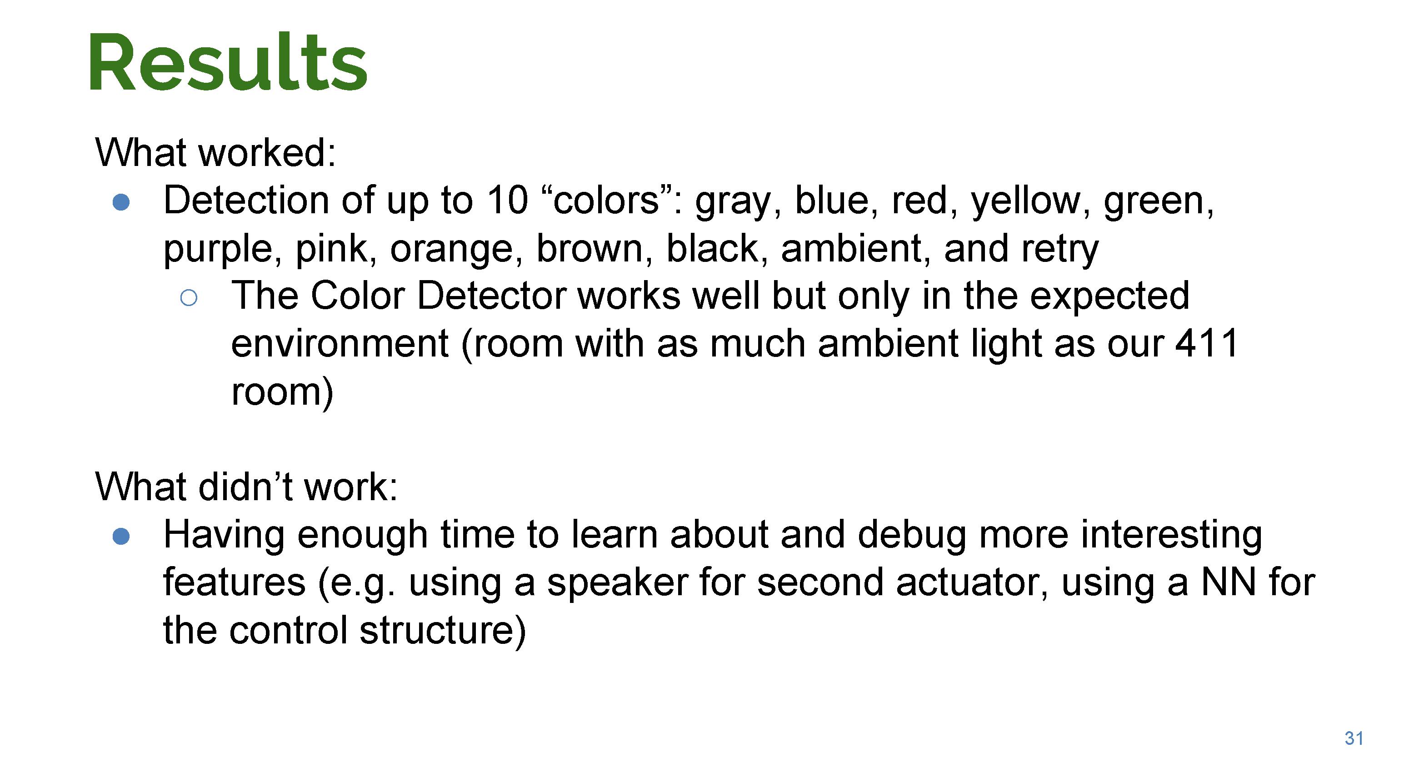
Misc/Presentation_Files/Presentation_Files-31.jpg
