jeffudall/Team14/Misc/Presentation_Files/Presentation_Files-32.jpg

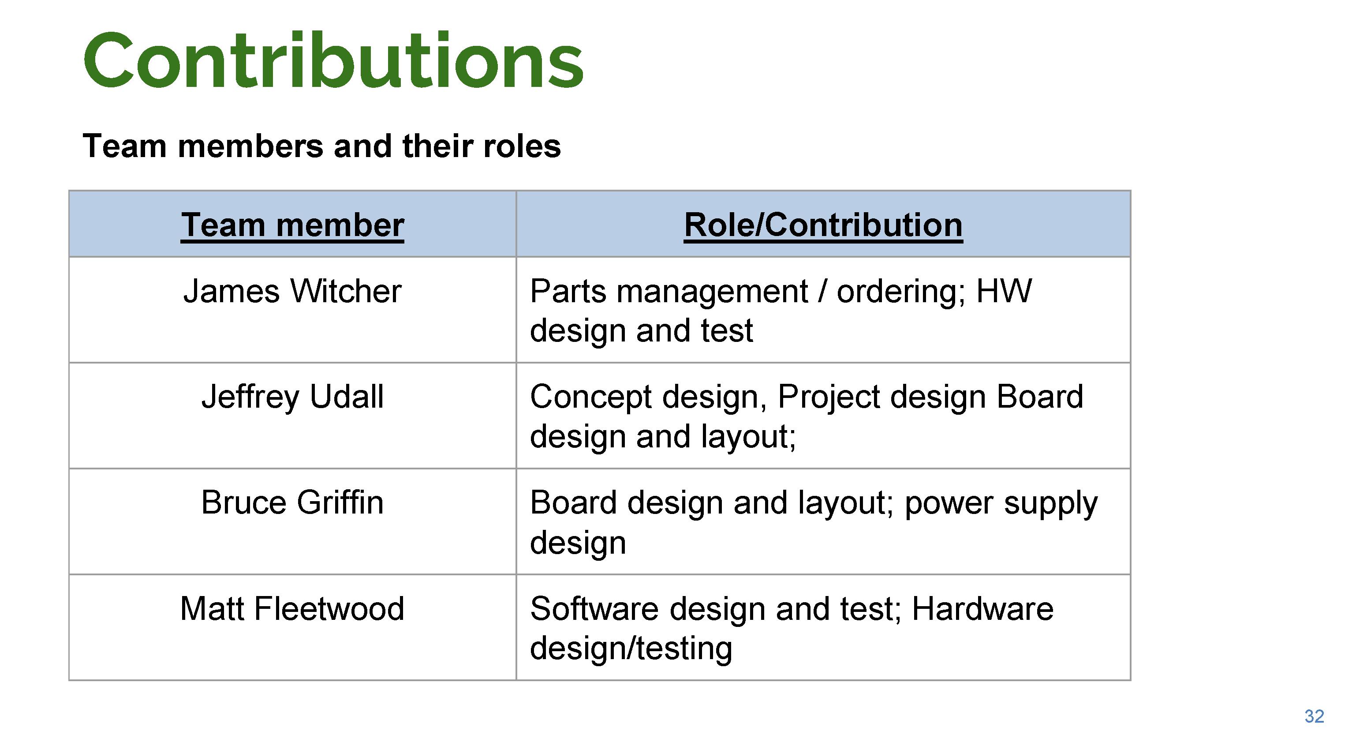
Misc/Presentation_Files/Presentation_Files-32.jpg
