jeffudall/Team14/Misc/Presentation_Files/Presentation_Files-33.jpg

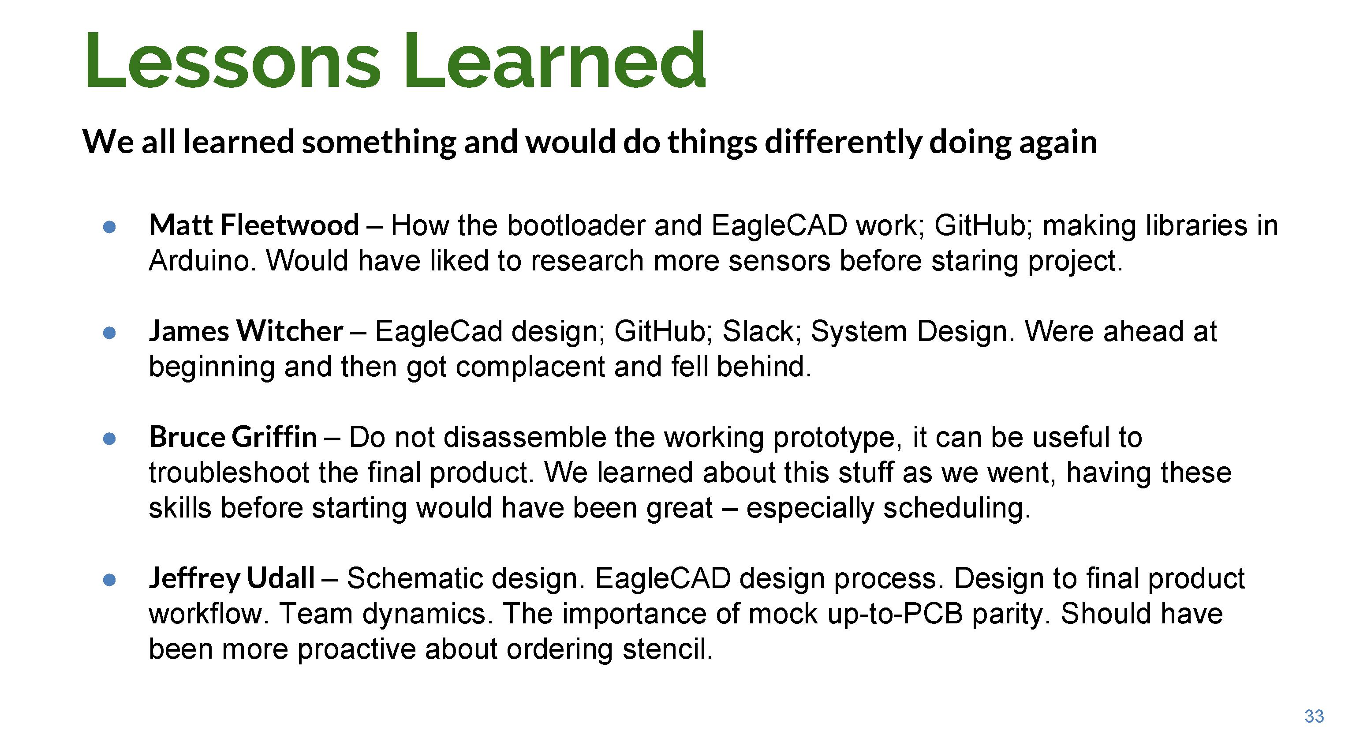
Misc/Presentation_Files/Presentation_Files-33.jpg
