jeffudall/Team14/Misc/Presentation_Files/Presentation_Files.jpg

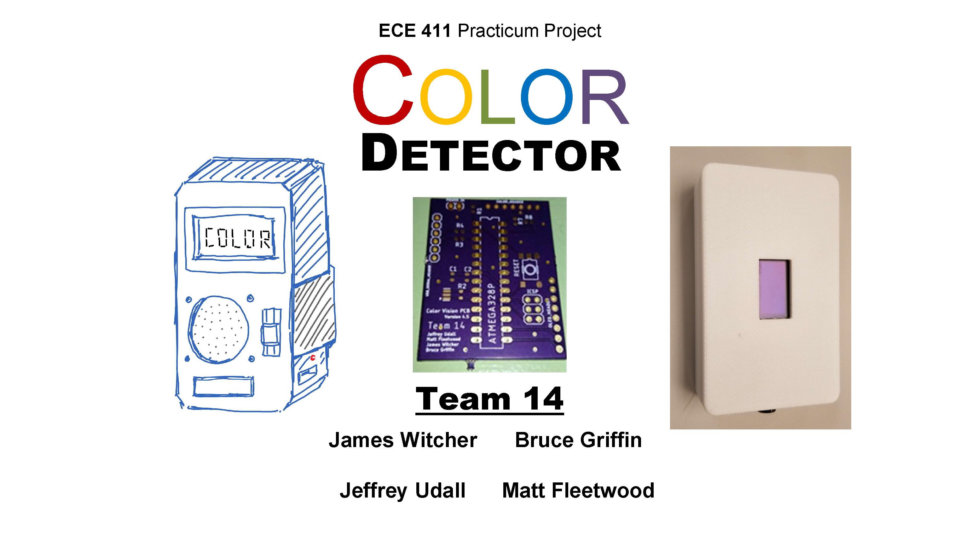
Misc/Presentation_Files/Presentation_Files.jpg
