jeffudall/Team14/images/Programing chip/Troubleshooting/Pasted image at 2017_12_02 11_15 AM.png

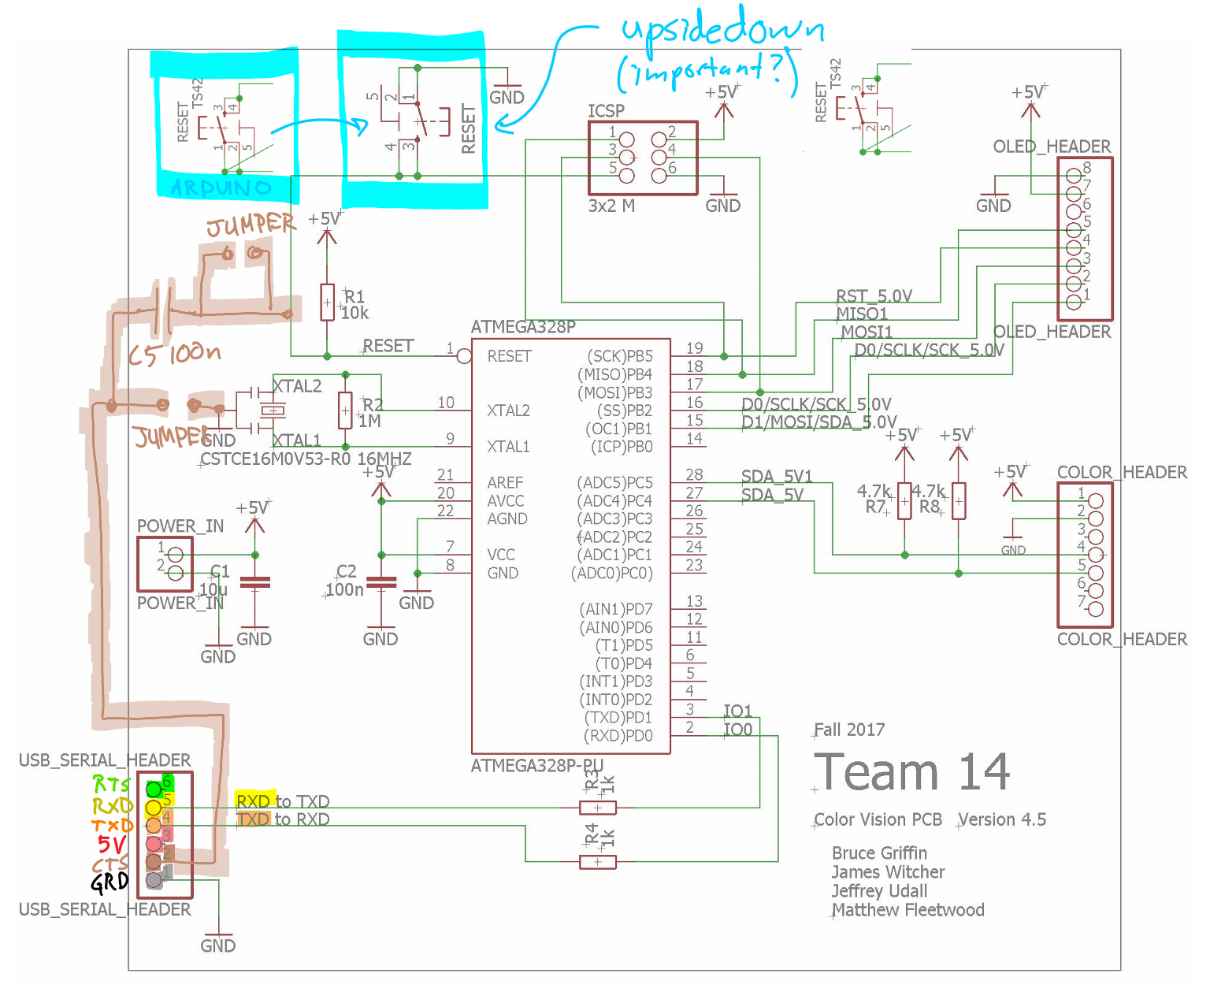
images/Programing chip/Troubleshooting/Pasted image at 2017_12_02 11_15 AM.png
