jeffudall/Team14/images/Programing chip/Troubleshooting/Pasted image at 2017_12_03 10_18 AM.png

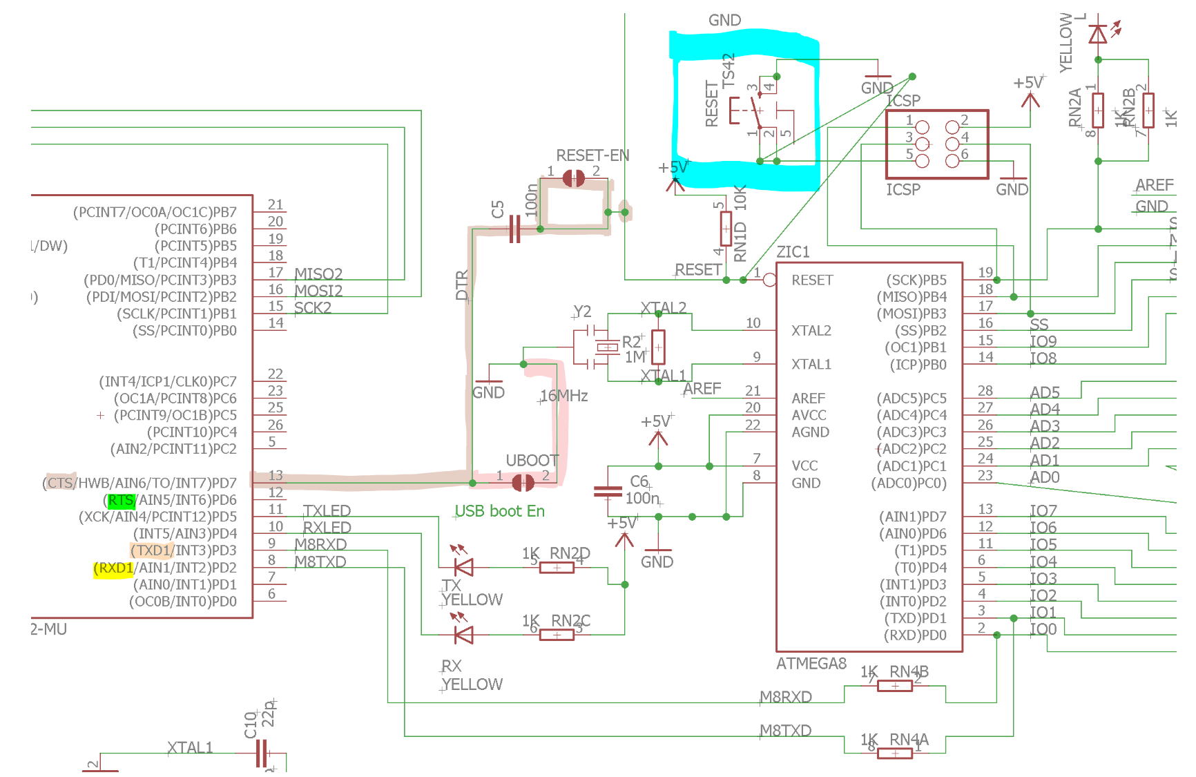
images/Programing chip/Troubleshooting/Pasted image at 2017_12_03 10_18 AM.png
