jeffudall/Team14/images/Programing chip/Troubleshooting/Pasted image at 2017_12_03 11_08 AM.png

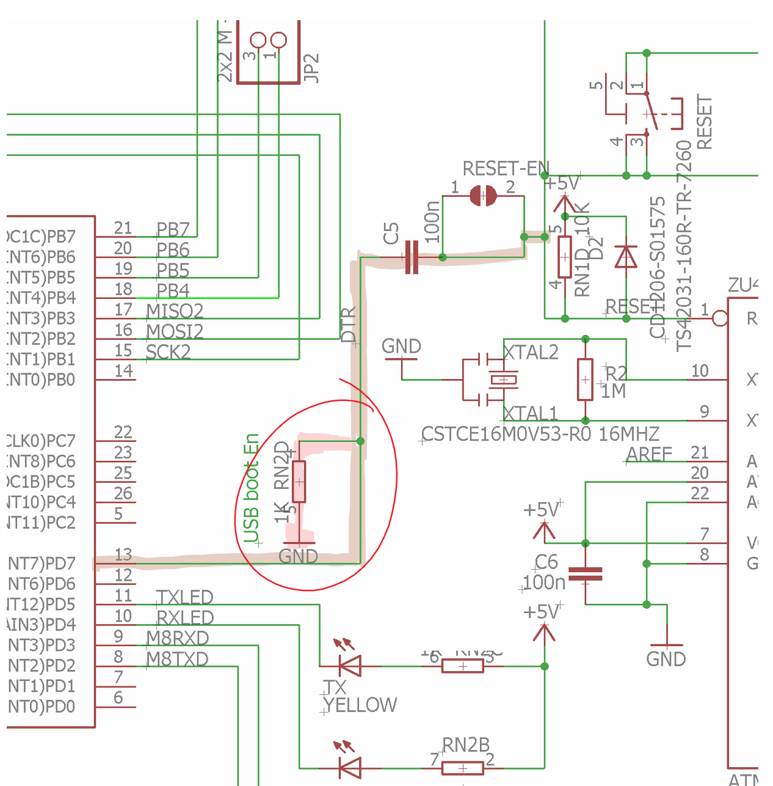
images/Programing chip/Troubleshooting/Pasted image at 2017_12_03 11_08 AM.png
